fachat/cbm_ultipet/Board/A%2fV.kicad_sch

## KiCad design Board/A%2fV.kicad_sch (2025-08-31)

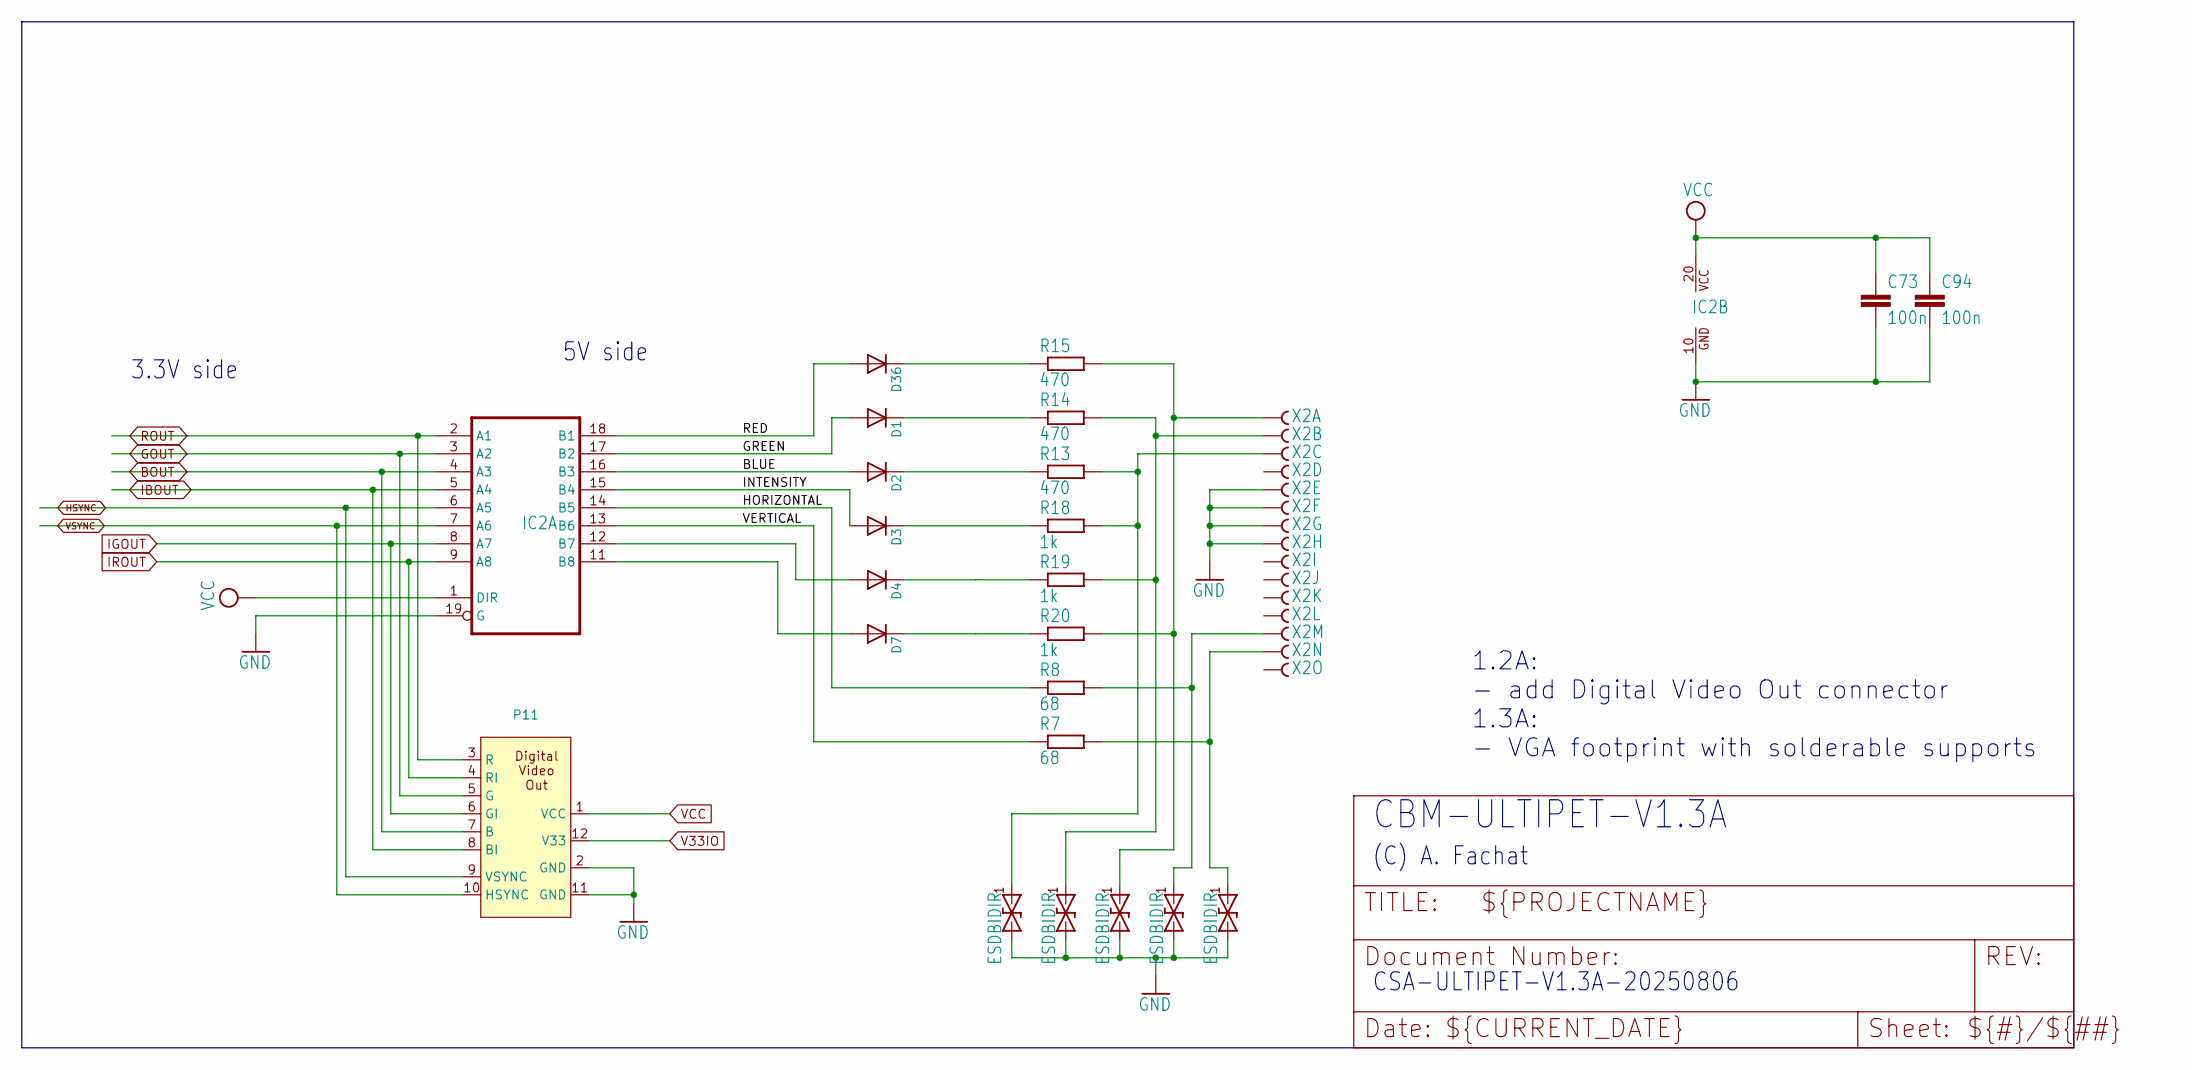
[picture p23: schematic A%2fV.kicad_sch]

Parts:
C73, C94: 100n; C025-025X050
D1, D2, D3, D4, D7, D36: 1N4448; D_DO-35_SOD27_P7.62mm_Horizontal
IC2: 74245DW; SOP-20_7.5x12.8mm_P1.27mm
P11: PinHeader_2x06_P2.54mm_Vertical
R7, R8: 68; 0204V
R13, R14, R15: 470; 0204V
R18, R19, R20: 1k; 0204V
UX5, UX6, UX8, UX10, UX11: ESDBIDIR; SOD323
X2: D-SUB15-HDR15RA; DSUB-15-HD_Socket_Horizontal_P2.29x2.54mm_EdgePinOffset8.35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

Connections:
BLUE: D2.2 (A), IC2.16 (B3)
BOUT: IC2.4 (A3), P11.7 (B)
GND: C73.2, C94.2, IC2.10 (GND), IC2.19 (G), P11.2 (GND), P11.11 (GND), UX5.1 (2), UX6.1 (2), UX8.1 (2), UX10.1 (2), UX11.1 (2), X2.5, X2.6, X2.7, X2.8
GOUT: IC2.3 (A2), P11.5 (G)
GREEN: D1.2 (A), IC2.17 (B2)
HORIZONTAL: IC2.14 (B5), R8.1
HSYNC: IC2.6 (A5), P11.9 (VSYNC)
IBOUT: IC2.5 (A4), P11.8 (BI)
IGOUT: IC2.8 (A7), P11.6 (GI)
INTENSITY: D3.2 (A), IC2.15 (B4)
IROUT: IC2.9 (A8), P11.4 (RI)
unnamed: D1.1 (K), R14.1
unnamed: D2.1 (K), R13.1
unnamed: D3.1 (K), R18.1
unnamed: D4.1 (K), R19.1
unnamed: D4.2 (A), IC2.12 (B7)
unnamed: D7.1 (K), R20.1
unnamed: D7.2 (A), IC2.11 (B8)
unnamed: D36.1 (K), R15.1
unnamed: R7.2, UX5.2 (1), X2.14
unnamed: R8.2, UX6.2 (1), X2.13
unnamed: R13.2, R18.2, UX11.2 (1), X2.3
unnamed: R14.2, R19.2, UX10.2 (1), X2.2
unnamed: R15.2, R20.2, UX8.2 (1), X2.1
RED: D36.2 (A), IC2.18 (B1)
ROUT: IC2.2 (A1), P11.3 (R)
V33IO: P11.12 (V33)
VCC: C73.1, C94.1, IC2.1 (DIR), IC2.20 (VCC), P11.1 (VCC)
VERTICAL: IC2.13 (B6), R7.1
VSYNC: IC2.7 (A6), P11.10 (HSYNC)

Notes on the sheet:
1.2A: - add Digital Video Out connector 1.3A: - VGA footprint with solderable supports
5V side
3.3V side
CSA-ULTIPET-V1.3A-20250806
CBM-ULTIPET-V1.3A
(C) A. Fachat
