fachat/cbm_ultipet/Board/Bus.kicad_sch

## KiCad design Board/Bus.kicad_sch (2025-08-31)

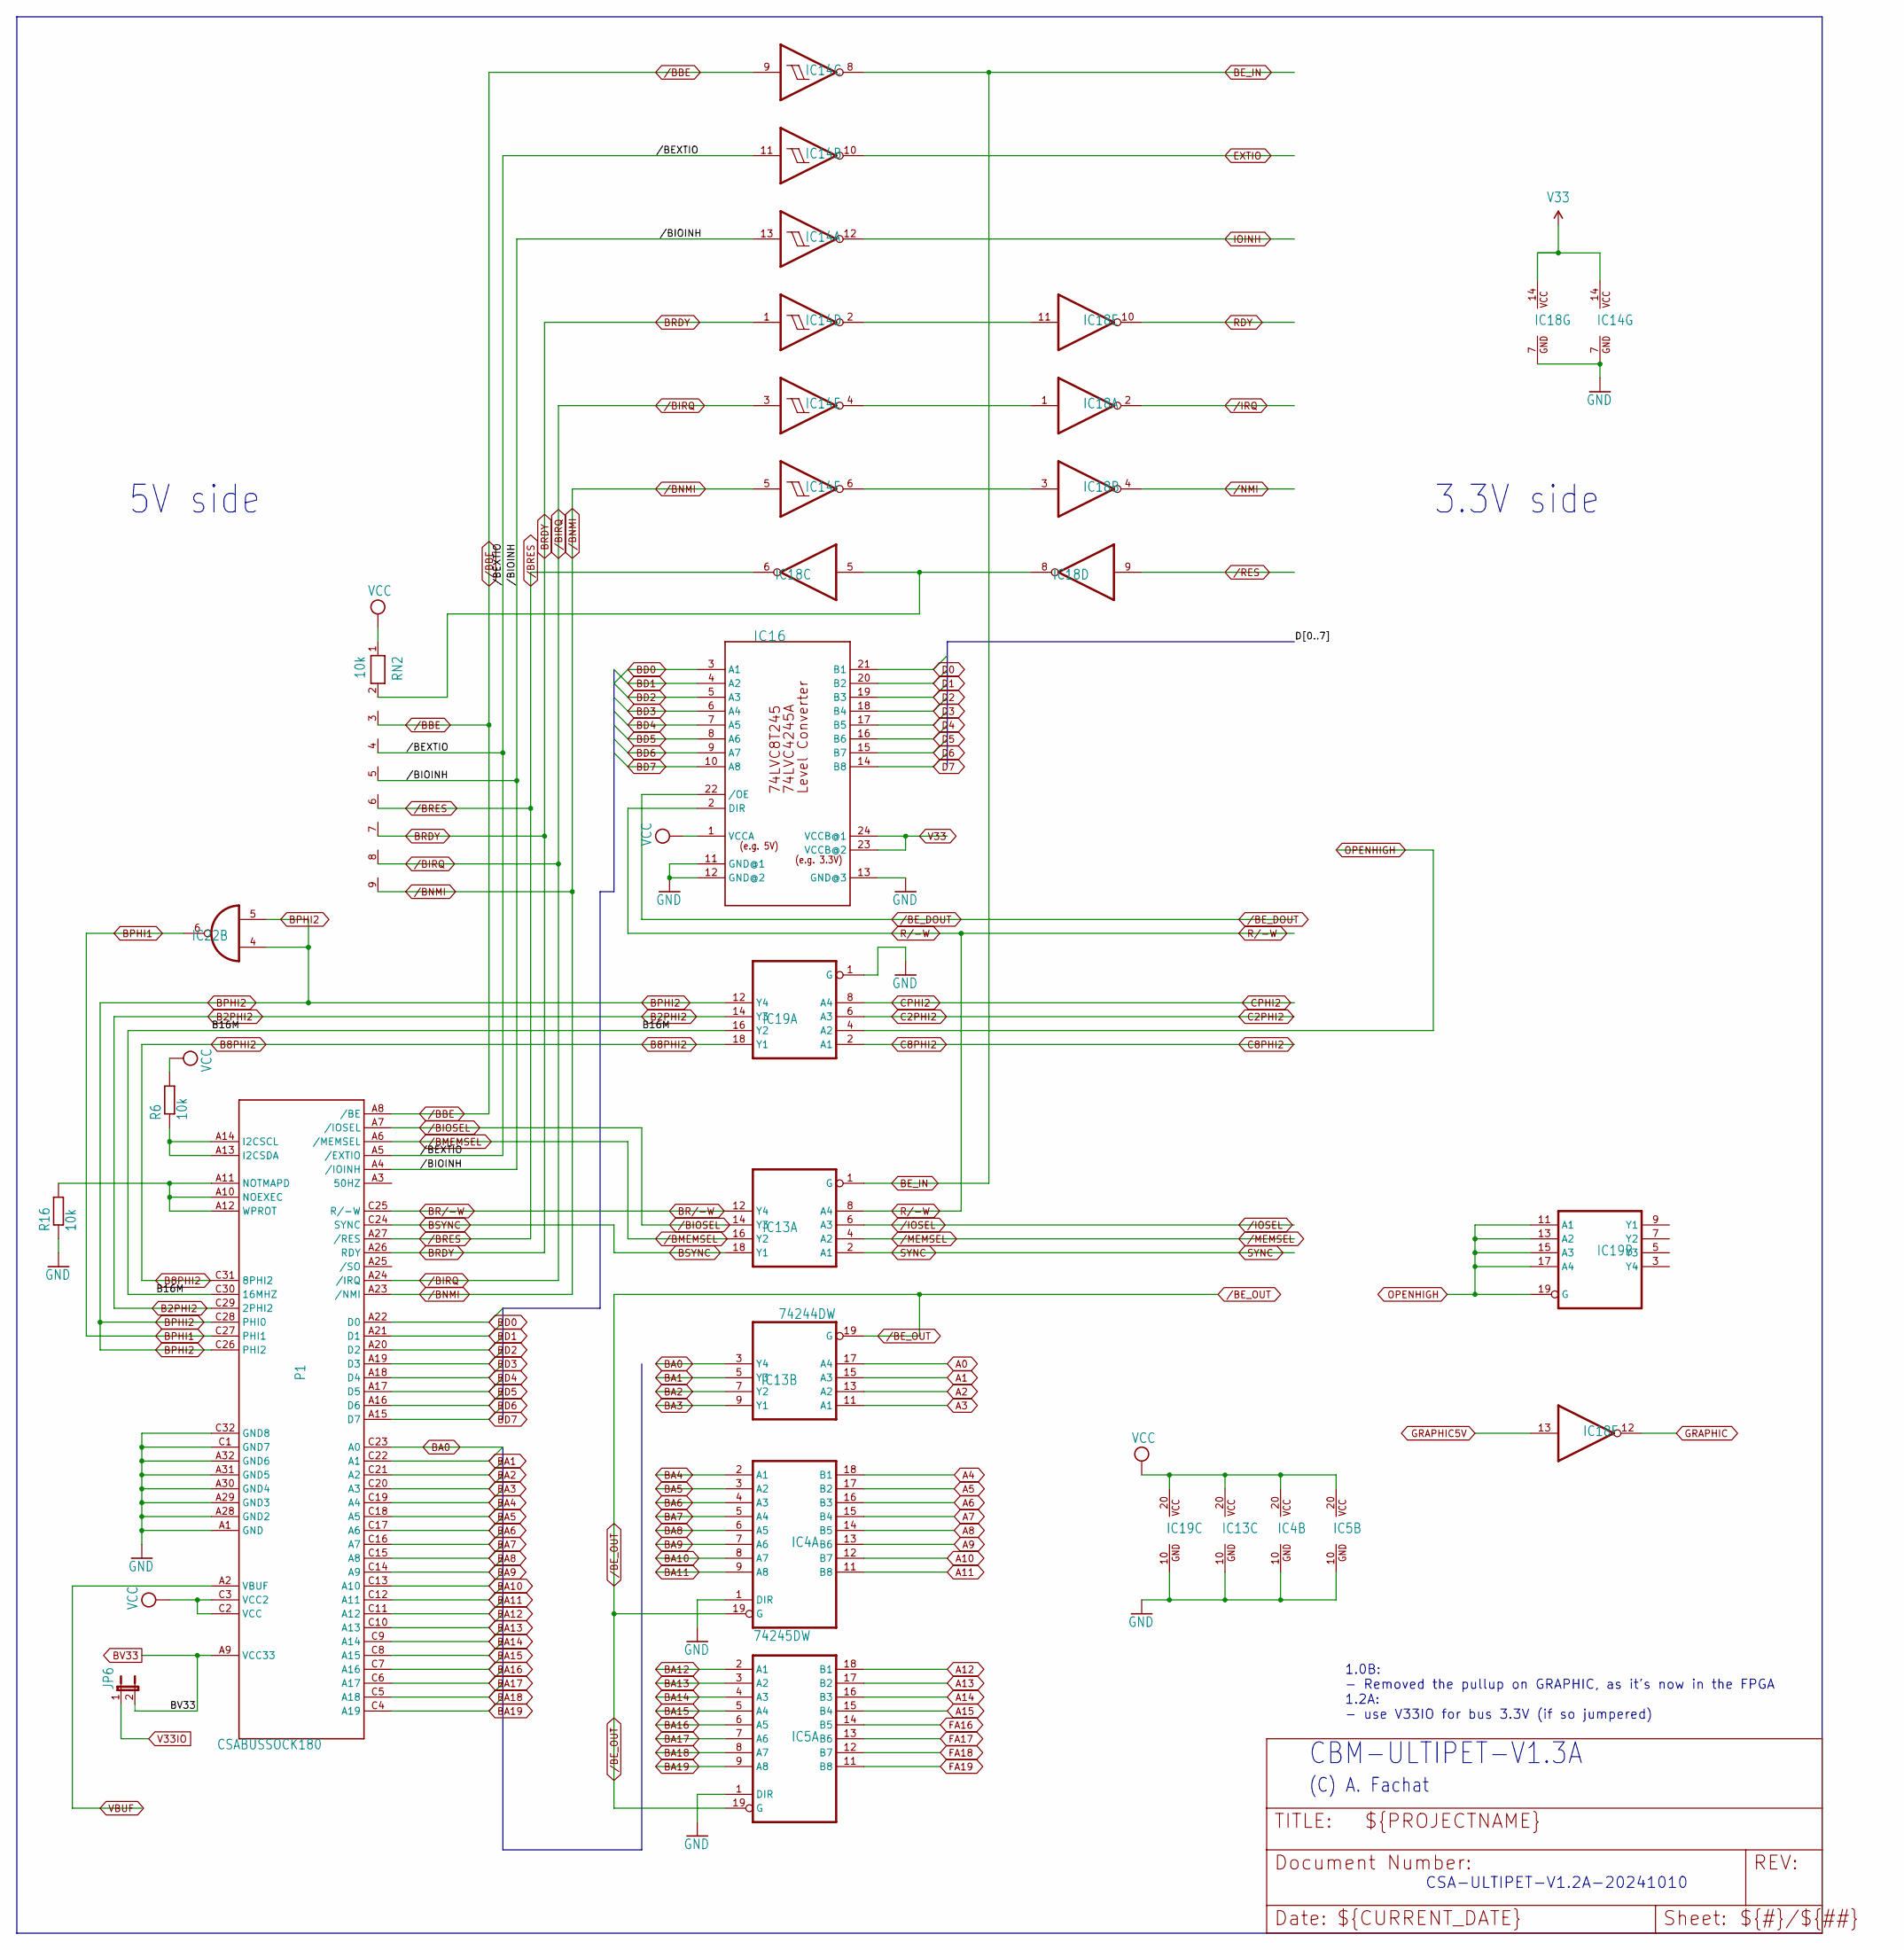
[picture p24: schematic Bus.kicad_sch]

Parts:
IC4, IC5: 74245DW; SOP-20_7.5x12.8mm_P1.27mm
IC13, IC19: 74244DW; SOP-20_7.5x12.8mm_P1.27mm
IC14: 74LVC14; SO14
IC16: 74LVC8T245SO24; SO24L
IC18: 74LVC06; SO14
IC22: 7400N; DIP-14_W7.62mm_Socket_LongPads
JP6: JP1E; JP1
P1: CSABUSSOCK180
R6, R16: 10k; 0204_5
RN2: 10k; RN-9

Connections:
/BBE: IC14.9 (I), P1.A8 (/BE), RN2.3
/BEXTIO: IC14.11 (I), P1.A5 (/EXTIO), RN2.4
/BE_DOUT: IC16.22 (/OE)
/BE_OUT: IC4.19 (G), IC5.19 (G), IC13.19 (G)
/BIOINH: IC14.13 (I), P1.A4 (/IOINH), RN2.5
/BIOSEL: IC13.14 (Y3), P1.A7 (/IOSEL)
/BIRQ: IC14.3 (I), P1.A24 (/IRQ), RN2.8
/BMEMSEL: IC13.16 (Y2), P1.A6 (/MEMSEL)
/BNMI: IC14.5 (I), P1.A23 (/NMI), RN2.9
/BRES: IC18.6 (O), P1.A27 (/RES), RN2.6
/IOSEL: IC13.6 (A3)
/IRQ: IC18.2 (O)
/MEMSEL: IC13.4 (A2)
/NMI: IC18.4 (O)
/RES: IC18.9 (I)
A0: IC13.17 (A4)
A1: IC13.15 (A3)
A2: IC13.13 (A2)
A3: IC13.11 (A1)
A4: IC4.18 (B1)
A5: IC4.17 (B2)
A6: IC4.16 (B3)
A7: IC4.15 (B4)
A8: IC4.14 (B5)
A9: IC4.13 (B6)
A10: IC4.12 (B7)
A11: IC4.11 (B8)
A12: IC5.18 (B1)
A13: IC5.17 (B2)
A14: IC5.16 (B3)
A15: IC5.15 (B4)
B2PHI2: IC19.14 (Y3), P1.C29 (2PHI2)
B8PHI2: IC19.18 (Y1), P1.C31 (8PHI2)
B16M: IC19.16 (Y2), P1.C30 (16MHZ)
BA0: IC13.3 (Y4), P1.C23 (A0)
BA1: IC13.5 (Y3), P1.C22 (A1)
BA2: IC13.7 (Y2), P1.C21 (A2)
BA3: IC13.9 (Y1), P1.C20 (A3)
BA4: IC4.2 (A1), P1.C19 (A4)
BA5: IC4.3 (A2), P1.C18 (A5)
BA6: IC4.4 (A3), P1.C17 (A6)
BA7: IC4.5 (A4), P1.C16 (A7)
BA8: IC4.6 (A5), P1.C15 (A8)
BA9: IC4.7 (A6), P1.C14 (A9)
BA10: IC4.8 (A7), P1.C13 (A10)
BA11: IC4.9 (A8), P1.C12 (A11)
BA12: IC5.2 (A1), P1.C11 (A12)
BA13: IC5.3 (A2), P1.C10 (A13)
BA14: IC5.4 (A3), P1.C9 (A14)
BA15: IC5.5 (A4), P1.C8 (A15)
BA16: IC5.6 (A5), P1.C7 (A16)
BA17: IC5.7 (A6), P1.C6 (A17)
BA18: IC5.8 (A7), P1.C5 (A18)
BA19: IC5.9 (A8), P1.C4 (A19)
BD0: IC16.3 (A1), P1.A22 (D0)
BD1: IC16.4 (A2), P1.A21 (D1)
BD2: IC16.5 (A3), P1.A20 (D2)
BD3: IC16.6 (A4), P1.A19 (D3)
BD4: IC16.7 (A5), P1.A18 (D4)
BD5: IC16.8 (A6), P1.A17 (D5)
BD6: IC16.9 (A7), P1.A16 (D6)
BD7: IC16.10 (A8), P1.A15 (D7)
BE_IN: IC13.1 (G), IC14.8 (O)
BPHI1: IC22.6 (O), P1.C27 (PHI1)
BPHI2: IC19.12 (Y4), IC22.4 (I0), IC22.5 (I1), P1.C26 (PHI2), P1.C28 (PHI0)
BR/-W: IC13.12 (Y4), P1.C25 (R/-W)
BRDY: IC14.1 (I), P1.A26 (RDY), RN2.7
BSYNC: IC13.18 (Y1), P1.C24 (SYNC)
BV33: JP6.2, P1.A9 (VCC33)
C2PHI2: IC19.6 (A3)
C8PHI2: IC19.2 (A1)
CPHI2: IC19.8 (A4)
D0: IC16.21 (B1)
D1: IC16.20 (B2)
D2: IC16.19 (B3)
D3: IC16.18 (B4)
D4: IC16.17 (B5)
D5: IC16.16 (B6)
D6: IC16.15 (B7)
D7: IC16.14 (B8)
EXTIO: IC14.10 (O)
FA16: IC5.14 (B5)
FA17: IC5.13 (B6)
FA18: IC5.12 (B7)
FA19: IC5.11 (B8)
GND: IC4.1 (DIR), IC4.10 (GND), IC5.1 (DIR), IC5.10 (GND), IC13.10 (GND), IC14.7 (GND), IC16.11 (GND@1), IC16.12 (GND@2), IC16.13 (GND@3), IC18.7 (GND), IC19.1 (G), IC19.10 (GND), P1.A1 (GND), P1.A28 (GND2), P1.A29 (GND3), P1.A30 (GND4), P1.A31 (GND5), P1.A32 (GND6), P1.C1 (GND7), P1.C32 (GND8), R16.1
GRAPHIC: IC18.12 (O)
GRAPHIC5V: IC18.13 (I)
IOINH: IC14.12 (O)
unnamed: IC14.2 (O), IC18.11 (I)
unnamed: IC14.4 (O), IC18.1 (I)
unnamed: IC14.6 (O), IC18.3 (I)
unnamed: IC18.5 (I), IC18.8 (O), RN2.2
unnamed: P1.A10 (NOEXEC), P1.A11 (NOTMAPD), P1.A12 (WPROT), R16.2
unnamed: P1.A13 (I2CSDA), P1.A14 (I2CSCL), R6.1
OPENHIGH: IC19.4 (A2), IC19.11 (A1), IC19.13 (A2), IC19.15 (A3), IC19.17 (A4), IC19.19 (G)
R/-W: IC13.8 (A4), IC16.2 (DIR)
RDY: IC18.10 (O)
SYNC: IC13.2 (A1)
V33: IC14.14 (VCC), IC16.23 (VCCB@2), IC16.24 (VCCB@1), IC18.14 (VCC)
V33IO: JP6.1
VBUF: P1.A2 (VBUF)
VCC: IC4.20 (VCC), IC5.20 (VCC), IC13.20 (VCC), IC16.1 (VCCA), IC19.20 (VCC), P1.C2 (VCC), P1.C3 (VCC2), R6.2, RN2.1

Notes on the sheet:
CSA-ULTIPET-V1.2A-20241010
5V side
(C) A. Fachat
3.3V side
1.0B: - Removed the pullup on GRAPHIC, as it's now in the FPGA 1.2A: - use V33IO for bus 3.3V (if so jumpered)
CBM-ULTIPET-V1.3A
