fachat/cbm_ultipet/Board/CPU,_FPGA,_FRAM.kicad_sch

## KiCad design Board/CPU,_FPGA,_FRAM.kicad_sch (2026-05-08)

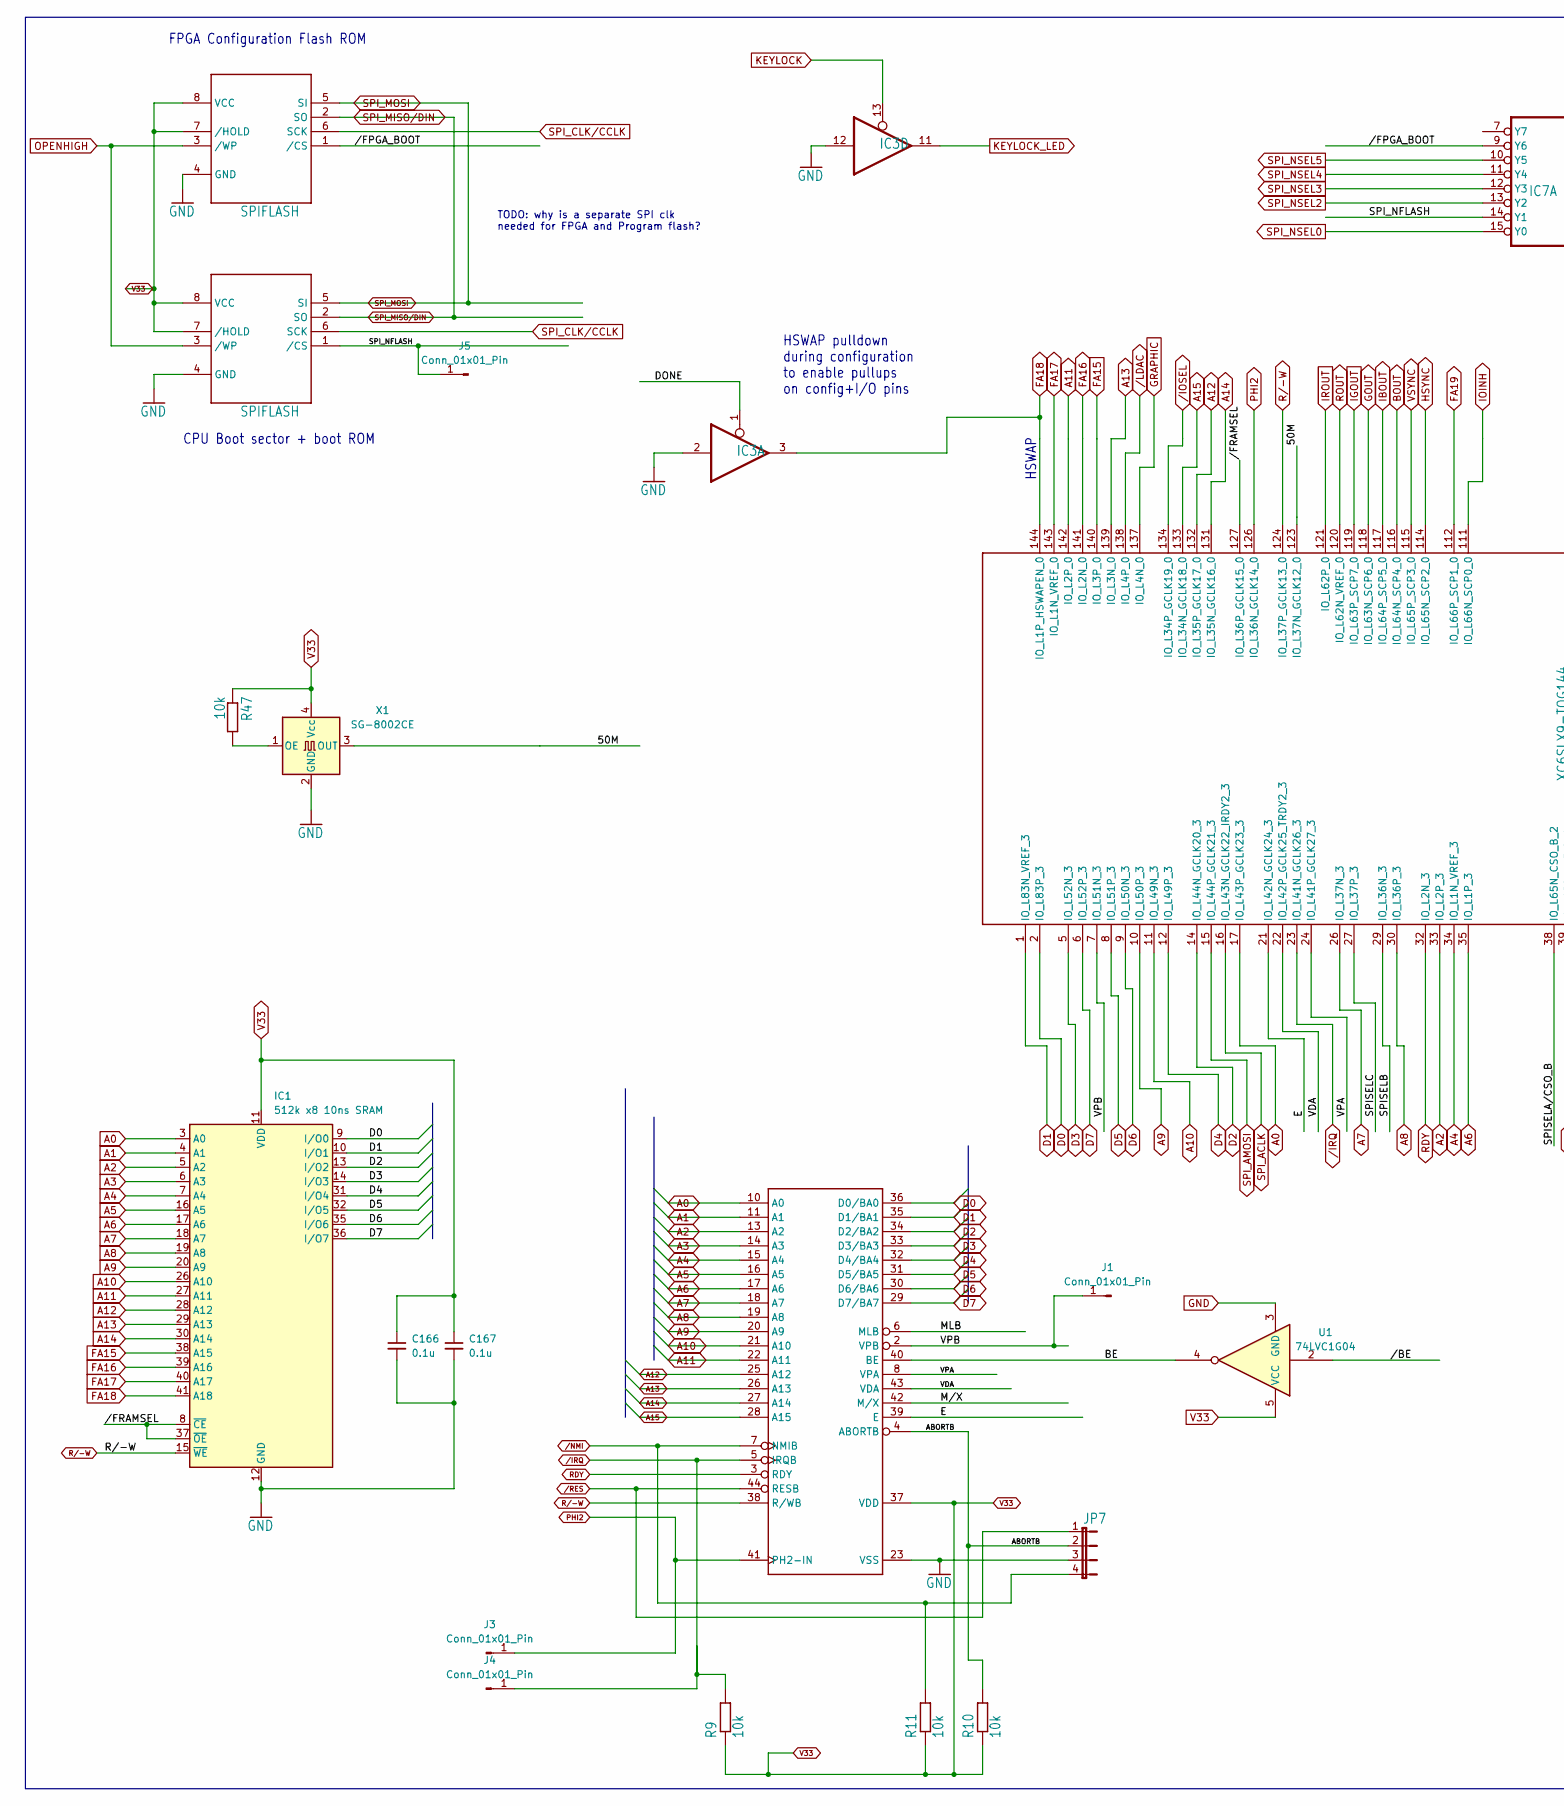
[picture p25: schematic CPU,_FPGA,_FRAM.kicad_sch, part in row 1, column 1]

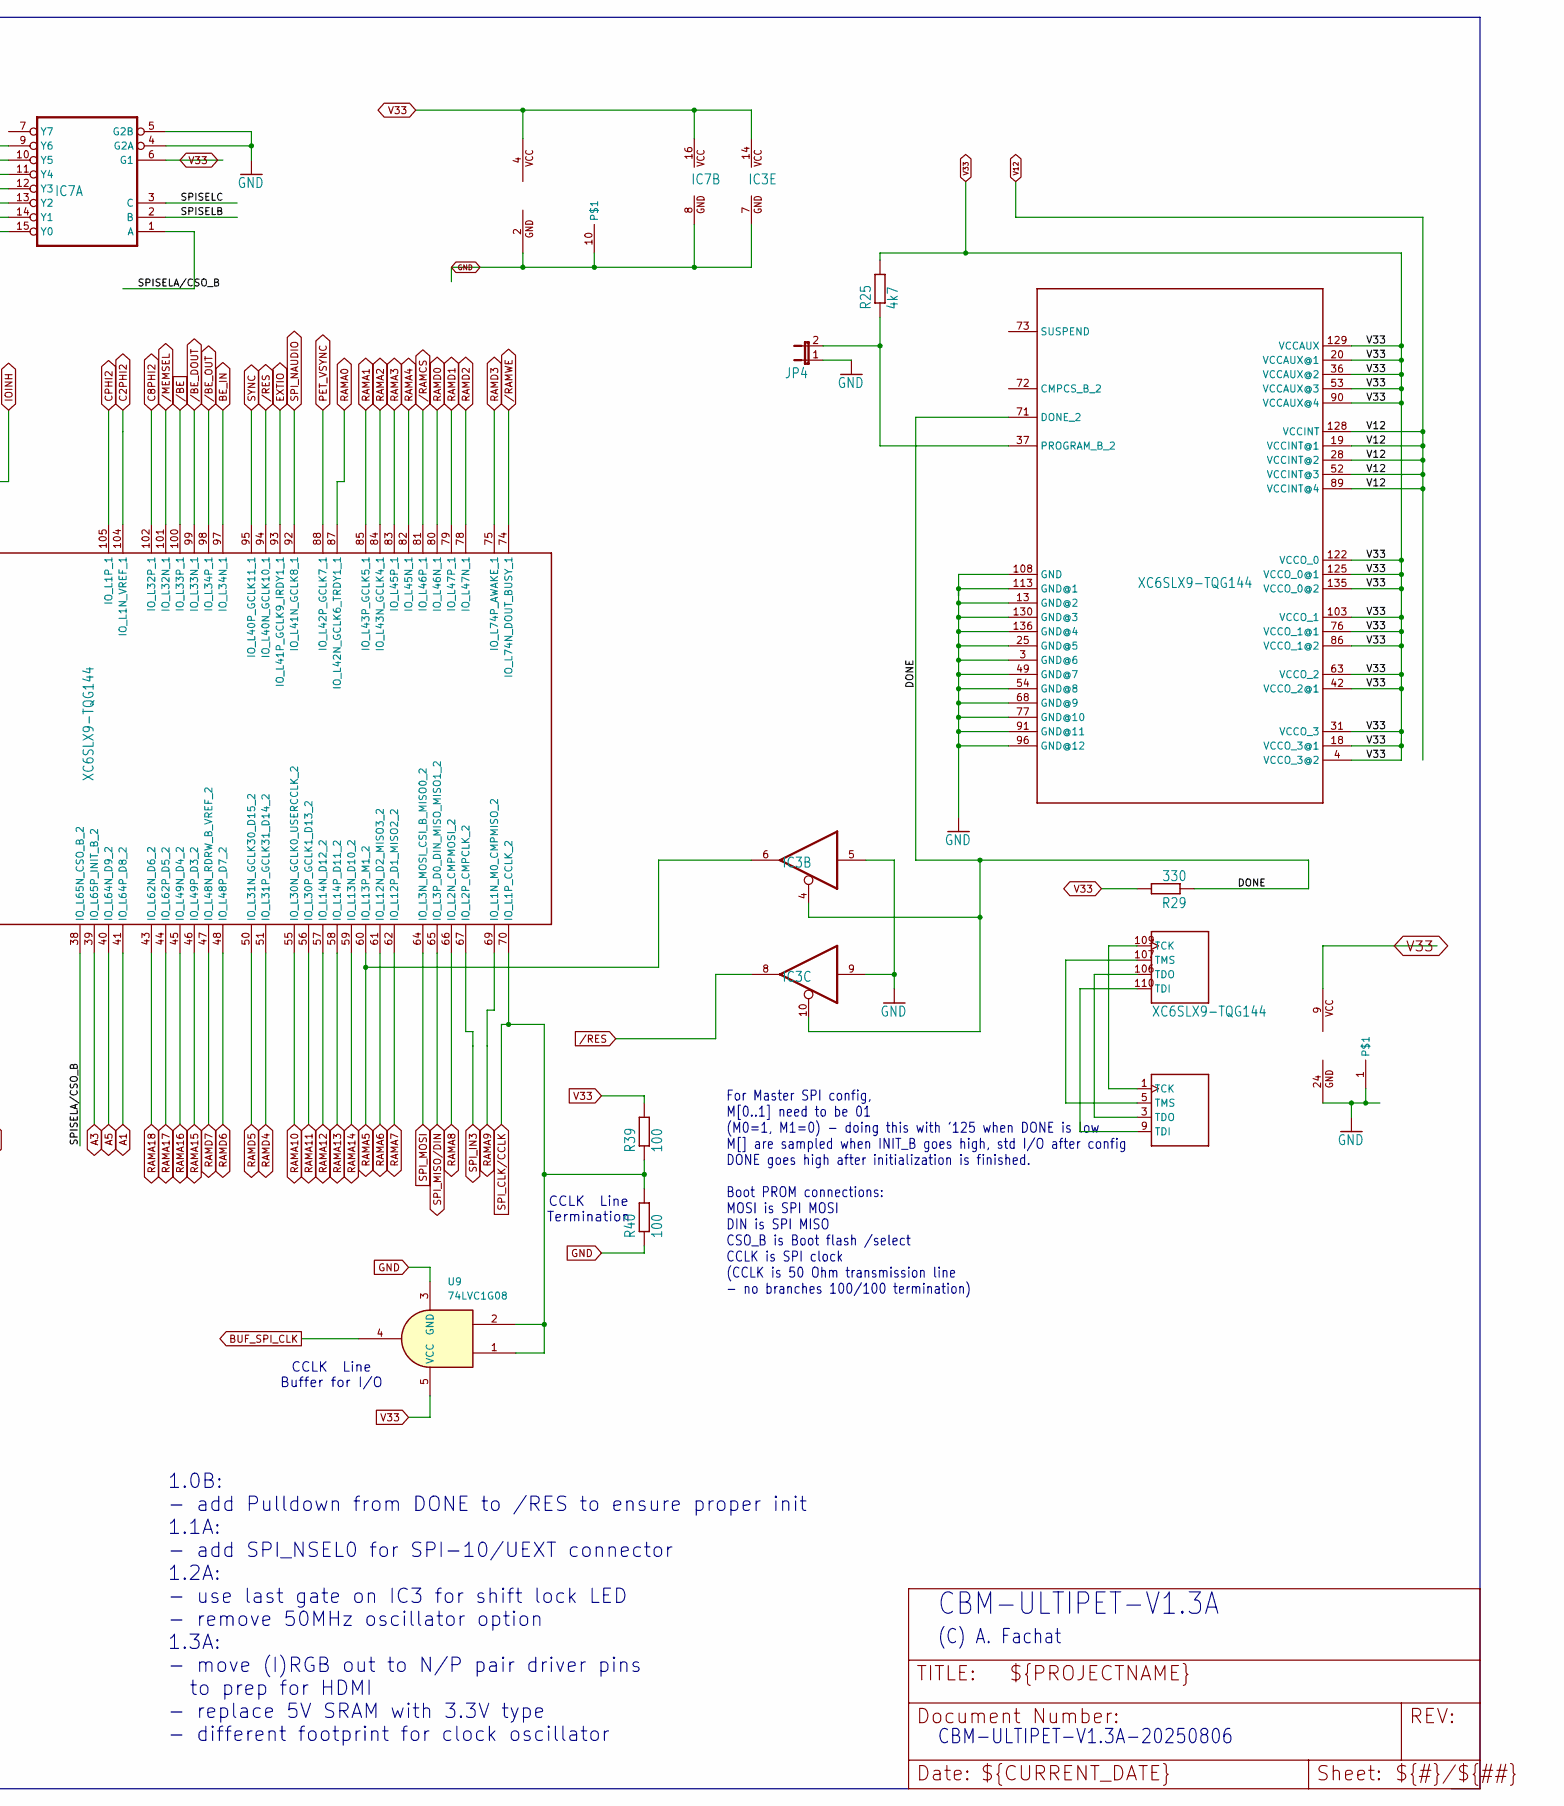
[picture p26: schematic CPU,_FPGA,_FRAM.kicad_sch, part in row 1, column 2]

Parts:
C166, C167: 0.1u; C_0603_1608Metric
IC1: 512k x8 10ns SRAM; TSOP-II-44_10.16x18.41mm_P0.8mm
IC3: 74LVC125D; SO14@1
IC7: 74LVC138D; SO16
J1, J3, J4, J5: Conn_01x01_Pin; PinHeader_1x01_P2.54mm_Vertical
JP4: JP1E; JP1
JP7: JP4E; JP4
R9, R10, R11: 10k; 0207_2V
R25: 4k7; 0207_2V
R29: 330; 0207_2V
R39, R40: 100; 0207_2V
R47: 10k; R_0805_2012Metric_Pad1.20x1.40mm_HandSolder
U1: 74LVC1G04; SOT-23-5
U9: 74LVC1G08; SOT-23-5
UX1: W65C816SPLCC; PLCC-44_THT-Socket
UX4, UX18: SPIFLASH; DIP-8_W7.62mm_Socket_LongPads
UX7: XILINXPROG; FLAT10BOX
UX19: XC6SLX9-TQG144; TQFP-144_20x20mm_P0.5mm
X1: SG-8002CE; Oscillator_SMD_SeikoEpson_SG8002CE-4Pin_3.2x2.5mm

Connections:
50M: UX19.123 (IO_L37N_GCLK12_0), X1.3 (OUT)
/BE_DOUT: UX19.99 (IO_L33N_1)
/BE_OUT: UX19.98 (IO_L34P_1)
/FPGA_BOOT: IC7.9 (Y6), UX18.1 (/CS)
/FRAMSEL: UX19.127 (IO_L36P_GCLK15_0)
/IOSEL: UX19.134 (IO_L34P_GCLK19_0)
/IRQ: J4.1, R9.2, UX1.5 (IRQB), UX19.23 (IO_L41N_GCLK26_3)
/LDAC: UX19.138 (IO_L4P_0)
/MEMSEL: UX19.101 (IO_L32N_1)
/NMI: JP7.4, R11.2, UX1.7 (NMIB)
/RAMWE: UX19.74 (IO_L74N_DOUT_BUSY_1)
/RES: JP7.1, UX1.44 (RESB), UX19.94 (IO_L40N_GCLK10_1)
A0: IC1.3 (A0), UX1.10 (A0), UX19.17 (IO_L43P_GCLK23_3)
A1: IC1.4 (A1), UX1.11 (A1), UX19.41 (IO_L64P_D8_2)
A2: IC1.5 (A2), UX1.13 (A2), UX19.33 (IO_L2P_3)
A3: IC1.6 (A3), UX1.14 (A3), UX19.39 (IO_L65P_INIT_B_2)
A4: IC1.7 (A4), UX1.15 (A4), UX19.34 (IO_L1N_VREF_3)
A5: IC1.16 (A5), UX1.16 (A5), UX19.40 (IO_L64N_D9_2)
A6: IC1.17 (A6), UX1.17 (A6), UX19.35 (IO_L1P_3)
A7: IC1.18 (A7), UX1.18 (A7), UX19.26 (IO_L37N_3)
A8: IC1.19 (A8), UX1.19 (A8), UX19.30 (IO_L36P_3)
A9: IC1.20 (A9), UX1.20 (A9), UX19.10 (IO_L50P_3)
A10: IC1.26 (A10), UX1.21 (A10), UX19.11 (IO_L49N_3)
A11: IC1.27 (A11), UX1.22 (A11), UX19.142 (IO_L2P_0)
A12: IC1.28 (A12), UX1.25 (A12), UX19.132 (IO_L35P_GCLK17_0)
A13: IC1.29 (A13), UX1.26 (A13), UX19.139 (IO_L3N_0)
A14: IC1.30 (A14), UX1.27 (A14), UX19.131 (IO_L35N_GCLK16_0)
A15: UX1.28 (A15), UX19.133 (IO_L34N_GCLK18_0)
ABORTB: JP7.2, R10.2, UX1.4 (ABORTB)
BE: U1.4, UX1.40 (BE)
BE_IN: UX19.97 (IO_L34N_1)
BOUT: UX19.116 (IO_L64N_SCP4_0)
BUF_SPI_CLK: U9.4
C2PHI2: UX19.104 (IO_L1N_VREF_1)
C8PHI2: UX19.102 (IO_L32P_1)
CPHI2: UX19.105 (IO_L1P_1)
D0: IC1.9 (I/O0), UX1.36 (D0/BA0), UX19.2 (IO_L83P_3)
D1: IC1.10 (I/O1), UX1.35 (D1/BA1), UX19.1 (IO_L83N_VREF_3)
D2: IC1.13 (I/O2), UX1.34 (D2/BA2), UX19.14 (IO_L44N_GCLK20_3)
D3: IC1.14 (I/O3), UX1.33 (D3/BA3), UX19.5 (IO_L52N_3)
D4: IC1.31 (I/O4), UX1.32 (D4/BA4), UX19.12 (IO_L49P_3)
D5: IC1.32 (I/O5), UX1.31 (D5/BA5), UX19.8 (IO_L51P_3)
D6: IC1.35 (I/O6), UX1.30 (D6/BA6), UX19.9 (IO_L50N_3)
D7: IC1.36 (I/O7), UX1.29 (D7/BA7), UX19.6 (IO_L52P_3)
DONE: IC3.1 (OE), IC3.4 (OE), IC3.10 (OE), R29.1, UX19.71 (DONE_2)
E: UX1.39 (E), UX19.21 (IO_L42N_GCLK24_3)
EXTIO: UX19.93 (IO_L41P_GCLK9_IRDY1_1)
FA15: IC1.38 (A15), UX19.140 (IO_L3P_0)
FA16: IC1.39 (A16), UX19.141 (IO_L2N_0)
FA17: IC1.40 (A17), UX19.143 (IO_L1N_VREF_0)
FA18: IC1.41 (A18), IC3.3 (O), UX19.144 (IO_L1P_HSWAPEN_0)
FA19: UX19.112 (IO_L66P_SCP1_0)
GND: C166.2, C167.2, IC1.12 (GND), IC1.34 (GND), IC3.2 (I), IC3.5 (I), IC3.7 (GND), IC3.9 (I), IC3.12 (I), IC7.4 (G2A), IC7.5 (G2B), IC7.8 (GND), JP4.1, JP7.3, R40.1, U1.3 (GND), U9.3 (GND), UX1.1, UX1.23 (VSS), UX1.24 (GND), UX4.4 (GND), UX7.2 (GND), UX7.10, UX18.4 (GND), UX19.3 (GND@6), UX19.13 (GND@2), UX19.25 (GND@5), UX19.49 (GND@7), UX19.54 (GND@8), UX19.68 (GND@9), UX19.77 (GND@10), UX19.91 (GND@11), UX19.96 (GND@12), UX19.108 (GND), UX19.113 (GND@1), UX19.130 (GND@3), UX19.136 (GND@4), X1.2 (GND)
GOUT: UX19.118 (IO_L63N_SCP6_0)
GRAPHIC: UX19.137 (IO_L4N_0)
HSYNC: UX19.114 (IO_L65N_SCP2_0)
IBOUT: UX19.117 (IO_L64P_SCP5_0)
IGOUT: UX19.119 (IO_L63P_SCP7_0)
IOINH: UX19.111 (IO_L66N_SCP0_0)
IROUT: UX19.121 (IO_L62P_0)
KEYLOCK: IC3.13 (OE)
KEYLOCK_LED: IC3.11 (O)
MLB: UX1.6 (MLB)
M/X: UX1.42 (M/X)
unnamed: JP4.2, R25.1, UX19.37 (PROGRAM_B_2)
unnamed: R47.2, X1.1 (OE)
unnamed: UX7.3 (TDO), UX19.106 (TDO)
unnamed: UX7.5 (TMS), UX19.107 (TMS)
unnamed: UX7.1 (TCK), UX19.109 (TCK)
unnamed: UX7.9 (TDI), UX19.110 (TDI)
OPENHIGH: UX4.3 (/WP), UX18.3 (/WP)
PET_VSYNC: UX19.88 (IO_L42P_GCLK7_1)
PHI2: J3.1, UX1.41 (PH2-IN), UX19.126 (IO_L36N_GCLK14_0)
R/-W: IC1.15 (~WE), UX1.38 (R/WB), UX19.124 (IO_L37P_GCLK13_0)
RAMA0: UX19.87 (IO_L42N_GCLK6_TRDY1_1)
RAMA1: UX19.85 (IO_L43P_GCLK5_1)
RAMA2: UX19.84 (IO_L43N_GCLK4_1)
RAMA3: UX19.83 (IO_L45P_1)
RAMA4: UX19.82 (IO_L45N_1)
RAMA5: IC3.6 (O), UX19.60 (IO_L13P_M1_2)
RAMA6: UX19.61 (IO_L12N_D2_MISO3_2)
RAMA7: UX19.62 (IO_L12P_D1_MISO2_2)
RAMA8: UX19.66 (IO_L2N_CMPMOSI_2)
RAMA9: UX19.69 (IO_L1N_M0_CMPMISO_2)
RAMA10: UX19.55 (IO_L30N_GCLK0_USERCCLK_2)
RAMA11: UX19.56 (IO_L30P_GCLK1_D13_2)
RAMA12: UX19.57 (IO_L14N_D12_2)
RAMA13: UX19.58 (IO_L14P_D11_2)
RAMA14: UX19.59 (IO_L13N_D10_2)
RAMA15: UX19.46 (IO_L49P_D3_2)
RAMA16: UX19.45 (IO_L49N_D4_2)
RAMA17: UX19.44 (IO_L62P_D5_2)
RAMA18: UX19.43 (IO_L62N_D6_2)
RAMD0: UX19.80 (IO_L46N_1)
RAMD1: UX19.79 (IO_L47P_1)
RAMD2: UX19.78 (IO_L47N_1)
RAMD3: UX19.75 (IO_L74P_AWAKE_1)
RAMD4: UX19.51 (IO_L31P_GCLK31_D14_2)
RAMD5: UX19.50 (IO_L31N_GCLK30_D15_2)
RAMD6: UX19.48 (IO_L48P_D7_2)
RAMD7: UX19.47 (IO_L48N_RDRW_B_VREF_2)
RDY: UX1.3 (RDY), UX19.32 (IO_L2N_3)
ROUT: UX19.120 (IO_L62N_VREF_0)
SPISELA/CSO_B: IC7.1 (A), UX19.38 (IO_L65N_CSO_B_2)
SPISELB: IC7.2 (B), UX19.29 (IO_L36N_3)
SPISELC: IC7.3 (C), UX19.27 (IO_L37P_3)
SPI_ACLK: UX19.16 (IO_L43N_GCLK22_IRDY2_3)
SPI_AMOSI: UX19.15 (IO_L44P_GCLK21_3)
SPI_CLK/CCLK: R39.1, R40.2, U9.1, U9.2, UX18.6 (SCK), UX19.70 (IO_L1P_CCLK_2)
SPI_CLK/CCLK: UX4.6 (SCK)
SPI_IN3: UX19.67 (IO_L2P_CMPCLK_2)
SPI_MISO/DIN: UX4.2 (SO), UX18.2 (SO), UX19.65 (IO_L3P_D0_DIN_MISO_MISO1_2)
SPI_MOSI: UX4.5 (SI), UX18.5 (SI), UX19.64 (IO_L3N_MOSI_CSI_B_MISO0_2)
SPI_NAUDIO: UX19.92 (IO_L41N_GCLK8_1)
SPI_NFLASH: IC7.14 (Y1), J5.1, UX4.1 (/CS)
SPI_NSEL0: IC7.15 (Y0)
SPI_NSEL2: IC7.13 (Y2)
SPI_NSEL3: IC7.12 (Y3)
SPI_NSEL4: IC7.11 (Y4)
SPI_NSEL5: IC7.10 (Y5)
SYNC: UX19.95 (IO_L40P_GCLK11_1)
V12: UX19.19 (VCCINT@1), UX19.28 (VCCINT@2), UX19.52 (VCCINT@3), UX19.89 (VCCINT@4), UX19.128 (VCCINT)
V33: C166.1, C167.1, IC1.11 (VDD), IC1.33 (VDD), IC3.14 (VCC), IC7.6 (G1), IC7.16 (VCC), R9.1, R10.1, R11.1, R25.2, R29.2, R39.2, R47.1, U1.5 (VCC), U9.5 (VCC), UX1.9 (VCC), UX1.37 (VDD), UX4.7 (/HOLD), UX4.8 (VCC), UX7.4 (VCC), UX18.7 (/HOLD), UX18.8 (VCC), UX19.4 (VCCO_3@2), UX19.18 (VCCO_3@1), UX19.20 (VCCAUX@1), UX19.31 (VCCO_3), UX19.36 (VCCAUX@2), UX19.42 (VCCO_2@1), UX19.53 (VCCAUX@3), UX19.63 (VCCO_2), UX19.76 (VCCO_1@1), UX19.86 (VCCO_1@2), UX19.90 (VCCAUX@4), UX19.103 (VCCO_1), UX19.122 (VCCO_0), UX19.125 (VCCO_0@1), UX19.129 (VCCAUX), UX19.135 (VCCO_0@2), X1.4 (Vcc)
VDA: UX1.43 (VDA), UX19.22 (IO_L42P_GCLK25_TRDY2_3)
VPA: UX1.8 (VPA), UX19.24 (IO_L41P_GCLK27_3)
VPB: J1.1, UX1.2 (VPB), UX19.7 (IO_L51N_3)
VSYNC: UX19.115 (IO_L65P_SCP3_0)
/BE: U1.2, UX19.100 (IO_L33P_1)
/FRAMSEL: IC1.8 (~CE), IC1.37 (~OE)
/RAMCS: UX19.81 (IO_L46P_1)
/RES: IC3.8 (O)

Notes on the sheet:
TODO: why is a separate SPI clk needed for FPGA and Program flash?
CPU Boot sector + boot ROM
1.0B: - add Pulldown from DONE to /RES to ensure proper init 1.1A: - add SPI_NSEL0 for SPI-10/UEXT connector 1.2A: - use last gate on IC3 for shift lock LED - remove 50MHz oscillator option 1.3A: - move (I)RGB out to N/P pair driver pins to prep for HDMI - replace 5V SRAM with 3.3V type - different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
CCLK Line Termination
CBM-ULTIPET-V1.3A
CBM-ULTIPET-V1.3A-20250806
CCLK Line Buffer for I/O
(C) A. Fachat
HSWAP pulldown during configuration to enable pullups on config+I/O pins
For Master SPI config, M[0..1] need to be 01 (M0=1, M1=0) - doing this with '125 when DONE is low M[] are sampled when INIT_B goes high, std I/O after config DONE goes high after initialization is finished. Boot PROM connections: MOSI is SPI MOSI DIN is SPI MISO CSO_B is Boot flash /select CCLK is 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
HSWAP
FPGA Configuration Flash ROM
