fachat/cbm_ultipet/Board/FastIEC.kicad_sch

## KiCad design Board/FastIEC.kicad_sch (2025-08-31)

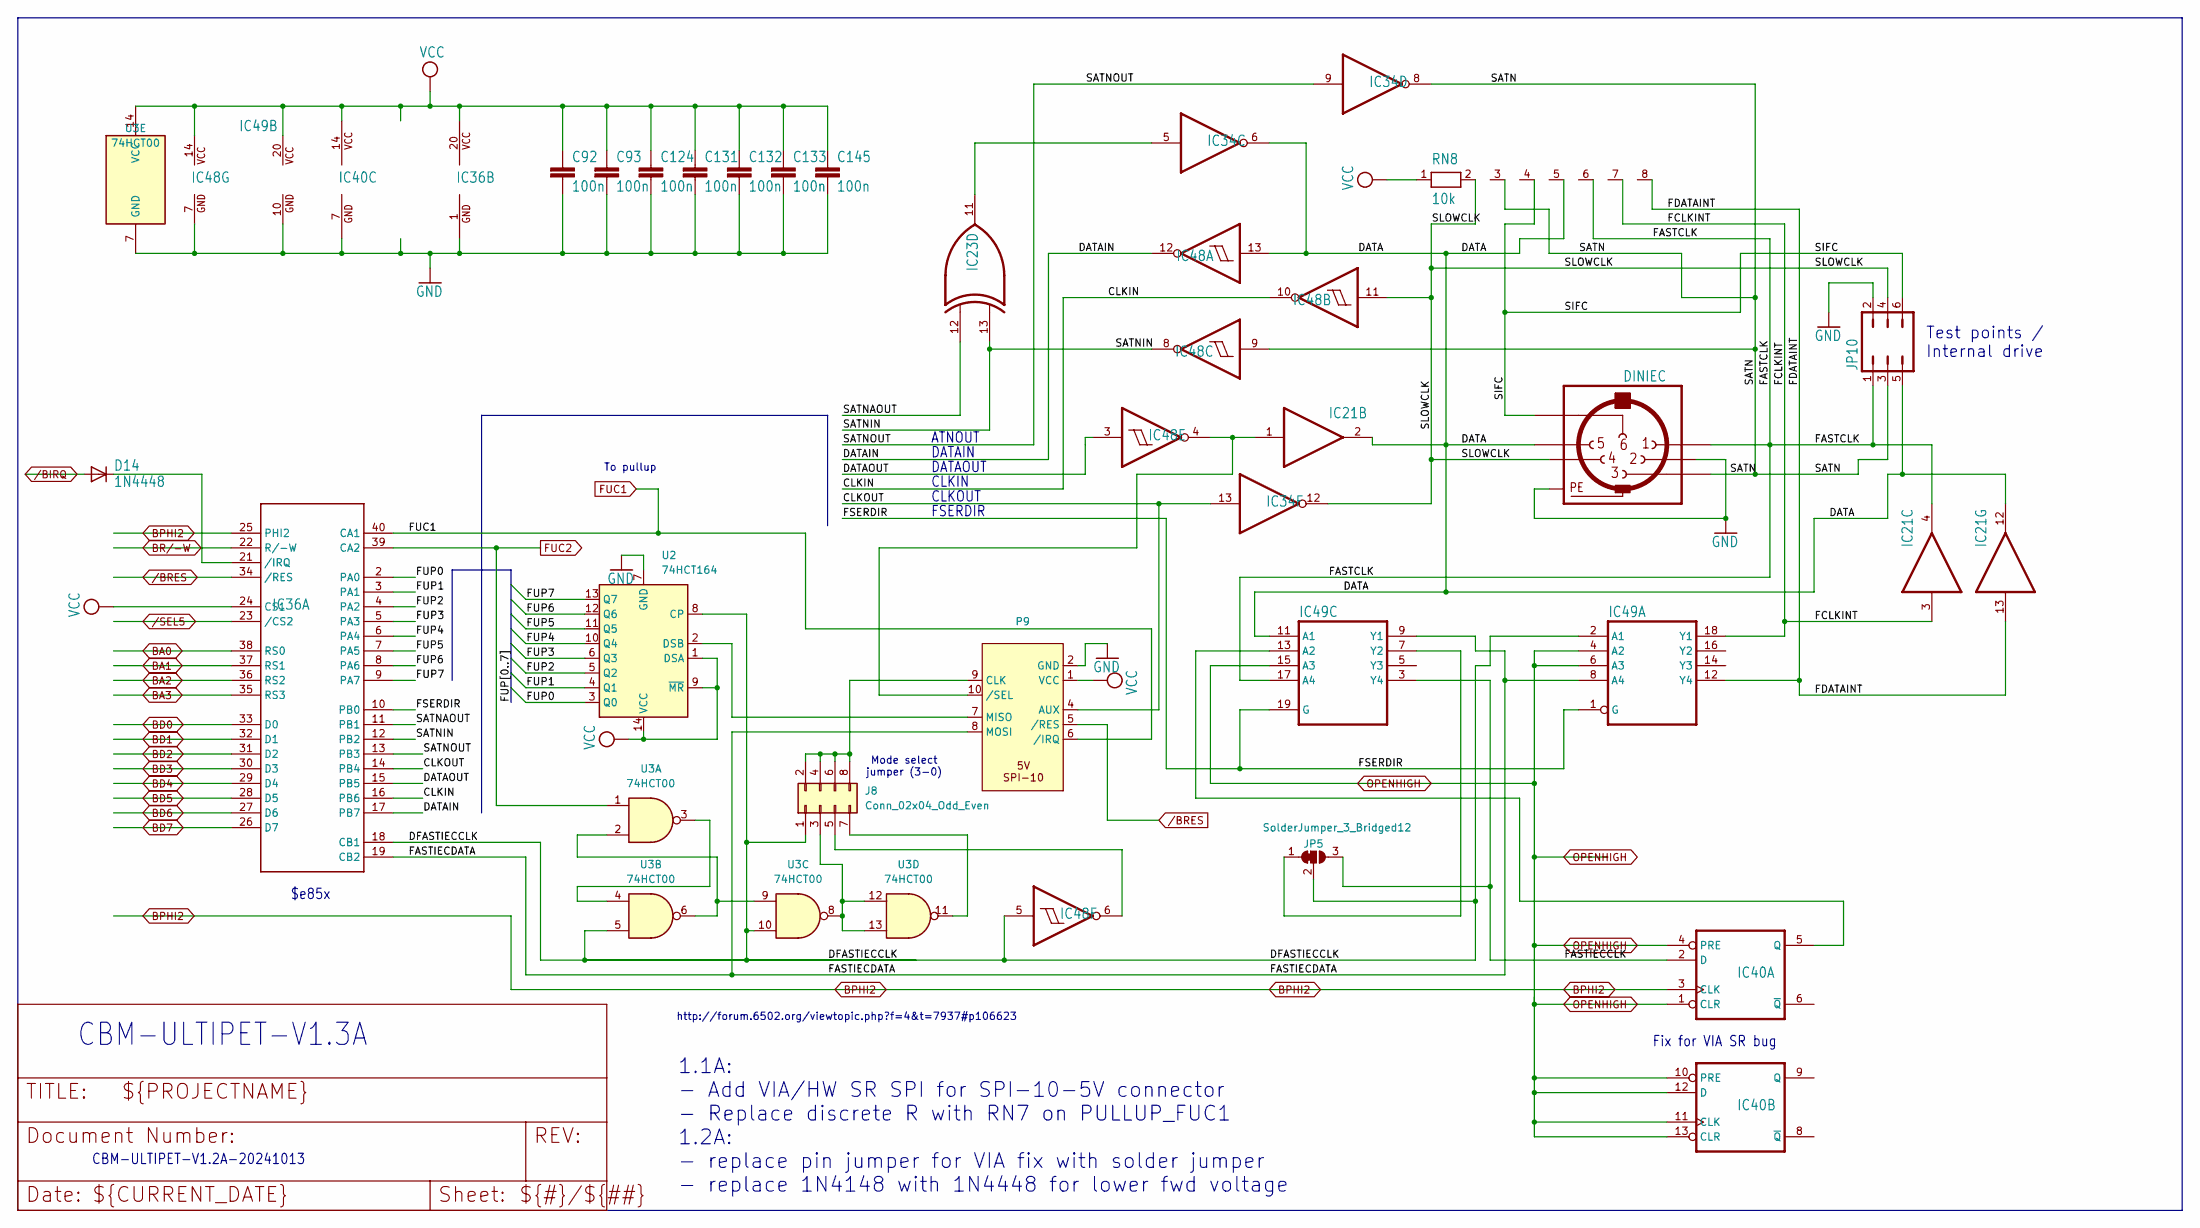
[picture p27: schematic FastIEC.kicad_sch]

Parts:
C92, C93, C124, C131, C132, C133, C145: 100n; C025-024X044
D14: 1N4448; DO35-7
IC21: 7417N; DIP-14_W7.62mm_Socket_LongPads
IC23: 7486N; DIP-14_W7.62mm_Socket_LongPads
IC34: 7406N; DIP-14_W7.62mm_Socket_LongPads
IC36: VIA; DIP-40_W15.24mm_Socket_LongPads
IC40: 7474N; DIP-14_W7.62mm_Socket_LongPads
IC48: 7414N; DIP-14_W7.62mm_Socket_LongPads
IC49: 74241N; DIP-20_W7.62mm_Socket_LongPads
J8: Conn_02x04_Odd_Even; PinHeader_2x04_P2.54mm_Vertical
JP5: SolderJumper_3_Bridged12; SolderJumper-3_P1.3mm_Bridged12_RoundedPad1.0x1.5mm_NumberL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
JP10: JP3Q
P9: IDC-Header_2x05_P2.54mm_Vertical
RN8: 10k; RN-8
U2: 74HCT164; DIP-14_W7.62mm_Socket_LongPads
U3: 74HCT00; DIP-14_W7.62mm_Socket_LongPads
UX28: DINIEC; DIN6PIEC

Connections:
/BIRQ: D14.A
/BRES: IC36.34 (/RES)
/SEL5: IC36.23 (/CS2)
BA0: IC36.38 (RS0)
BA1: IC36.37 (RS1)
BA2: IC36.36 (RS2)
BA3: IC36.35 (RS3)
BD0: IC36.33 (D0)
BD1: IC36.32 (D1)
BD2: IC36.31 (D2)
BD3: IC36.30 (D3)
BD4: IC36.29 (D4)
BD5: IC36.28 (D5)
BD6: IC36.27 (D6)
BD7: IC36.26 (D7)
BPHI2: IC36.25 (PHI2), IC40.3 (CLK)
BR/-W: IC36.22 (R/-W)
CLKIN: IC36.16 (PB6), IC48.10 (O)
CLKOUT: IC34.13 (I), IC36.14 (PB4), P9.4 (AUX)
DATA: IC21.2 (O), IC21.12 (O), IC34.6 (O), IC48.13 (I), IC49.11 (A1), JP10.5, RN8.5, UX28.5
DATAIN: IC36.17 (PB7), IC48.12 (O)
DATAOUT: IC36.15 (PB5), IC48.3 (I)
DFASTIECCLK: IC36.18 (CB1), IC48.5 (I), IC49.2 (A1), J8.1, JP5.2 (C), U2.8 (CP), U3.5, U3.10
FASTCLK: IC21.4 (O), IC49.17 (A4), JP10.1, RN8.6, UX28.1
FASTIECCLK: IC40.2 (D), IC49.3 (Y4), JP5.3 (B)
FASTIECDATA: IC36.19 (CB2), IC49.8 (A4), IC49.9 (Y1), P9.8 (MOSI)
FCLKINT: IC21.3 (I), IC49.18 (Y1), RN8.7
FDATAINT: IC21.13 (I), IC49.12 (Y4), RN8.8
FSERDIR: IC36.10 (PB0), IC49.1 (G), IC49.19 (G)
FUC1: IC36.40 (CA1), P9.6 (/IRQ)
FUC2: IC36.39 (CA2), U3.1
FUP0: IC36.2 (PA0), U2.3 (Q0)
FUP1: IC36.3 (PA1), U2.4 (Q1)
FUP2: IC36.4 (PA2), U2.5 (Q2)
FUP3: IC36.5 (PA3), U2.6 (Q3)
FUP4: IC36.6 (PA4), U2.10 (Q4)
FUP5: IC36.7 (PA5), U2.11 (Q5)
FUP6: IC36.8 (PA6), U2.12 (Q6)
FUP7: IC36.9 (PA7), U2.13 (Q7)
GND: C92.2, C93.2, C124.2, C131.2, C132.2, C133.2, C145.2, IC36.1 (GND), IC40.7 (GND), IC48.7 (GND), IC49.10 (GND), JP10.2, P9.2 (GND), U2.7 (GND), U3.7 (GND), UX28.2, UX28.PE, UX28.PE@ (PE), UX28.PE@1 (PE), UX28.PE@2 (PE)
unnamed: D14.C, IC36.21 (/IRQ)
unnamed: IC21.1 (I), IC48.4 (O), P9.10 (/SEL)
unnamed: IC23.11 (O), IC34.5 (I)
unnamed: IC40.5 (Q), IC49.13 (A2)
unnamed: IC48.6 (O), J8.5
unnamed: IC49.7 (Y2), JP5.1 (A)
unnamed: J8.2, J8.4, J8.6, J8.8, P9.9 (CLK)
unnamed: J8.3, U3.8, U3.12, U3.13
unnamed: J8.7, U3.11
unnamed: P9.7 (MISO), U2.2 (DSB)
unnamed: U3.2, U3.6, U3.9
unnamed: U3.3, U3.4
OPENHIGH: IC40.1 (CLR), IC40.4 (PRE), IC40.10 (PRE), IC40.11 (CLK), IC40.12 (D), IC40.13 (CLR), IC49.4 (A2), IC49.6 (A3), IC49.15 (A3)
SATN: IC34.8 (O), IC48.9 (I), JP10.3, RN8.3, UX28.3
SATNAOUT: IC23.12 (I0), IC36.11 (PB1)
SATNIN: IC23.13 (I1), IC36.12 (PB2), IC48.8 (O)
SATNOUT: IC34.9 (I), IC36.13 (PB3)
SIFC: JP10.6, RN8.4, UX28.6
SLOWCLK: IC34.12 (O), IC48.11 (I), JP10.4, RN8.2, UX28.4
VCC: C92.1, C93.1, C124.1, C131.1, C132.1, C133.1, C145.1, IC36.20 (VCC), IC36.24 (CS1), IC40.14 (VCC), IC48.14 (VCC), IC49.20 (VCC), P9.1 (VCC), RN8.1, U2.1 (DSA), U2.9 (~MR), U2.14 (VCC), U3.14 (VCC)
/BRES: P9.5 (/RES)

Notes on the sheet:
FSERDIR
To pullup
ATNOUT
CBM-ULTIPET-V1.3A
DATAIN
http://forum.6502.org/viewtopic.php?f=4&t=7937#p106623
$e85x
CLKIN
Fix for VIA SR bug
DATAOUT
CLKOUT
CBM-ULTIPET-V1.2A-20241013
Test points / Internal drive
1.1A: - Add VIA/HW SR SPI for SPI-10-5V connector - Replace discrete R with RN7 on PULLUP_FUC1 1.2A: - replace pin jumper for VIA fix with solder jumper - replace 1N4148 with 1N4448 for lower fwd voltage
Mode select jumper (3-0)
