fachat/cbm_ultipet/Board/I2C,UEXT.kicad_sch

## KiCad design Board/I2C,UEXT.kicad_sch (2025-08-31)

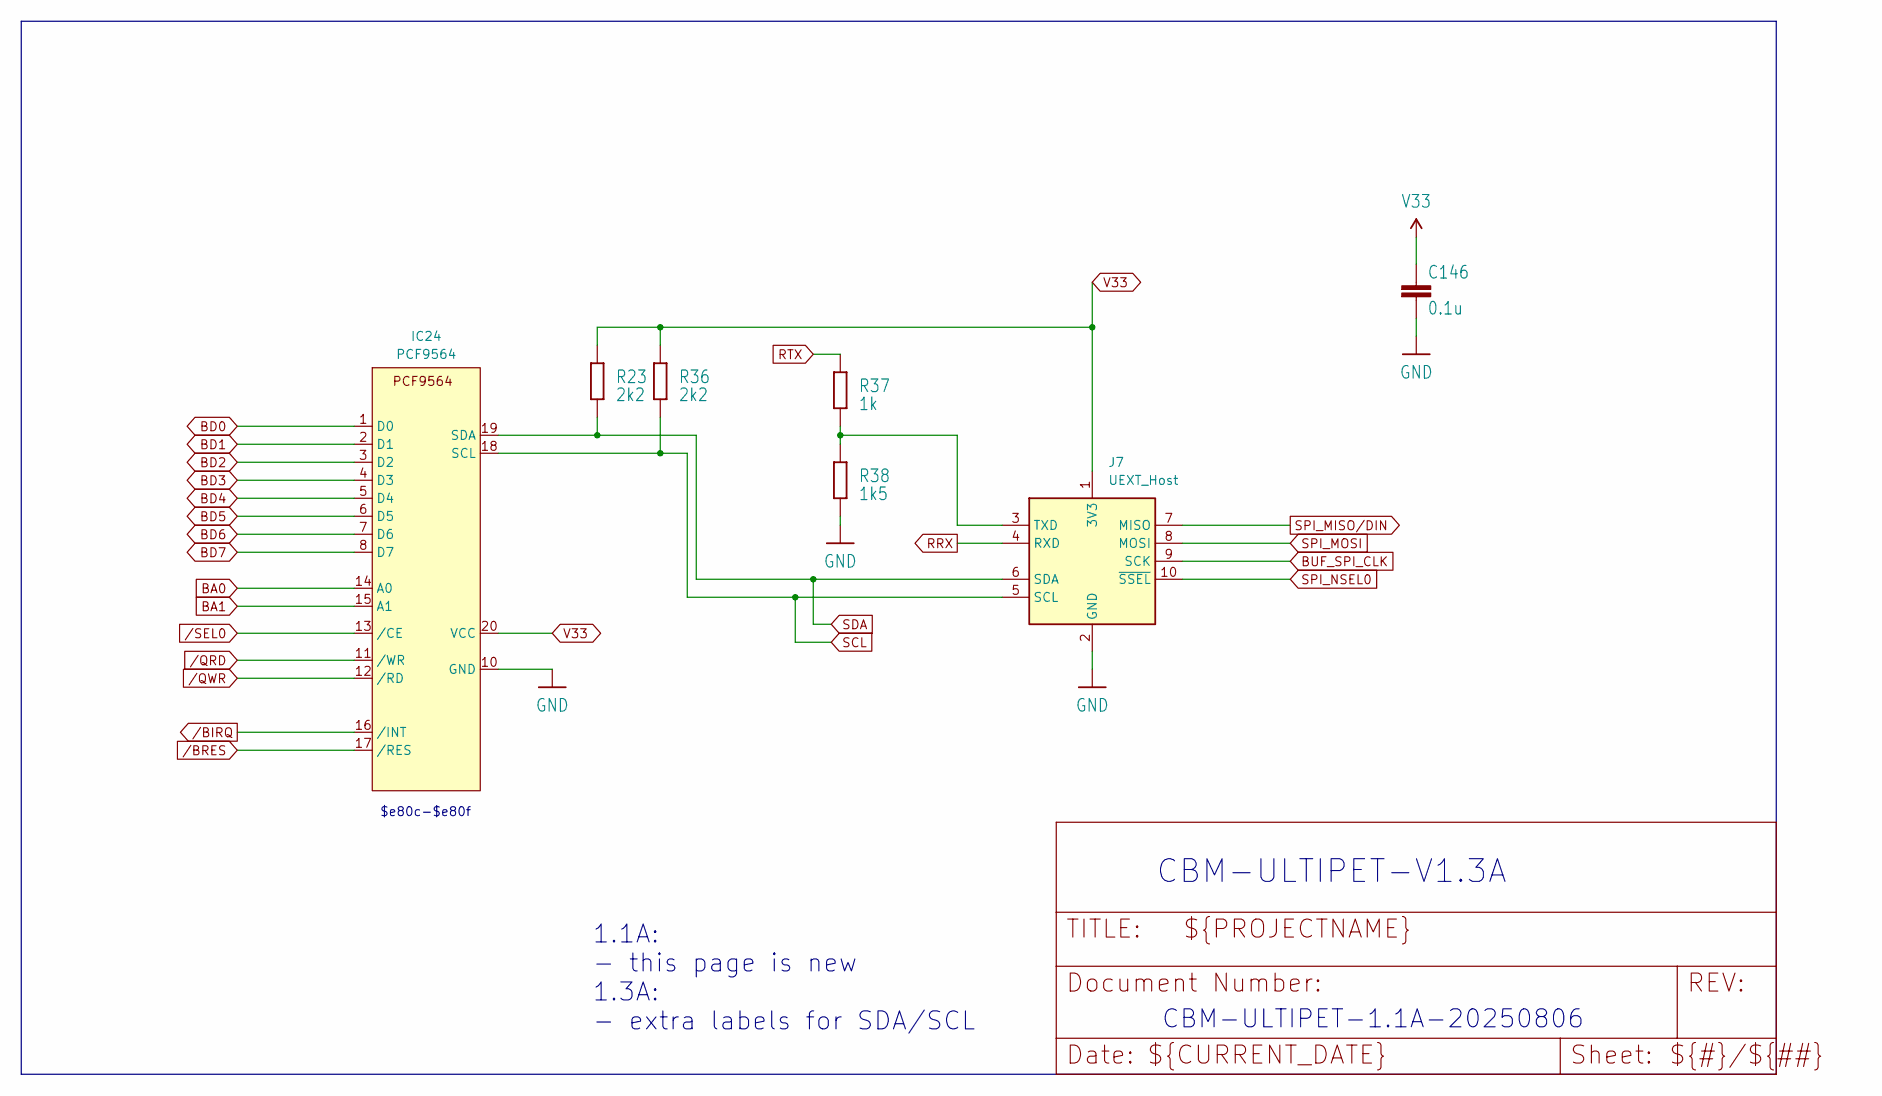
[picture p28: schematic I2C,UEXT.kicad_sch]

Parts:
C146: 0.1u; C0603
IC24: PCF9564; TSSOP-20_4.4x6.5mm_P0.65mm
J7: UEXT_Host; IDC-Header_2x05_P2.54mm_Vertical
R23, R36: 2k2; 0204V
R37: 1k; 0204V
R38: 1k5; 0204V

Connections:
BA0: IC24.14 (A0)
BA1: IC24.15 (A1)
BD0: IC24.1 (D0)
BD1: IC24.2 (D1)
BD2: IC24.3 (D2)
BD3: IC24.4 (D3)
BD4: IC24.5 (D4)
BD5: IC24.6 (D5)
BD6: IC24.7 (D6)
BD7: IC24.8 (D7)
BUF_SPI_CLK: J7.9 (SCK)
GND: C146.2, IC24.10 (GND), J7.2 (GND), R38.2
unnamed: J7.3 (TXD), R37.2, R38.1
RRX: J7.4 (RXD)
RTX: R37.1
SCL: IC24.18 (SCL), J7.5 (SCL), R36.2
SDA: IC24.19 (SDA), J7.6 (SDA), R23.2
SPI_MISO/DIN: J7.7 (MISO)
SPI_MOSI: J7.8 (MOSI)
SPI_NSEL0: J7.10 (~SSEL)
V33: C146.1, IC24.20 (VCC), J7.1 (3V3), R23.1, R36.1
/BIRQ: IC24.16 (/INT)
/BRES: IC24.17 (/RES)
/QRD: IC24.11 (/WR)
/QWR: IC24.12 (/RD)
/SEL0: IC24.13 (/CE)

Notes on the sheet:
$e80c-$e80f
CBM-ULTIPET-V1.3A
CBM-ULTIPET-1.1A-20250806
1.1A: - this page is new 1.3A: - extra labels for SDA/SCL
