fachat/cbm_ultipet/Board/Keylock.kicad_sch

## KiCad design Board/Keylock.kicad_sch (2025-08-31)

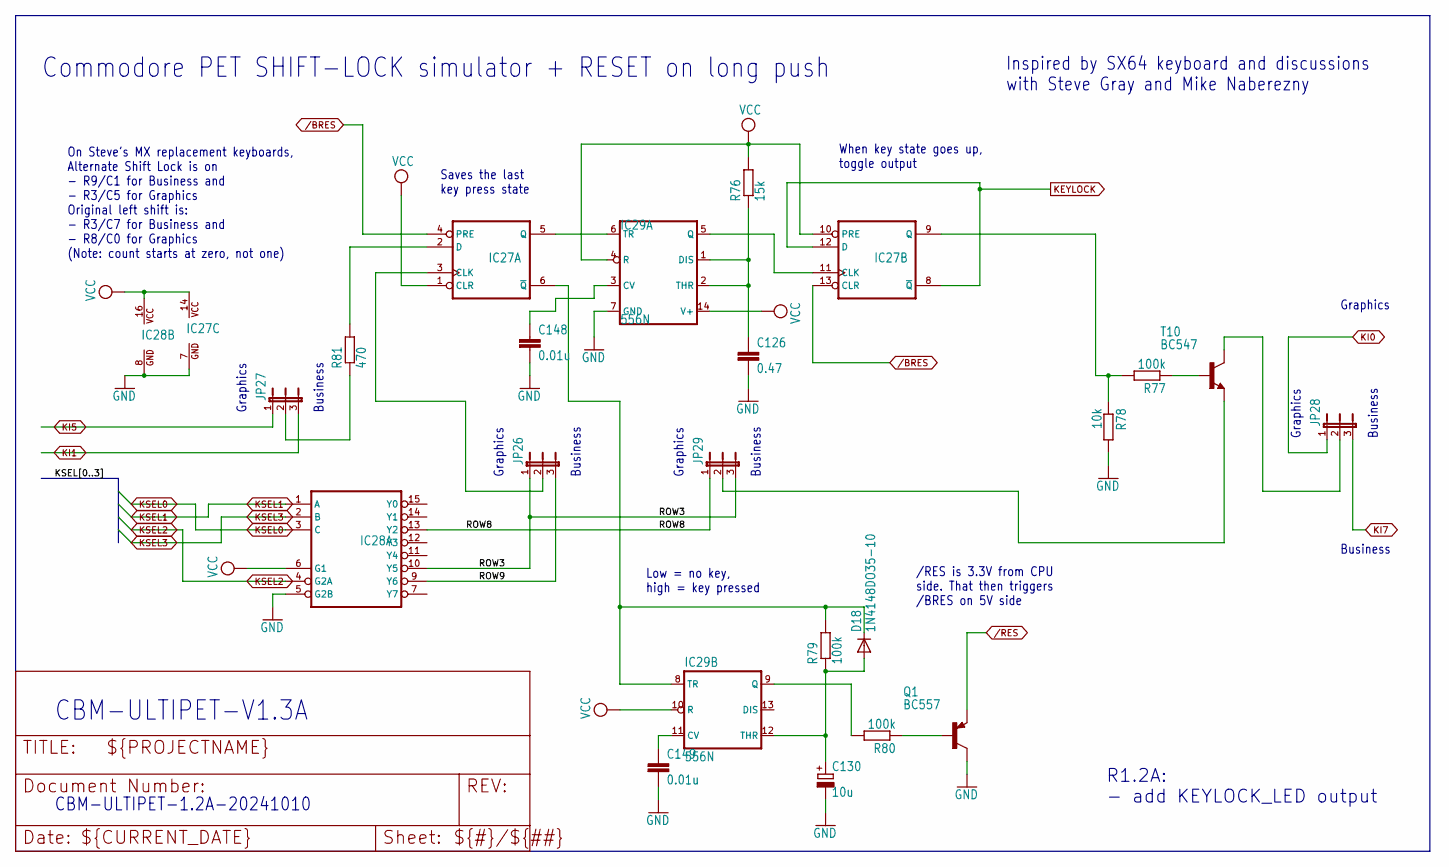
[picture p29: schematic Keylock.kicad_sch]

Parts:
C126: 0.47; C025-025X050
C130: 10u; E2-5
C148, C149: 0.01u; C025-024X044
D18: 1N4148DO35-10; DO35-10
IC27: 7474N; DIP-14_W7.62mm_Socket_LongPads
IC28: 74138N; DIP-16_W7.62mm_Socket_LongPads
IC29: 556N; DIP-14_W7.62mm_Socket_LongPads
JP26, JP27, JP28, JP29: JP2E; JP2
Q1: BC557; TO92
R76: 15k; 0207_7
R77, R79, R80: 100k; 0207_7
R78: 10k; 0207_7
R81: 470; 0207_7
T10: BC547; TO92

Connections:
/BRES: IC27.4 (PRE), IC27.13 (CLR)
/RES: Q1.1 (E)
GND: C126.2, C130.-, C148.2, C149.2, IC27.7 (GND), IC28.5 (G2B), IC28.8 (GND), IC29.7 (GND), Q1.3 (C), R78.2
KEYLOCK: IC27.8 (~Q), IC27.12 (D)
KI0: JP28.1
KI1: JP27.3
KI5: JP27.1
KI7: JP28.3
KSEL0: IC28.3 (C)
KSEL1: IC28.1 (A)
KSEL2: IC28.4 (G2A)
KSEL3: IC28.2 (B)
unnamed: C126.1, IC29.1 (DIS), IC29.2 (THR), R76.1
unnamed: C130.+, D18.A, IC29.12 (THR), R79.1
unnamed: C148.1, IC29.3 (CV)
unnamed: C149.1, IC29.11 (CV)
unnamed: D18.C, IC27.6 (~Q), IC29.8 (TR), R79.2
unnamed: IC27.2 (D), R81.2
unnamed: IC27.3 (CLK), JP26.2
unnamed: IC27.5 (Q), IC29.6 (TR)
unnamed: IC27.9 (Q), R77.2, R78.1
unnamed: IC27.11 (CLK), IC29.5 (Q)
unnamed: IC29.9 (Q), R80.2
unnamed: JP27.2, R81.1
unnamed: JP28.2, T10.3 (C)
unnamed: JP29.2, T10.1 (E)
unnamed: Q1.2 (B), R80.1
unnamed: R77.1, T10.2 (B)
ROW3: IC28.10 (Y5), JP26.1, JP29.3
ROW8: IC28.13 (Y2), JP29.1
ROW9: IC28.9 (Y6), JP26.3
VCC: IC27.1 (CLR), IC27.10 (PRE), IC27.14 (VCC), IC28.6 (G1), IC28.16 (VCC), IC29.4 (R), IC29.10 (R), IC29.14 (V+), R76.2

Notes on the sheet:
Commodore PET SHIFT-LOCK simulator + RESET on long push
CBM-ULTIPET-V1.3A
Business
Low = no key, high = key pressed
Graphics
/RES is 3.3V from CPU side. That then triggers /BRES on 5V side
CBM-ULTIPET-1.2A-20241010
Saves the last key press state
When key state goes up, toggle output
Inspired by SX64 keyboard and discussions with Steve Gray and Mike Naberezny
R1.2A: - add KEYLOCK_LED output
On Steve's MX replacement keyboards, Alternate Shift Lock is on - R9/C1 for Business and - R3/C5 for Graphics Original left shift is: - R3/C7 for Business and - R8/C0 for Graphics (Note: count starts at zero, not one)
