fachat/cbm_ultipet/Board/Mixer.kicad_sch

## KiCad design Board/Mixer.kicad_sch (2025-08-31)

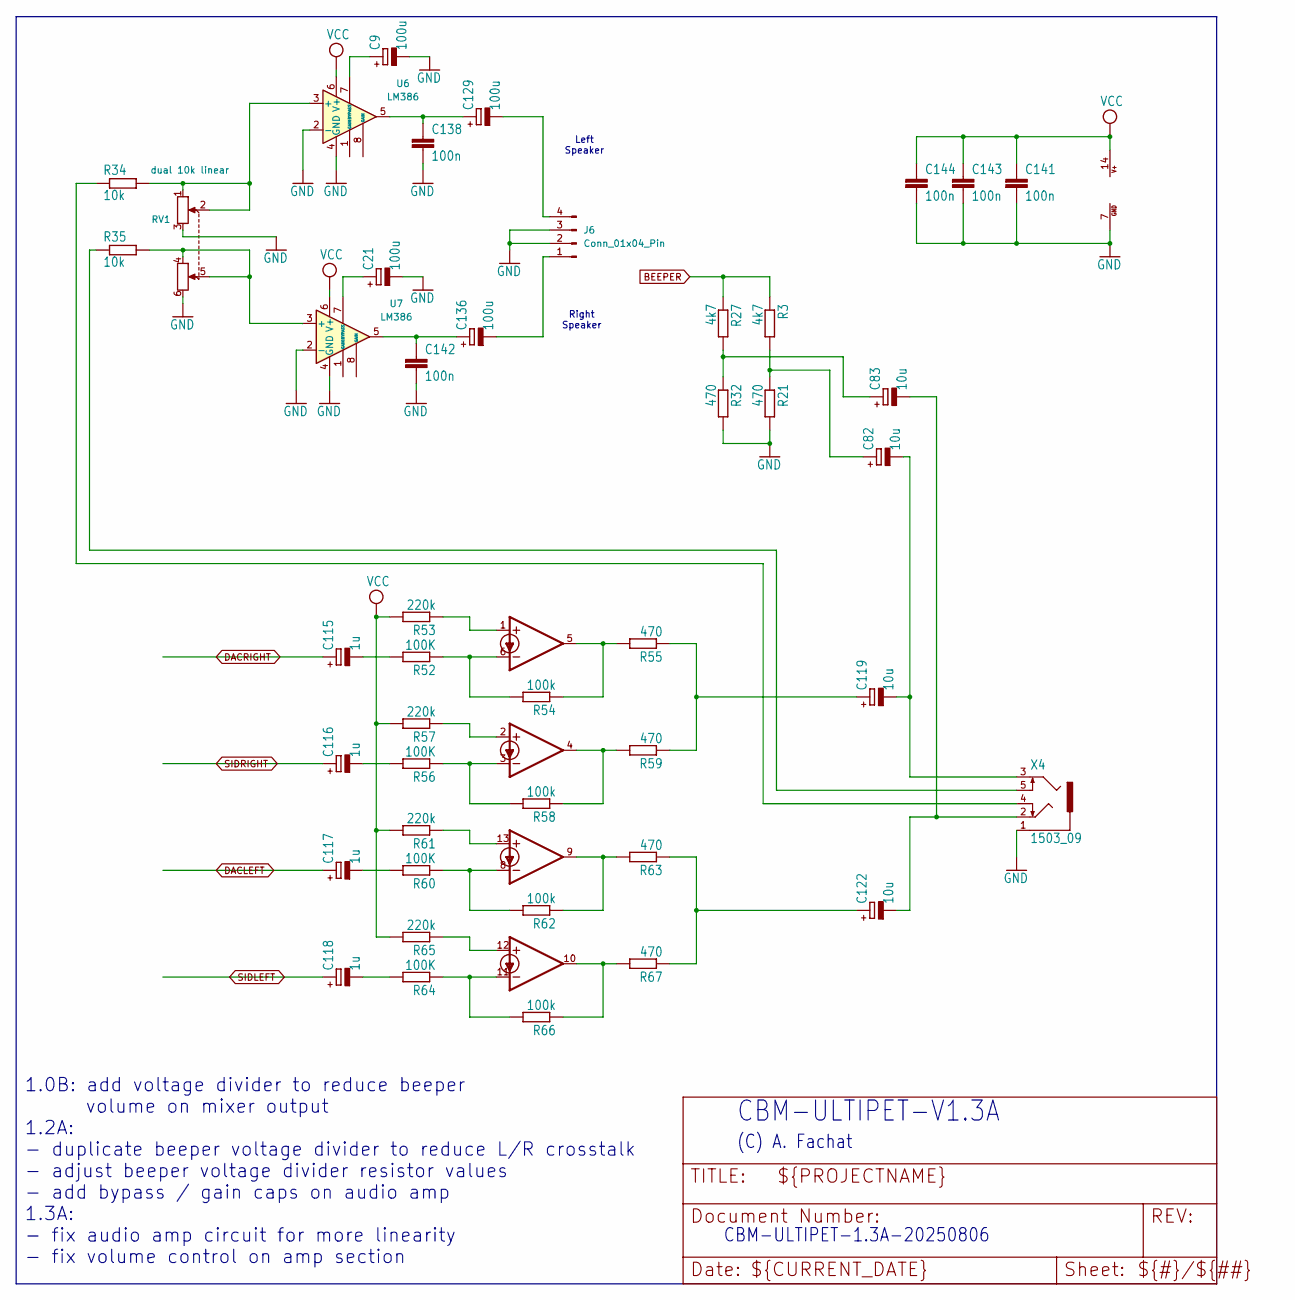
[picture p30: schematic Mixer.kicad_sch]

Parts:
C9, C21, C129, C136: 100u; E2-5
C82, C83, C119, C122: 10u; E2-5
C115, C116, C117, C118: 1u; E2-5
C138, C141, C142, C143, C144: 100n; C025-024X044
IC26: LM3900N; DIP-14_W7.62mm_Socket_LongPads
J6: Conn_01x04_Pin; PinHeader_1x04_P2.54mm_Vertical
R3, R27: 4k7; 0204_7
R21, R32, R55, R59, R63, R67: 470; 0204_7
R34, R35: 10k; R_Axial_DIN0204_L3.6mm_D1.6mm_P2.54mm_Vertical
R52, R56, R60, R64: 100K; 0204_7
R53, R57, R61, R65: 220k; 0204_7
R54, R58, R62, R66: 100k; 0204_7
RV1: dual 10k linear; RK12L12_horizontal
U6, U7: LM386; DIP-8_W7.62mm_Socket_LongPads
X4: 1503_09

Connections:
BEEPER: R3.1, R27.1
DACLEFT: C117.+
DACRIGHT: C115.+
GND: C9.-, C21.-, C138.2, C141.2, C142.2, C143.2, C144.2, IC26.7 (GND), J6.2, J6.3, R21.2, R32.2, RV1.3, RV1.6, U6.2 (-), U6.4 (GND), U7.2 (-), U7.4 (GND), X4.1
unnamed: C9.+, U6.7 (BYPASS)
unnamed: C21.+, U7.7 (BYPASS)
unnamed: C82.+, R3.2, R21.1
unnamed: C83.+, R27.2, R32.1
unnamed: C115.-, R52.2
unnamed: C116.-, R56.2
unnamed: C117.-, R60.2
unnamed: C118.-, R64.2
unnamed: C119.+, R55.1, R59.1
unnamed: C82.-, C119.-, X4.3
unnamed: C122.+, R63.1, R67.1
unnamed: C83.-, C122.-, X4.2
unnamed: C129.+, C138.1, U6.5
unnamed: C129.-, J6.4
unnamed: C136.+, C142.1, U7.5
unnamed: C136.-, J6.1
unnamed: IC26.1 (+IN), R53.1
unnamed: IC26.2 (+IN), R57.1
unnamed: IC26.3 (-IN), R56.1, R58.2
unnamed: IC26.4 (OUT), R58.1, R59.2
unnamed: IC26.5 (OUT), R54.1, R55.2
unnamed: IC26.6 (-IN), R52.1, R54.2
unnamed: IC26.8 (-IN), R60.1, R62.2
unnamed: IC26.9 (OUT), R62.1, R63.2
unnamed: IC26.10 (OUT), R66.1, R67.2
unnamed: IC26.11 (-IN), R64.1, R66.2
unnamed: IC26.12 (+IN), R65.1
unnamed: IC26.13 (+IN), R61.1
unnamed: R34.1, X4.4
unnamed: R34.2, RV1.1, RV1.2, U6.3 (+)
unnamed: R35.1, X4.5
unnamed: R35.2, RV1.4, RV1.5, U7.3 (+)
SIDLEFT: C118.+
SIDRIGHT: C116.+
VCC: C141.1, C143.1, C144.1, IC26.14 (V+), R53.2, R57.2, R61.2, R65.2, U6.6 (V+), U7.6 (V+)

Notes on the sheet:
Right Speaker
CBM-ULTIPET-V1.3A
(C) A. Fachat
CBM-ULTIPET-1.3A-20250806
Left Speaker
1.0B: add voltage divider to reduce beeper volume on mixer output 1.2A: - duplicate beeper voltage divider to reduce L/R crosstalk - adjust beeper voltage divider resistor values - add bypass / gain caps on audio amp 1.3A: - fix audio amp circuit for more linearity - fix volume control on amp secti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
