fachat/cbm_ultipet/Board/PETIO.kicad_sch

## KiCad design Board/PETIO.kicad_sch (2026-05-08)

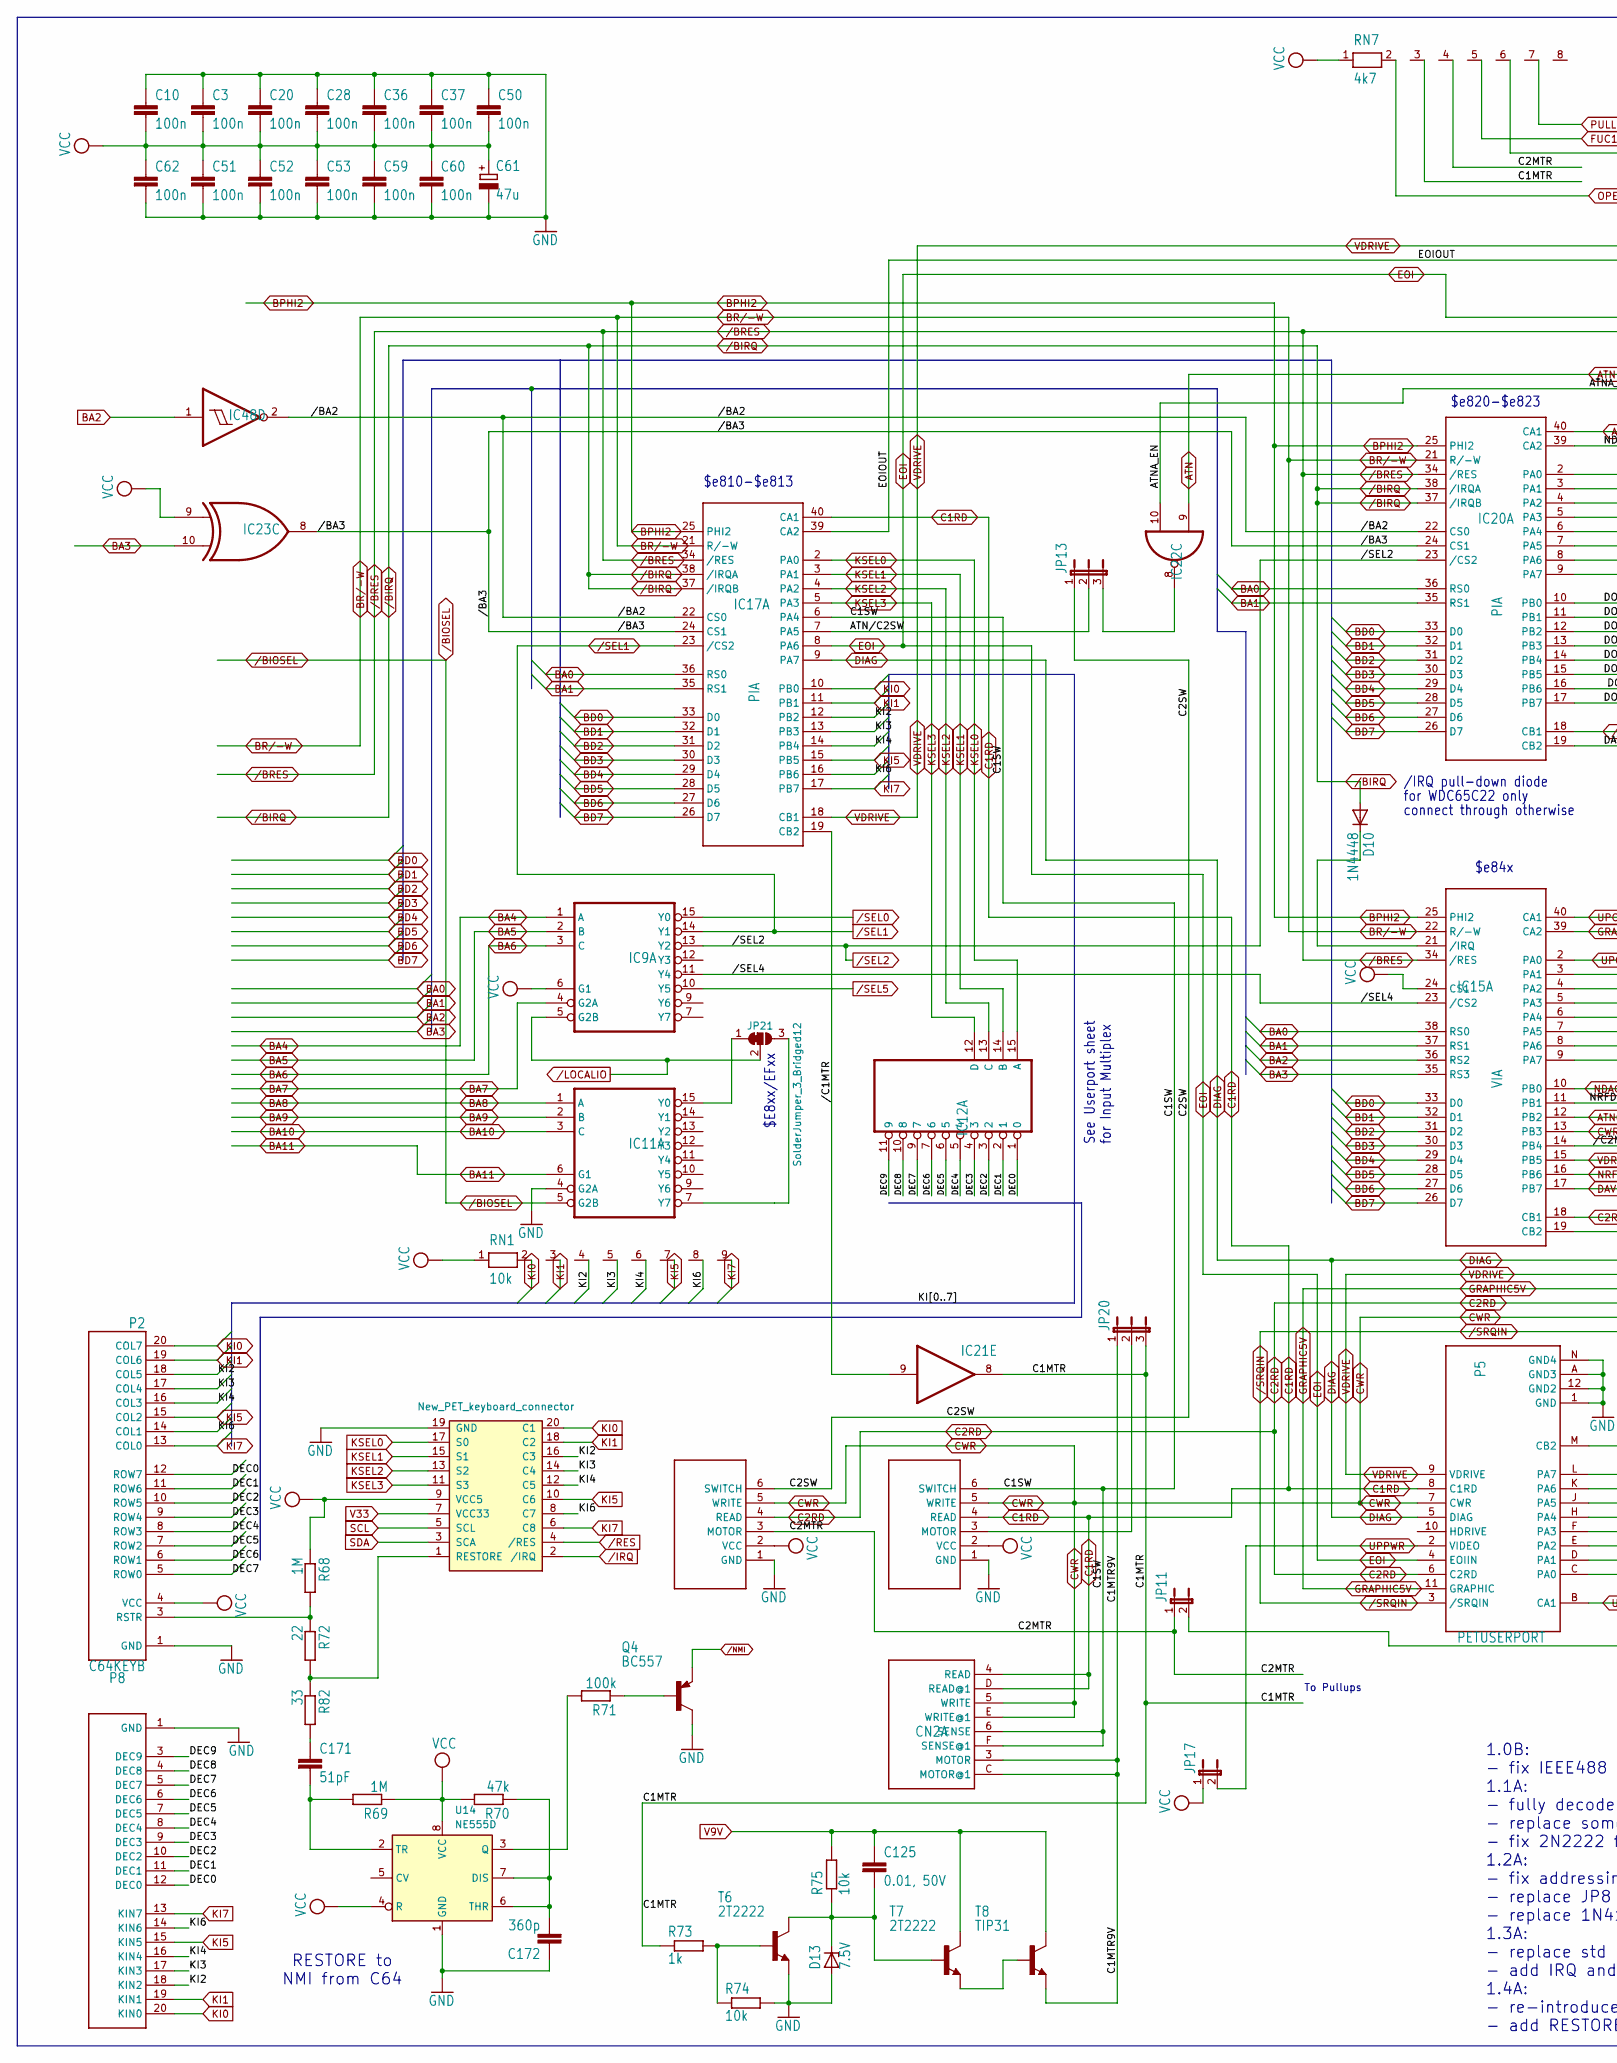
[picture p31: schematic PETIO.kicad_sch, part in row 1, column 1]

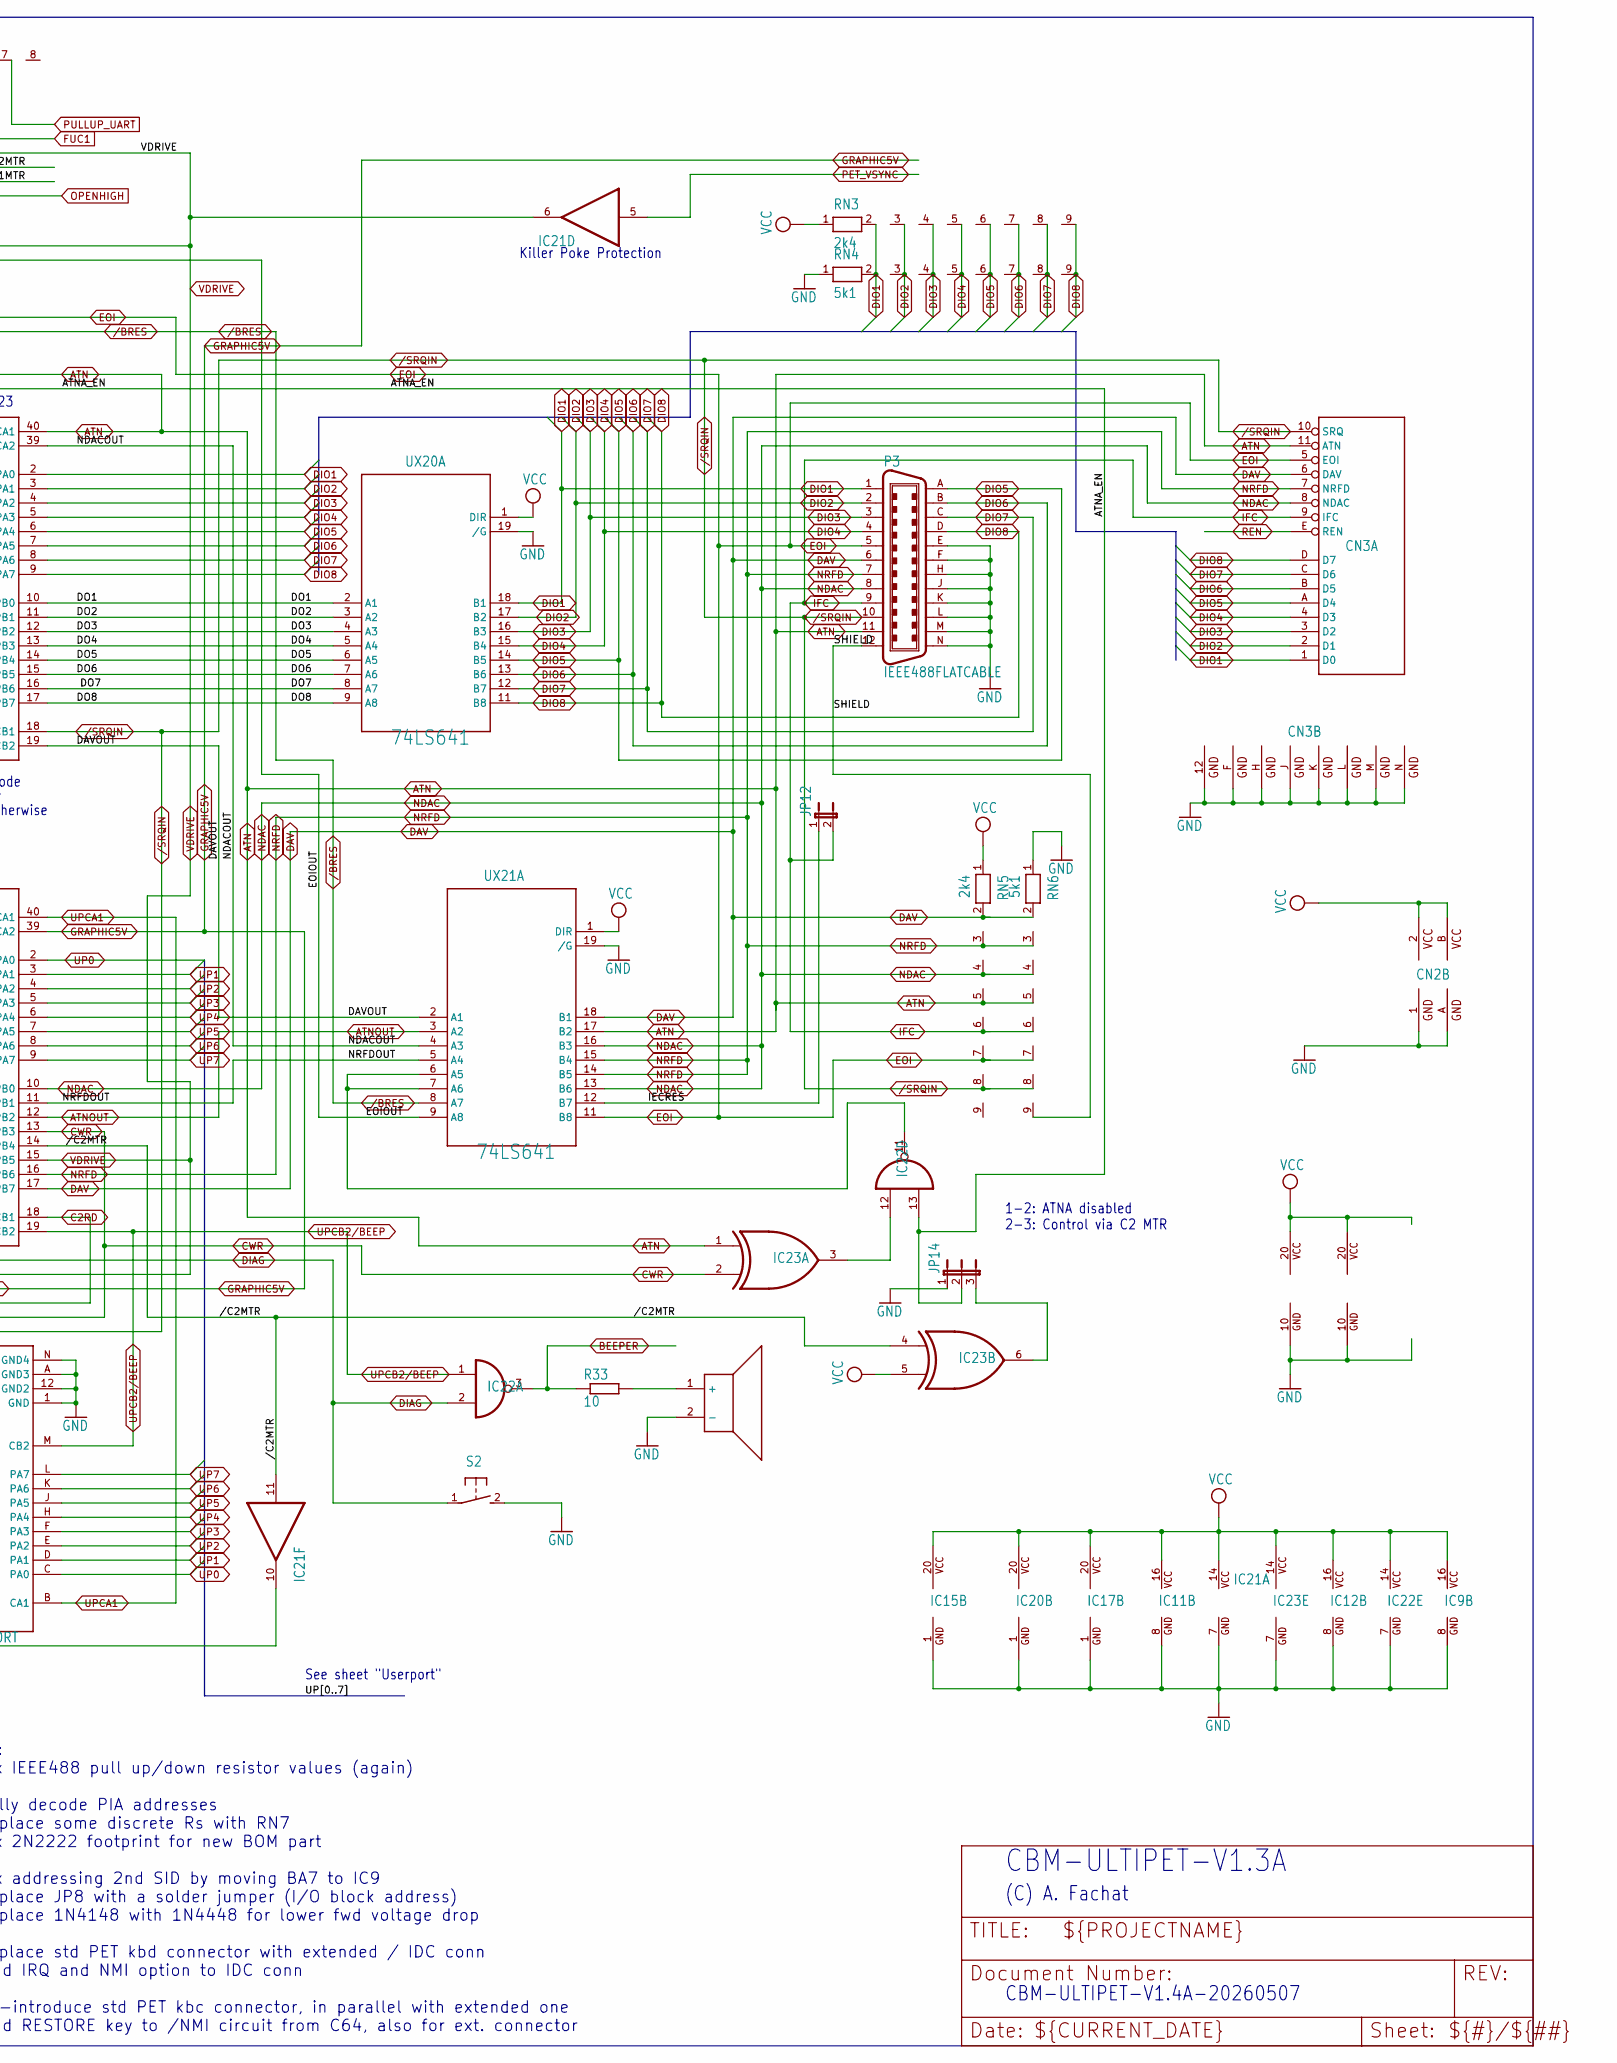
[picture p32: schematic PETIO.kicad_sch, part in row 1, column 2]

Parts:
BEEP1: PIEZOBEEPERPIEZO; PIEZOBEEPER
C3, C10, C20, C28, C36, C37, C50, C51, C52, C53, C59, C60, C62: 100n; C025-025X050
C61: 47u; E2,5-6
C125: 0.01, 50V; C025-024X044
C171: 51pF; C025-024X044
C172: 360p; C025-024X044
CN2: PORT_CASSETTE_EDGE; MA156_6-2_KEYED
CN3: PORT_IEEE_EDGE; MA156_12-2_IEEE
D10: 1N4448; D-5
D13: 7.5V; C1702-15
IC9, IC11: 74138N; DIP-16_W7.62mm_Socket_LongPads
IC12: 74145N; DIP-16_W7.62mm_Socket_LongPads
IC15: VIA; DIP-40_W15.24mm_Socket_LongPads
IC17, IC20: PIA; DIP-40_W15.24mm_Socket_LongPads
IC21: 7417N; DIP-14_W7.62mm_Socket_LongPads
IC22: 7400N; DIP-14_W7.62mm_Socket_LongPads
IC23: 7486N; DIP-14_W7.62mm_Socket_LongPads
IC48: 7414N; DIP-14_W7.62mm_Socket_LongPads
J2: New_PET_keyboard_connector; IDC-Header_2x10_P2.54mm_Vertical
JP11, JP12, JP17: JP1E; JP1
JP13, JP14, JP20: JP2E; JP2
JP21: SolderJumper_3_Bridged12; SolderJumper-3_P1.3mm_Bridged12_RoundedPad1.0x1.5mm_NumberL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
P2: C64KEYB
P3: IEEE488FLATCABLE; FLAT24
P5: PETUSERPORT; FLAT24
P6, P7: CBMTAPE; JP6
P8: C64KEYB
Q4: BC557; TO92
R33: 10; 0207_10
R68, R69: 1M; 0207_2V
R70: 47k; 0207_2V
R71: 100k; 0207_7
R72: 22; 0207_2V
R73: 1k; 0207_10
R74, R75: 10k; 0207_10
R82: 33; 0207_2V
RN1: 10k; RN-9
RN3, RN5: 2k4; RN-9
RN4, RN6: 5k1; RN-9
RN7: 4k7; RN-8
S2: 31-XX; B3F-31XX
T6, T7: 2T2222; TO92
T8: TIP31; TO220
U14: NE555D; SOIC-8_3.9x4.9mm_P1.27mm
UX20, UX21: 74LS641; DIP-20_W7.62mm_Socket_LongPads

Connections:
/BA3: IC17.24 (CS1), IC20.24 (CS1), IC23.8 (O)
/BIOSEL: IC11.5 (G2B)
/BIRQ: D10.A, IC17.37 (/IRQB), IC17.38 (/IRQA), IC20.37 (/IRQB), IC20.38 (/IRQA)
/BRES: IC15.34 (/RES), IC17.34 (/RES), IC20.34 (/RES), UX21.8 (A7)
/C1MTR: IC17.19 (CB2), IC21.9 (I)
/C2MTR: IC15.14 (PB4), IC21.11 (I), IC23.4 (I0)
/NMI: Q4.1 (E)
/SEL1: IC9.14 (Y1), IC17.23 (/CS2)
/SEL4: IC9.11 (Y4), IC15.23 (/CS2)
/SRQIN: CN3.10 (SRQ), IC20.18 (CB1), P3.10, P5.3 (/SRQIN), RN5.8, RN6.8
ATN: CN3.11 (ATN), IC20.40 (CA1), IC22.9 (I0), IC23.1 (I0), P3.11, RN5.5, RN6.5, UX21.17 (B2)
ATN/C2SW: IC17.7 (PA5), JP13.2
ATNA_EN: IC22.10 (I1), IC22.13 (I1), JP14.2
ATNOUT: IC15.12 (PB2), UX21.3 (A2)
BA0: IC15.38 (RS0), IC17.36 (RS0), IC20.36 (RS0)
BA1: IC15.37 (RS1), IC17.35 (RS1), IC20.35 (RS1)
BA2: IC15.36 (RS2), IC48.1 (I)
BA3: IC15.35 (RS3), IC23.10 (I1)
BA4: IC9.1 (A)
BA5: IC9.2 (B)
BA6: IC9.3 (C)
BA7: IC9.4 (G2A)
BA8: IC11.1 (A)
BA9: IC11.2 (B)
BA10: IC11.3 (C)
BA11: IC11.6 (G1)
BD0: IC15.33 (D0), IC17.33 (D0), IC20.33 (D0)
BD1: IC15.32 (D1), IC17.32 (D1), IC20.32 (D1)
BD2: IC15.31 (D2), IC17.31 (D2), IC20.31 (D2)
BD3: IC15.30 (D3), IC17.30 (D3), IC20.30 (D3)
BD4: IC15.29 (D4), IC17.29 (D4), IC20.29 (D4)
BD5: IC15.28 (D5), IC17.28 (D5), IC20.28 (D5)
BD6: IC15.27 (D6), IC17.27 (D6), IC20.27 (D6)
BD7: IC15.26 (D7), IC17.26 (D7), IC20.26 (D7)
BEEPER: IC22.3 (O), R33.1
BPHI2: IC15.25 (PHI2), IC17.25 (PHI2), IC20.25 (PHI2)
BR/-W: IC15.22 (R/-W), IC17.21 (R/-W), IC20.21 (R/-W)
C1MTR: IC21.8 (O), JP20.3, R73.1, RN7.3
C1MTR9V: CN2.3 (MOTOR), CN2.C (MOTOR@1), JP20.1, T8.3 (E)
C1RD: CN2.4 (READ), CN2.D (READ@1), IC17.40 (CA1), P5.8 (C1RD), P6.4 (READ)
C1SW: CN2.6 (SENSE), CN2.F (SENSE@1), IC17.6 (PA4), P6.6 (SWITCH)
C2MTR: JP11.1, P7.3 (MOTOR), RN7.4
C2RD: IC15.18 (CB1), P5.6 (C2RD), P7.4 (READ)
C2SW: JP13.1, P7.6 (SWITCH)
CWR: CN2.5 (WRITE), CN2.E (WRITE@1), IC15.13 (PB3), IC23.2 (I1), P5.7 (CWR), P6.5 (WRITE), P7.5 (WRITE)
DAV: CN3.6 (DAV), IC15.17 (PB7), P3.6, RN5.2, RN6.2, UX21.18 (B1)
DAVOUT: IC20.19 (CB2), UX21.2 (A1)
DEC0: IC12.1 (0), P2.12 (ROW7), P8.12 (DEC0)
DEC1: IC12.2 (1), P2.11 (ROW6), P8.11 (DEC1)
DEC2: IC12.3 (2), P2.10 (ROW5), P8.10 (DEC2)
DEC3: IC12.4 (3), P2.9 (ROW4), P8.9 (DEC3)
DEC4: IC12.5 (4), P2.8 (ROW3), P8.8 (DEC4)
DEC5: IC12.6 (5), P2.7 (ROW2), P8.7 (DEC5)
DEC6: IC12.7 (6), P2.6 (ROW1), P8.6 (DEC6)
DEC7: IC12.9 (7), P2.5 (ROW0), P8.5 (DEC7)
DEC8: IC12.10 (8), P8.4 (DEC8)
DEC9: IC12.11 (9), P8.3 (DEC9)
DIAG: IC17.9 (PA7), IC22.2 (I1), P5.5 (DIAG), S2.1
DIO1: CN3.1 (D0), IC20.2 (PA0), P3.1, RN3.2, RN4.2, UX20.18 (B1)
DIO2: CN3.2 (D1), IC20.3 (PA1), P3.2, RN3.3, RN4.3, UX20.17 (B2)
DIO3: CN3.3 (D2), IC20.4 (PA2), P3.3, RN3.4, RN4.4, UX20.16 (B3)
DIO4: CN3.4 (D3), IC20.5 (PA3), P3.4, RN3.5, RN4.5, UX20.15 (B4)
DIO5: CN3.A (D4), IC20.6 (PA4), P3.A (13), RN3.6, RN4.6, UX20.14 (B5)
DIO6: CN3.B (D5), IC20.7 (PA5), P3.B (14), RN3.7, RN4.7, UX20.13 (B6)
DIO7: CN3.C (D6), IC20.8 (PA6), P3.C (15), RN3.8, RN4.8, UX20.12 (B7)
DIO8: CN3.D (D7), IC20.9 (PA7), P3.D (16), RN3.9, RN4.9, UX20.11 (B8)
DO1: IC20.10 (PB0), UX20.2 (A1)
DO2: IC20.11 (PB1), UX20.3 (A2)
DO3: IC20.12 (PB2), UX20.4 (A3)
DO4: IC20.13 (PB3), UX20.5 (A4)
DO5: IC20.14 (PB4), UX20.6 (A5)
DO6: IC20.15 (PB5), UX20.7 (A6)
DO7: IC20.16 (PB6), UX20.8 (A7)
DO8: IC20.17 (PB7), UX20.9 (A8)
EOI: CN3.5 (EOI), IC17.8 (PA6), P3.5, P5.4 (EOIIN), RN5.7, RN6.7, UX21.11 (B8)
EOIOUT: IC17.39 (CA2), UX21.9 (A8)
FUC1: RN7.5
GND: BEEP1.2 (-), C3.1, C10.1, C20.1, C28.1, C36.1, C37.1, C50.1, C51.2, C52.2, C53.2, C59.2, C60.2, C61.-, C62.2, C172.1, CN2.1 (GND), CN2.A (GND@1), CN3.12 (GND), CN3.F (GND@1), CN3.H (GND@2), CN3.J (GND@3), CN3.K (GND@4), CN3.L (GND@5), CN3.M (GND@6), CN3.N (GND@7), D13.A, IC9.8 (GND), IC11.4 (G2A), IC11.8 (GND), IC12.8 (GND), IC15.1 (GND), IC17.1 (GND), IC20.1 (GND), IC21.7 (GND), IC22.7 (GND), IC23.7 (GND), J2.19 (GND), JP14.1, P2.1 (GND), P3.E (17), P3.F (18), P3.H (19), P3.J (20), P3.K (21), P3.L (22), P3.M (23), P3.N (24), P5.1 (GND), P5.12 (GND2), P5.A (GND3), P5.N (GND4), P6.1 (GND), P7.1 (GND), P8.1 (GND), Q4.3 (C), R74.2, RN4.1, RN6.1, S2.2 (S), T6.1 (E), U14.1 (GND), UX20.10 (GND), UX20.19 (/G), UX21.10 (GND), UX21.19 (/G)
GRAPHIC5V: IC15.39 (CA2), P5.11 (GRAPHIC)
IECRES: JP12.1, UX21.12 (B7)
IFC: CN3.9 (IFC), JP12.2, P3.9, RN5.6, RN6.6
KI0: IC17.10 (PB0), J2.20 (C1), P2.20 (COL7), P8.20 (KIN0), RN1.2
KI1: IC17.11 (PB1), J2.18 (C2), P2.19 (COL6), P8.19 (KIN1), RN1.3
KI2: IC17.12 (PB2), J2.16 (C3), P2.18 (COL5), P8.18 (KIN2), RN1.4
KI3: IC17.13 (PB3), J2.14 (C4), P2.17 (COL4), P8.17 (KIN3), RN1.5
KI4: IC17.14 (PB4), J2.12 (C5), P2.16 (COL3), P8.16 (KIN4), RN1.6
KI5: IC17.15 (PB5), J2.10 (C6), P2.15 (COL2), P8.15 (KIN5), RN1.7
KI6: IC17.16 (PB6), J2.8 (C7), P2.14 (COL1), P8.14 (KIN6), RN1.8
KI7: IC17.17 (PB7), J2.6 (C8), P2.13 (COL0), P8.13 (KIN7), RN1.9
KSEL0: IC12.15 (A), IC17.2 (PA0), J2.17 (S0)
KSEL1: IC12.14 (B), IC17.3 (PA1), J2.15 (S1)
KSEL2: IC12.13 (C), IC17.4 (PA2), J2.13 (S2)
KSEL3: IC12.12 (D), IC17.5 (PA3), J2.11 (S3)
NDAC: CN3.8 (NDAC), IC15.10 (PB0), P3.8, RN5.4, RN6.4, UX21.13 (B6), UX21.16 (B3)
NDACOUT: IC20.39 (CA2), UX21.4 (A3)
NRFD: CN3.7 (NRFD), IC15.16 (PB6), P3.7, RN5.3, RN6.3, UX21.14 (B5), UX21.15 (B4)
NRFDOUT: IC15.11 (PB1), UX21.5 (A4)
unnamed: BEEP1.1 (+), R33.2
unnamed: C125.2, D13.C, R75.1, T6.3 (C), T7.2 (B)
unnamed: C171.1, R82.2
unnamed: C171.2, R69.2, U14.2 (TR)
unnamed: C172.2, R70.1, U14.6 (THR), U14.7 (DIS)
unnamed: D10.C, IC15.21 (/IRQ)
unnamed: IC11.7 (Y7), JP21.3 (B)
unnamed: IC11.15 (Y0), JP21.1 (A)
unnamed: IC21.10 (O), JP11.2
unnamed: IC22.8 (O), JP13.3
unnamed: IC22.11 (O), UX21.6 (A5), UX21.7 (A6)
unnamed: IC22.12 (I0), IC23.3 (O)
unnamed: IC23.6 (O), JP14.3
unnamed: J2.1 (RESTORE), R72.2, R82.1
unnamed: JP20.2, P6.3 (MOTOR)
unnamed: P2.3 (RSTR), R68.2, R72.1
unnamed: Q4.2 (B), R71.1
unnamed: R71.2, U14.3 (Q)
unnamed: R73.2, R74.1, T6.2 (B)
unnamed: T7.1 (E), T8.1 (B)
OPENHIGH: RN7.2
PET_VSYNC: IC21.5 (I)
PULLUP_UART: RN7.7
REN: CN3.E (REN)
SCL: J2.5 (SCL)
SDA: J2.3 (SCA)
SHIELD: P3.12, RN6.9
UP0: IC15.2 (PA0), P5.C (PA0)
UP1: IC15.3 (PA1), P5.D (PA1)
UP2: IC15.4 (PA2), P5.E (PA2)
UP3: IC15.5 (PA3), P5.F (PA3)
UP4: IC15.6 (PA4), P5.H (PA4)
UP5: IC15.7 (PA5), P5.J (PA5)
UP6: IC15.8 (PA6), P5.K (PA6)
UP7: IC15.9 (PA7), P5.L (PA7)
UPCA1: IC15.40 (CA1), P5.B (CA1)
UPCB2/BEEP: IC15.19 (CB2), IC22.1 (I0), P5.M (CB2)
UPPWR: JP17.2, P5.2 (VIDEO)
V9V: C125.1, R75.2, T7.3 (C), T8.2 (C)
V33: J2.7 (VCC33)
VCC: C3.2, C10.2, C20.2, C28.2, C36.2, C37.2, C50.2, C51.1, C52.1, C53.1, C59.1, C60.1, C61.+, C62.1, CN2.2 (VCC), CN2.B (VCC@1), IC9.6 (G1), IC9.16 (VCC), IC11.16 (VCC), IC12.16 (VCC), IC15.20 (VCC), IC15.24 (CS1), IC17.20 (VCC), IC20.20 (VCC), IC21.14 (VCC), IC22.14 (VCC), IC23.5 (I1), IC23.9 (I0), IC23.14 (VCC), J2.9 (VCC5), JP17.1, P2.4 (VCC), P6.2 (VCC), P7.2 (VCC), R68.1, R69.1, R70.2, RN1.1, RN3.1, RN5.1, RN7.1, U14.4 (R), U14.8 (VCC), UX20.1 (DIR), UX20.20 (VCC), UX21.1 (DIR), UX21.20 (VCC)
VDRIVE: IC15.15 (PB5), IC17.18 (CB1), IC21.6 (O), P5.9 (VDRIVE), RN7.6
/BA2: IC17.22 (CS0), IC20.22 (CS0), IC48.2 (O)
/IRQ: J2.2 (/IRQ)
/LOCALIO: IC9.5 (G2B), JP21.2 (C)
/RES: J2.4 (/RES)
/SEL0: IC9.15 (Y0)
/SEL2: IC9.13 (Y2), IC20.23 (/CS2)
/SEL5: IC9.10 (Y5)

Notes on the sheet:
for WDC65C22 only
connect through otherwise
See Userport sheet for Input Multiplex
$e810-$e813
$E8xx/EFxx
1.0B: - fix IEEE488 pull up/down resistor values (again) 1.1A: - fully decode PIA addresses - replace some discrete Rs with RN7 - fix 2N2222 footprint for new BOM part 1.2A: - fix addressing 2nd SID by moving BA7 to IC9 - replace JP8 with a solder jumper (I/O block address) - replace 1N4148 with 1N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
CBM-ULTIPET-V1.3A
CBM-ULTIPET-V1.4A-20260507
(C) A. Fachat
$e84x
1-2: ATNA disabled 2-3: Control via C2 MTR
/IRQ pull-down diode
Killer Poke Protection
See sheet "Userport"
RESTORE to NMI from C64
To Pullups
$e820-$e823
