fachat/cbm_ultipet/Board/Power.kicad_sch

## KiCad design Board/Power.kicad_sch (2025-08-31)

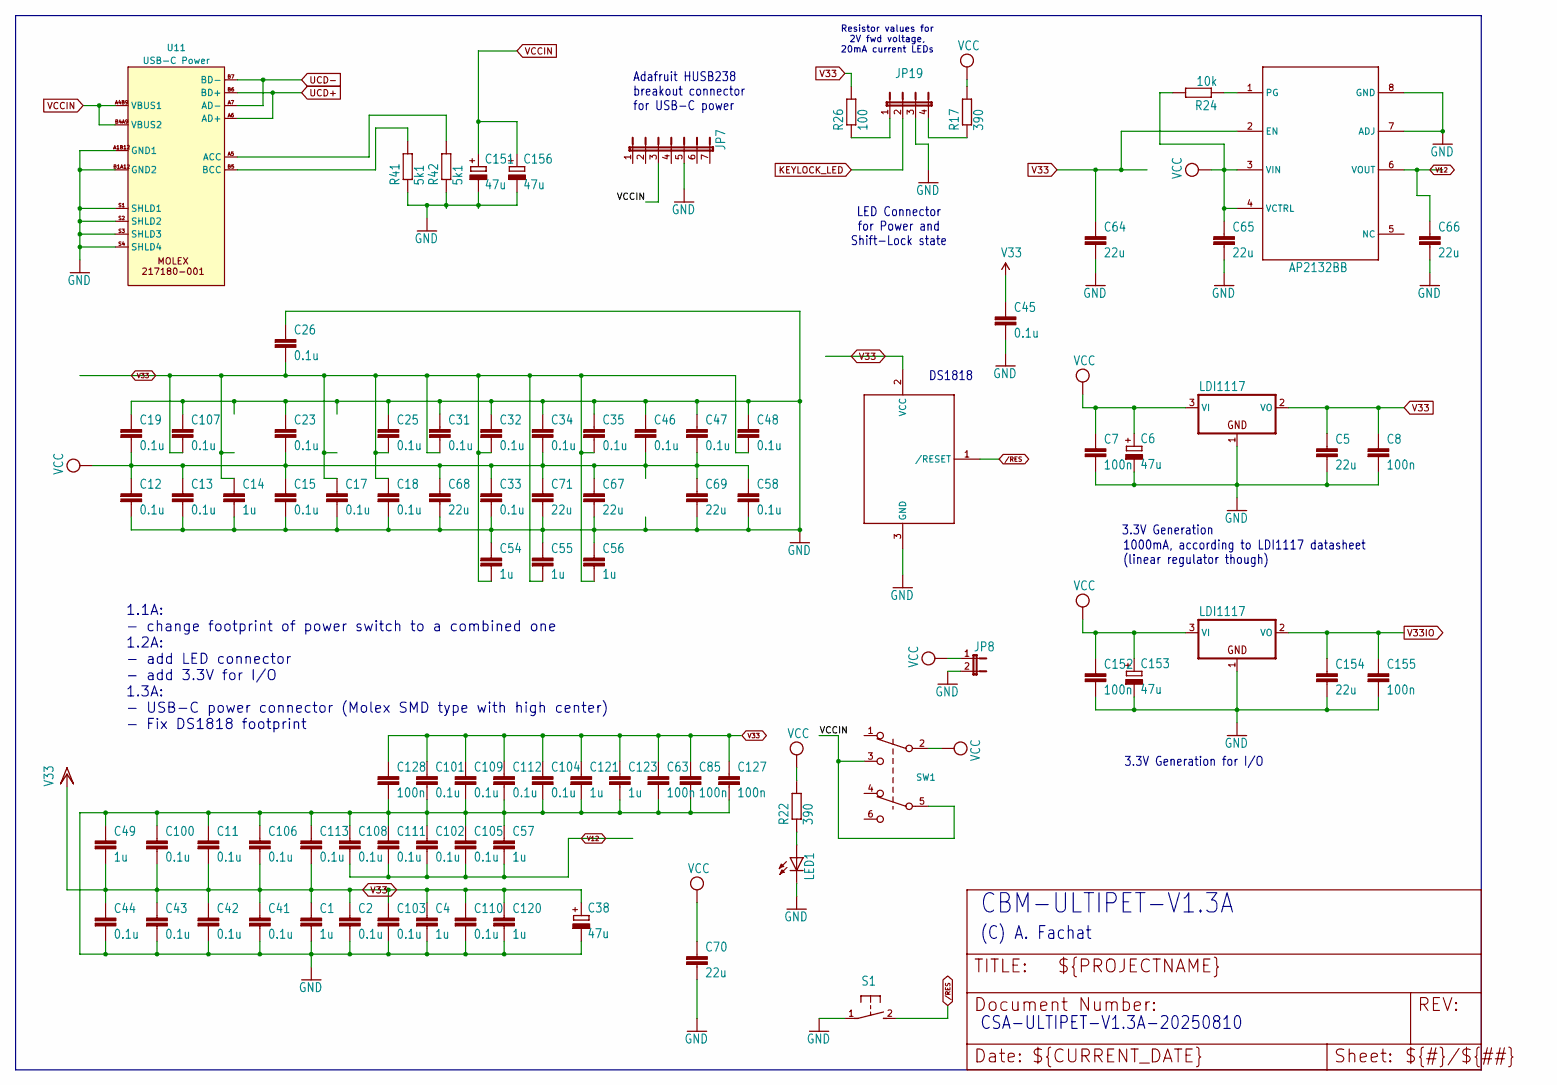
[picture p33: schematic Power.kicad_sch]

Parts:
C1, C4, C14, C49, C54, C55, C56, C57, C120, C121, C123: 1u; C0603
C2, C11, C12, C13, C15, C17, C18, C19, C23, C25, C26, C31, C32, C33, C34, C35, C41, C42, C43, C44, C45, C46, C47, C48, C58, C100, C101, C102, C103, C104, C105, C106, C107, C108, C109, C110, C111, C112, C113: 0.1u; C0603
C5, C64, C65, C66, C67, C68, C69, C70, C71, C154: 22u; C0805
C6, C38, C151, C153, C156: 47u; E2,5-6
C7, C8, C63, C85, C127, C128, C152, C155: 100n; C0603
DS1818: DS1813; TO-92_Inline
JP8: JP1E; JP1
JP19: JP4
LED1: LED3MM
R17, R22: 390; 0207_2V
R24: 10k; 0207_2V
R26: 100; 0207_2V
R41, R42: 5k1; 0207_2V
S1: 31-XX; B3F-31XX
SW1: SW_E-Switch-400-combined2
U11: USB-C Power; USB-C-217180
UX3, UX17: LDI1117; SOT223
UX16: AP2132BB; PSOP-8-FIXED
UX26: JP7

Connections:
/RES: DS1818.1 (/RESET), S1.2 (S)
GND: C1.2, C2.2, C4.2, C5.2, C6.-, C7.2, C8.2, C11.1, C12.2, C13.2, C14.2, C15.2, C17.2, C18.2, C19.1, C23.1, C25.1, C26.1, C31.1, C32.1, C33.2, C34.1, C35.1, C38.-, C41.2, C42.2, C43.2, C44.2, C45.2, C46.1, C47.1, C48.1, C49.1, C54.1, C55.1, C56.1, C57.1, C58.2, C63.2, C64.2, C65.2, C66.2, C67.2, C68.2, C69.2, C70.2, C71.2, C85.2, C100.1, C101.2, C102.1, C103.2, C104.2, C105.1, C106.1, C107.1, C108.1, C109.2, C110.2, C111.1, C112.2, C113.1, C120.2, C121.2, C123.2, C127.2, C128.2, C151.-, C152.2, C153.-, C154.2, C155.2, C156.-, DS1818.3 (GND), JP8.2, JP19.3, LED1.K (C), R41.1, R42.1, S1.1, U11.A1B12 (GND1), U11.B1A12 (GND2), U11.S1 (SHLD1), U11.S2 (SHLD2), U11.S3 (SHLD3), U11.S4 (SHLD4), UX3.1 (GND), UX16.7 (ADJ), UX16.8 (GND), UX17.1 (GND), UX26.5
KEYLOCK_LED: JP19.2
unnamed: JP19.1, R26.1
unnamed: JP19.4, R17.1
unnamed: LED1.A, R22.1
unnamed: R24.1, UX16.1 (PG)
unnamed: R41.2, U11.B5 (BCC)
unnamed: R42.2, U11.A5 (ACC)
UCD+: U11.A6 (AD+), U11.B6 (BD+)
UCD-: U11.A7 (AD-), U11.B7 (BD-)
V12: C57.2, C66.1, C102.2, C105.2, C108.2, C111.2, UX16.6 (VOUT)
V33: C1.1, C2.1, C4.1, C5.1, C8.1, C11.2, C14.1, C17.1, C18.1, C25.2, C26.2, C31.2, C32.2, C35.2, C38.+, C41.1, C42.1, C43.1, C44.1, C45.1, C48.2, C49.2, C54.2, C55.2, C56.2, C63.1, C64.1, C85.1, C100.2, C101.1, C103.1, C104.1, C106.2, C107.2, C109.1, C110.1, C112.1, C113.2, C120.1, C121.1, C123.1, C127.1, C128.1, DS1818.2 (VCC), R26.2, UX3.2 (VO), UX16.2 (EN)
V33IO: C154.1, C155.1, UX17.2 (VO)
VCC: C6.+, C7.1, C12.1, C13.1, C15.1, C19.2, C23.2, C33.1, C34.2, C46.2, C47.2, C58.1, C65.1, C67.1, C68.1, C69.1, C70.1, C71.1, C152.1, C153.+, JP8.1, R17.2, R22.2, R24.2, SW1.2, UX3.3 (VI), UX16.3 (VIN), UX16.4 (VCTRL), UX17.3 (VI)
VCCIN: C151.+, C156.+, SW1.3, SW1.5, U11.A4B9 (VBUS1), U11.B4A9 (VBUS2), UX26.3

Notes on the sheet:
1000mA, according to LDI1117 datasheet (linear regulator though)
CBM-ULTIPET-V1.3A
3.3V Generation
1.1A: - change footprint of power switch to a combined one 1.2A: - add LED connector - add 3.3V for I/O 1.3A: - USB-C power connector (Molex SMD type with high center) - Fix DS1818 footprint
(C) A. Fachat
Adafruit HUSB238 breakout connector for USB-C power
LED Connector for Power and Shift-Lock state
3.3V Generation for I/O
Resistor values for 2V fwd voltage, 20mA current LEDs
DS1818
CSA-ULTIPET-V1.3A-20250810
