fachat/cbm_ultipet/Board/SID.kicad_sch

## KiCad design Board/SID.kicad_sch (2026-05-08)

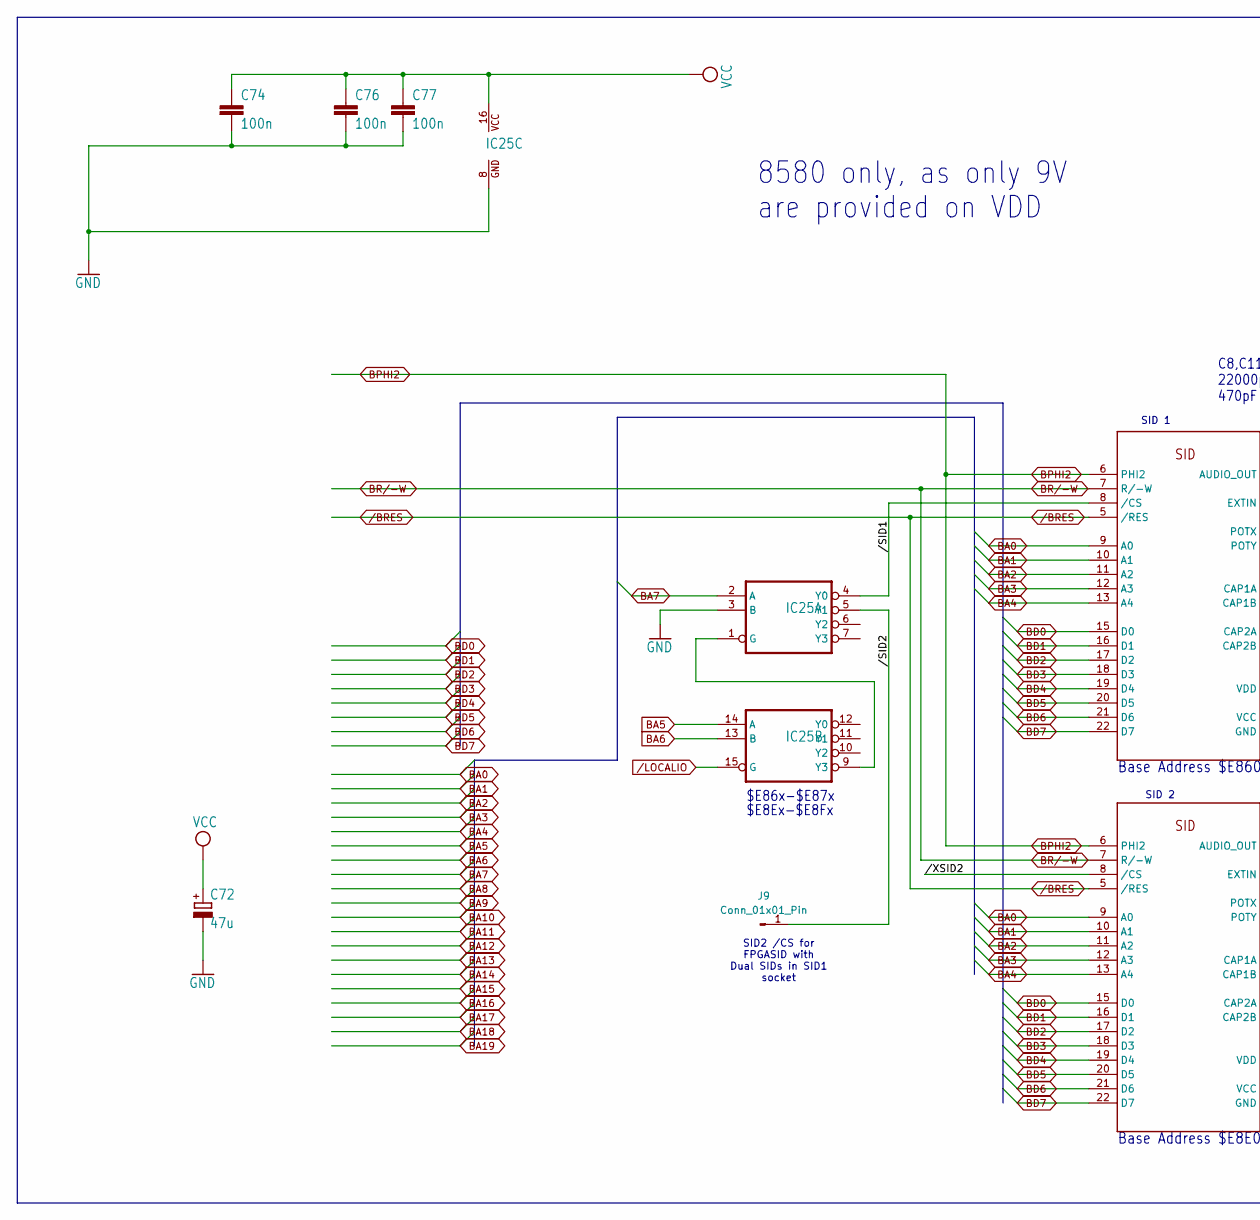
[picture p34: schematic SID.kicad_sch, part in row 1, column 1]

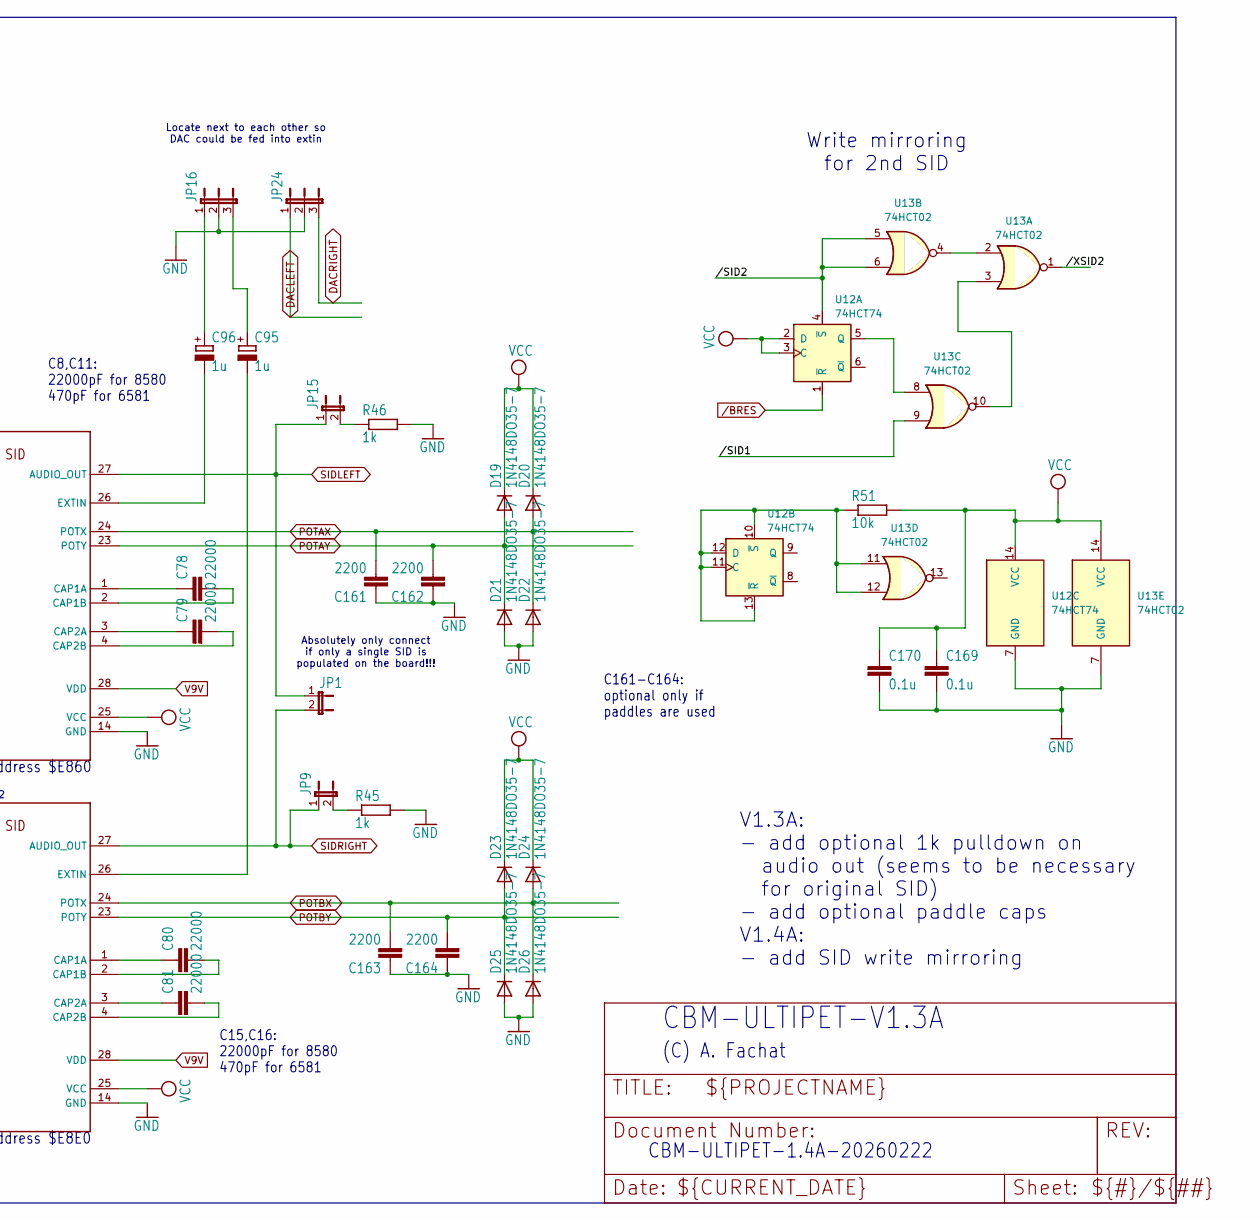
[picture p35: schematic SID.kicad_sch, part in row 1, column 2]

Parts:
C72: 47u; E2,5-6
C74, C76, C77: 100n; C025-025X050
C78, C79, C80, C81: 22000; C025-025X050
C95, C96: 1u; E2-5
C161, C162, C163, C164: 2200; C025-025X050
C169, C170: 0.1u; C0603
D19, D20, D21, D22, D23, D24, D25, D26: 1N4148DO35-7; DO35-7
IC25: 74139N; DIP-16_W7.62mm_Socket_LongPads
J9: Conn_01x01_Pin; PinHeader_1x01_P2.54mm_Vertical
JP1, JP9, JP15: JP1E; JP1
JP16, JP24: JP2E; JP2
R45, R46: 1k; 0207_10
R51: 10k; R_0805_2012Metric_Pad1.20x1.40mm_HandSolder
U12: 74HCT74; SOIC-14_3.9x8.7mm_P1.27mm
U13: 74HCT02; SOIC-14_3.9x8.7mm_P1.27mm
UX22, UX23: SID; DIP-28_W15.24mm_Socket_LongPads

Connections:
/BRES: UX22.5 (/RES), UX23.5 (/RES)
BA0: UX22.9 (A0), UX23.9 (A0)
BA1: UX22.10 (A1), UX23.10 (A1)
BA2: UX22.11 (A2), UX23.11 (A2)
BA3: UX22.12 (A3), UX23.12 (A3)
BA4: UX22.13 (A4), UX23.13 (A4)
BA5: IC25.14 (A)
BA6: IC25.13 (B)
BA7: IC25.2 (A)
BD0: UX22.15 (D0), UX23.15 (D0)
BD1: UX22.16 (D1), UX23.16 (D1)
BD2: UX22.17 (D2), UX23.17 (D2)
BD3: UX22.18 (D3), UX23.18 (D3)
BD4: UX22.19 (D4), UX23.19 (D4)
BD5: UX22.20 (D5), UX23.20 (D5)
BD6: UX22.21 (D6), UX23.21 (D6)
BD7: UX22.22 (D7), UX23.22 (D7)
BPHI2: UX22.6 (PHI2), UX23.6 (PHI2)
BR/-W: UX22.7 (R/-W), UX23.7 (R/-W)
DACLEFT: JP24.1
DACRIGHT: JP24.3
GND: C72.-, C74.2, C76.2, C77.2, C161.1, C162.1, C163.1, C164.1, C169.2, C170.2, D21.A, D22.A, D25.A, D26.A, IC25.3 (B), IC25.8 (GND), JP16.2, JP24.2, R45.2, R46.2, U12.7 (GND), U13.7 (GND), UX22.14 (GND), UX23.14 (GND)
unnamed: C78.1, UX22.1 (CAP1A)
unnamed: C78.2, UX22.2 (CAP1B)
unnamed: C79.1, UX22.3 (CAP2A)
unnamed: C79.2, UX22.4 (CAP2B)
unnamed: C80.1, UX23.1 (CAP1A)
unnamed: C80.2, UX23.2 (CAP1B)
unnamed: C81.1, UX23.3 (CAP2A)
unnamed: C81.2, UX23.4 (CAP2B)
unnamed: C95.+, JP16.3
unnamed: C95.-, UX23.26 (EXTIN)
unnamed: C96.+, JP16.1
unnamed: C96.-, UX22.26 (EXTIN)
unnamed: IC25.1 (G), IC25.9 (Y3)
unnamed: JP9.2, R45.1
unnamed: JP15.2, R46.1
unnamed: R51.1, U12.10 (~S), U12.11 (C), U12.12 (D), U12.13 (~R), U13.11, U13.12
unnamed: U12.5 (Q), U13.8
unnamed: U13.2, U13.4
unnamed: U13.3, U13.10
POTAX: C161.2, D20.A, D22.C, UX22.24 (POTX)
POTAY: C162.2, D19.A, D21.C, UX22.23 (POTY)
POTBX: C163.2, D24.A, D26.C, UX23.24 (POTX)
POTBY: C164.2, D23.A, D25.C, UX23.23 (POTY)
SIDLEFT: JP1.1, JP15.1, UX22.27 (AUDIO_OUT)
SIDRIGHT: JP1.2, JP9.1, UX23.27 (AUDIO_OUT)
V9V: UX22.28 (VDD), UX23.28 (VDD)
VCC: C72.+, C74.1, C76.1, C77.1, C169.1, C170.1, D19.C, D20.C, D23.C, D24.C, IC25.16 (VCC), R51.2, U12.2 (D), U12.3 (C), U12.14 (VCC), U13.14 (VCC), UX22.25 (VCC), UX23.25 (VCC)
/BRES: U12.1 (~R)
/LOCALIO: IC25.15 (G)
/SID1: IC25.4 (Y0), U13.9, UX22.8 (/CS)
/SID2: IC25.5 (Y1), J9.1, U12.4 (~S), U13.5, U13.6
/XSID2: U13.1, UX23.8 (/CS)

Notes on the sheet:
Base Address $E860
SID2 /CS for FPGASID with Dual SIDs in SID1 socket
CBM-ULTIPET-V1.3A
SID 1
8580 only, as only 9V are provided on VDD
C161-C164: optional only if paddles are used
CBM-ULTIPET-1.4A-20260222
Base Address $E8E0
SID 2
C8,C11: 22000pF for 8580 470pF for 6581
Absolutely only connect if only a single SID is populated on the board!!!
(C) A. Fachat
C15,C16: 22000pF for 8580 470pF for 6581
V1.3A: - add optional 1k pulldown on audio out (seems to be necessary for original SID) - add optional paddle caps V1.4A: - add SID write mirroring
$E8Ex-$E8Fx
Locate next to each other so DAC could be fed into extin
Write mirroring for 2nd SID
$E86x-$E87x
