fachat/cbm_ultipet/Board/SID_Power.kicad_sch

## KiCad design Board/SID_Power.kicad_sch (2025-08-31)

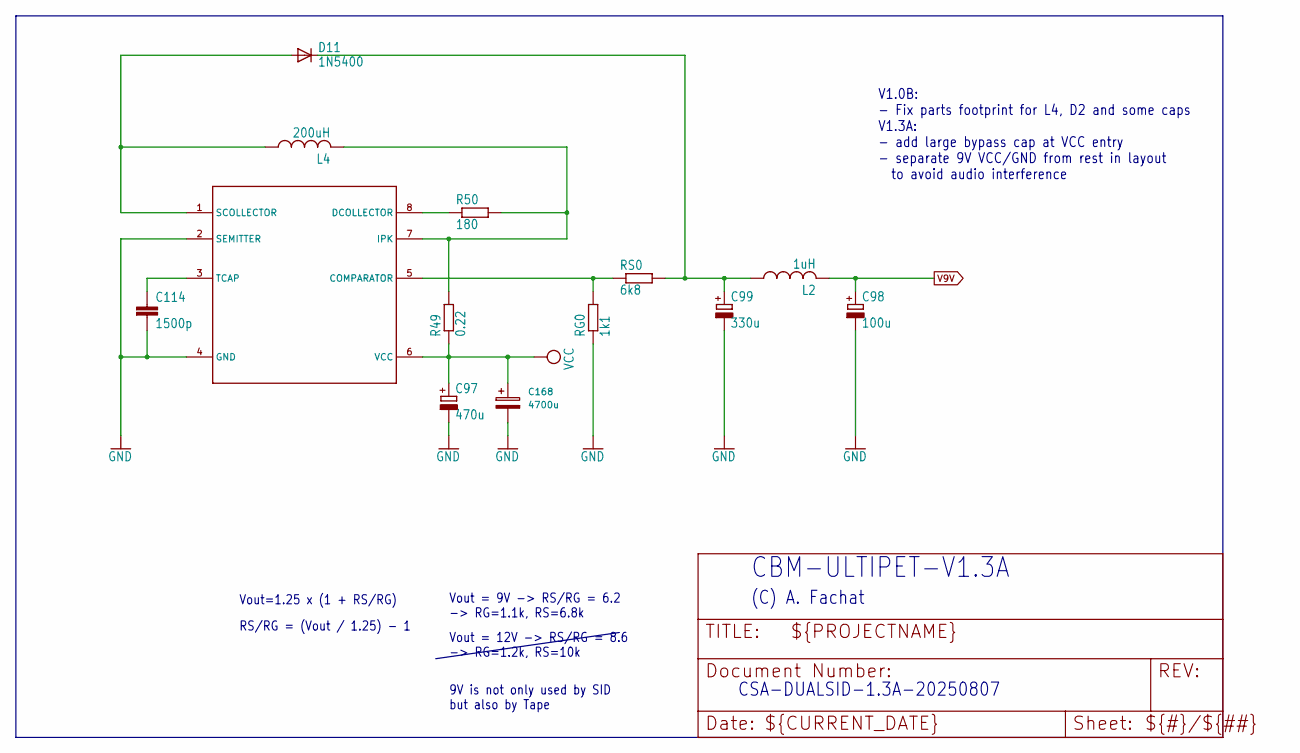
[picture p36: schematic SID_Power.kicad_sch]

Parts:
C97: 470u; E2,5-7
C98: 100u; E2-5
C99: 330u; E2,5-7
C114: 1500p; C025-024X044
C168: 4700u; CP_Radial_D16.0mm_P7.50mm
D11: 1N5400; DO201-15
L2: 1uH; 0204_7@1
L4: 200uH; TJ4-U2
R49: 0.22; 0204_7
R50: 180; 0204_7
RG0: 1k1; 0204_7
RS0: 6k8; 0204_7
UX24: MC34063A; DIP-8_W7.62mm_Socket_LongPads

Connections:
GND: C97.-, C98.-, C99.-, C114.2, C168.2, RG0.1, UX24.2 (SEMITTER), UX24.4 (GND)
unnamed: C99.+, D11.C, L2.1, RS0.2
unnamed: C114.1, UX24.3 (TCAP)
unnamed: D11.A, L4.1, UX24.1 (SCOLLECTOR)
unnamed: L4.2, R49.2, R50.2, UX24.7 (IPK)
unnamed: R50.1, UX24.8 (DCOLLECTOR)
unnamed: RG0.2, RS0.1, UX24.5 (COMPARATOR)
V9V: C98.+, L2.2
VCC: C97.+, C168.1, R49.1, UX24.6 (VCC)

Notes on the sheet:
CSA-DUALSID-1.3A-20250807
Vout = 12V -> RS/RG = 8.6 -> RG=1.2k, RS=10k
Vout = 9V -> RS/RG = 6.2 -> RG=1.1k, RS=6.8k
(C) A. Fachat
CBM-ULTIPET-V1.3A
9V is not only used by SID but also by Tape
Vout=1.25 x (1 + RS/RG)
V1.0B: - Fix parts footprint for L4, D2 and some caps V1.3A: - add large bypass cap at VCC entry - separate 9V VCC/GND from rest in layout to avoid audio interference
RS/RG = (Vout / 1.25) - 1
