fachat/cbm_ultipet/Board/Smallbus.kicad_sch

## KiCad design Board/Smallbus.kicad_sch (2025-08-31)

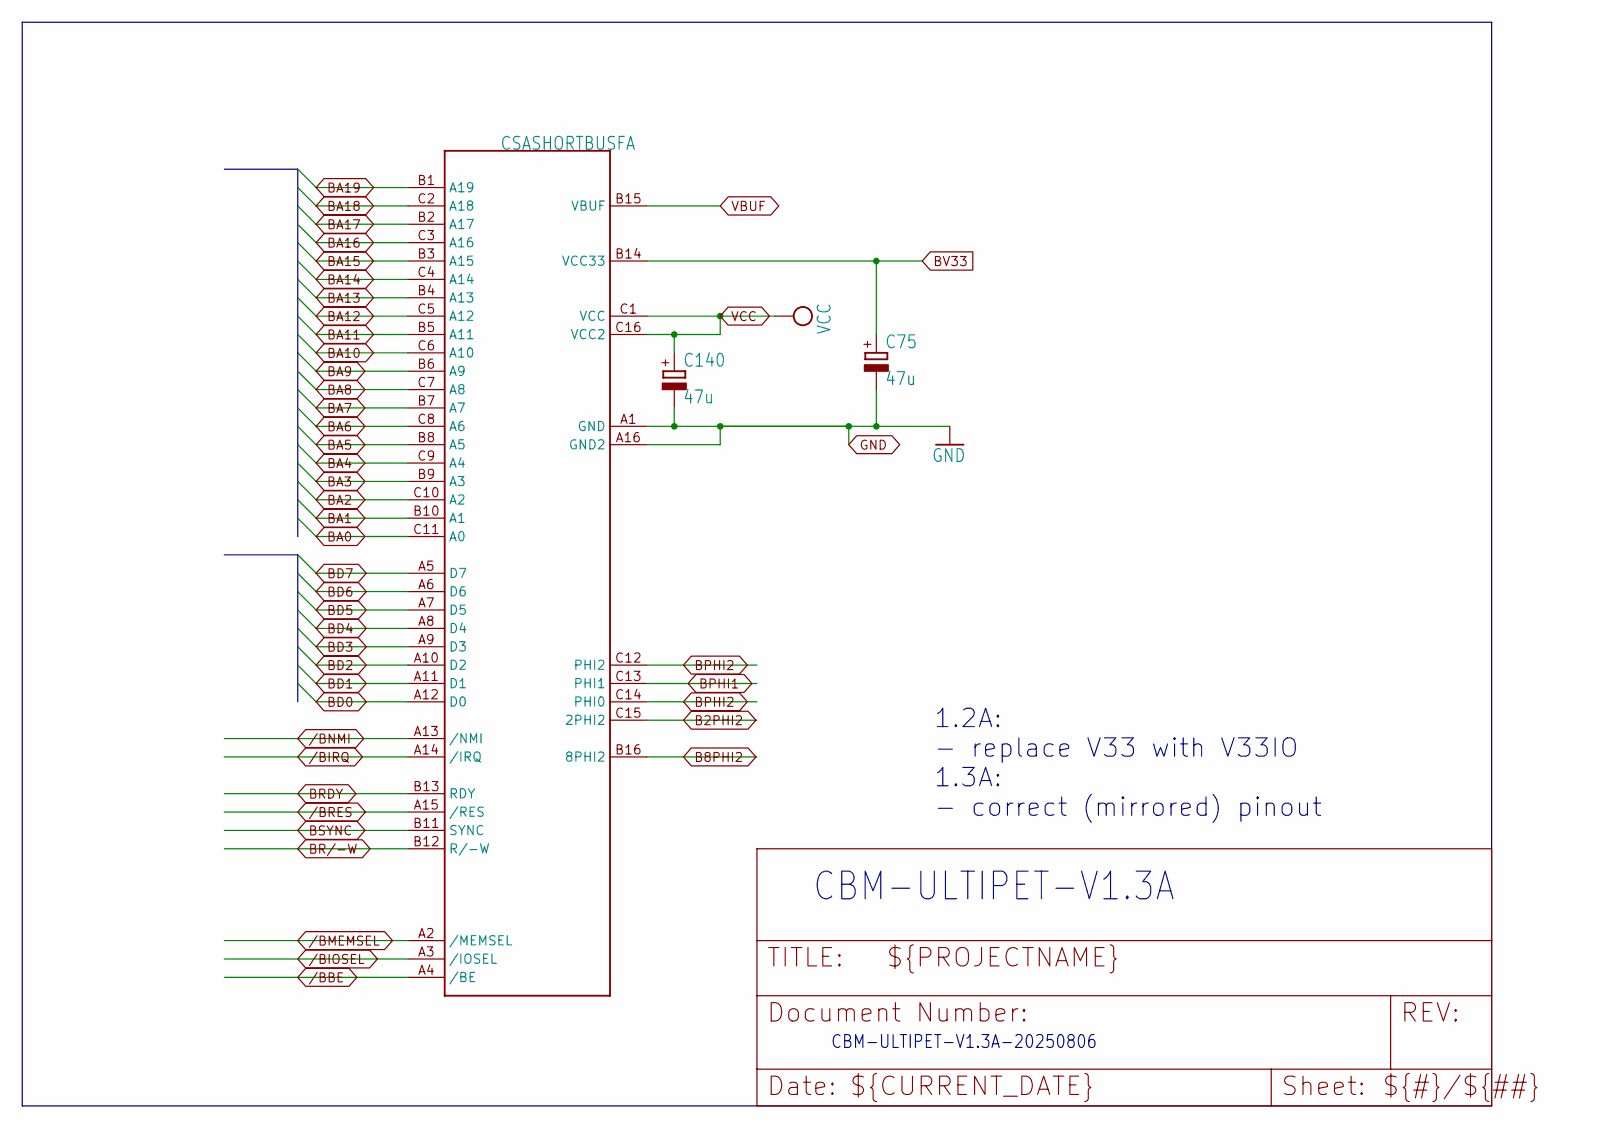
[picture p37: schematic Smallbus.kicad_sch]

Parts:
C75, C140: 47u; E2,5-6
UX25: CSASHORTBUSFA; FABC48R2-reversed

Connections:
/BBE: UX25.A4 (/BE)
/BIOSEL: UX25.A3 (/IOSEL)
/BIRQ: UX25.A14 (/IRQ)
/BMEMSEL: UX25.A2 (/MEMSEL)
/BNMI: UX25.A13 (/NMI)
/BRES: UX25.A15 (/RES)
B2PHI2: UX25.C15 (2PHI2)
B8PHI2: UX25.B16 (8PHI2)
BA0: UX25.C11 (A0)
BA1: UX25.B10 (A1)
BA2: UX25.C10 (A2)
BA3: UX25.B9 (A3)
BA4: UX25.C9 (A4)
BA5: UX25.B8 (A5)
BA6: UX25.C8 (A6)
BA7: UX25.B7 (A7)
BA8: UX25.C7 (A8)
BA9: UX25.B6 (A9)
BA10: UX25.C6 (A10)
BA11: UX25.B5 (A11)
BA12: UX25.C5 (A12)
BA13: UX25.B4 (A13)
BA14: UX25.C4 (A14)
BA15: UX25.B3 (A15)
BA16: UX25.C3 (A16)
BA17: UX25.B2 (A17)
BA18: UX25.C2 (A18)
BA19: UX25.B1 (A19)
BD0: UX25.A12 (D0)
BD1: UX25.A11 (D1)
BD2: UX25.A10 (D2)
BD3: UX25.A9 (D3)
BD4: UX25.A8 (D4)
BD5: UX25.A7 (D5)
BD6: UX25.A6 (D6)
BD7: UX25.A5 (D7)
BPHI1: UX25.C13 (PHI1)
BPHI2: UX25.C12 (PHI2), UX25.C14 (PHI0)
BR/-W: UX25.B12 (R/-W)
BRDY: UX25.B13 (RDY)
BSYNC: UX25.B11 (SYNC)
BV33: C75.+, UX25.B14 (VCC33)
GND: C75.-, C140.-, UX25.A1 (GND), UX25.A16 (GND2)
VBUF: UX25.B15 (VBUF)
VCC: C140.+, UX25.C1 (VCC), UX25.C16 (VCC2)

Notes on the sheet:
CBM-ULTIPET-V1.3A
1.2A: - replace V33 with V33IO 1.3A: - correct (mirrored) pinout
CBM-ULTIPET-V1.3A-20250806
