fachat/cbm_ultipet/Board/UART.kicad_sch

## KiCad design Board/UART.kicad_sch (2025-08-31)

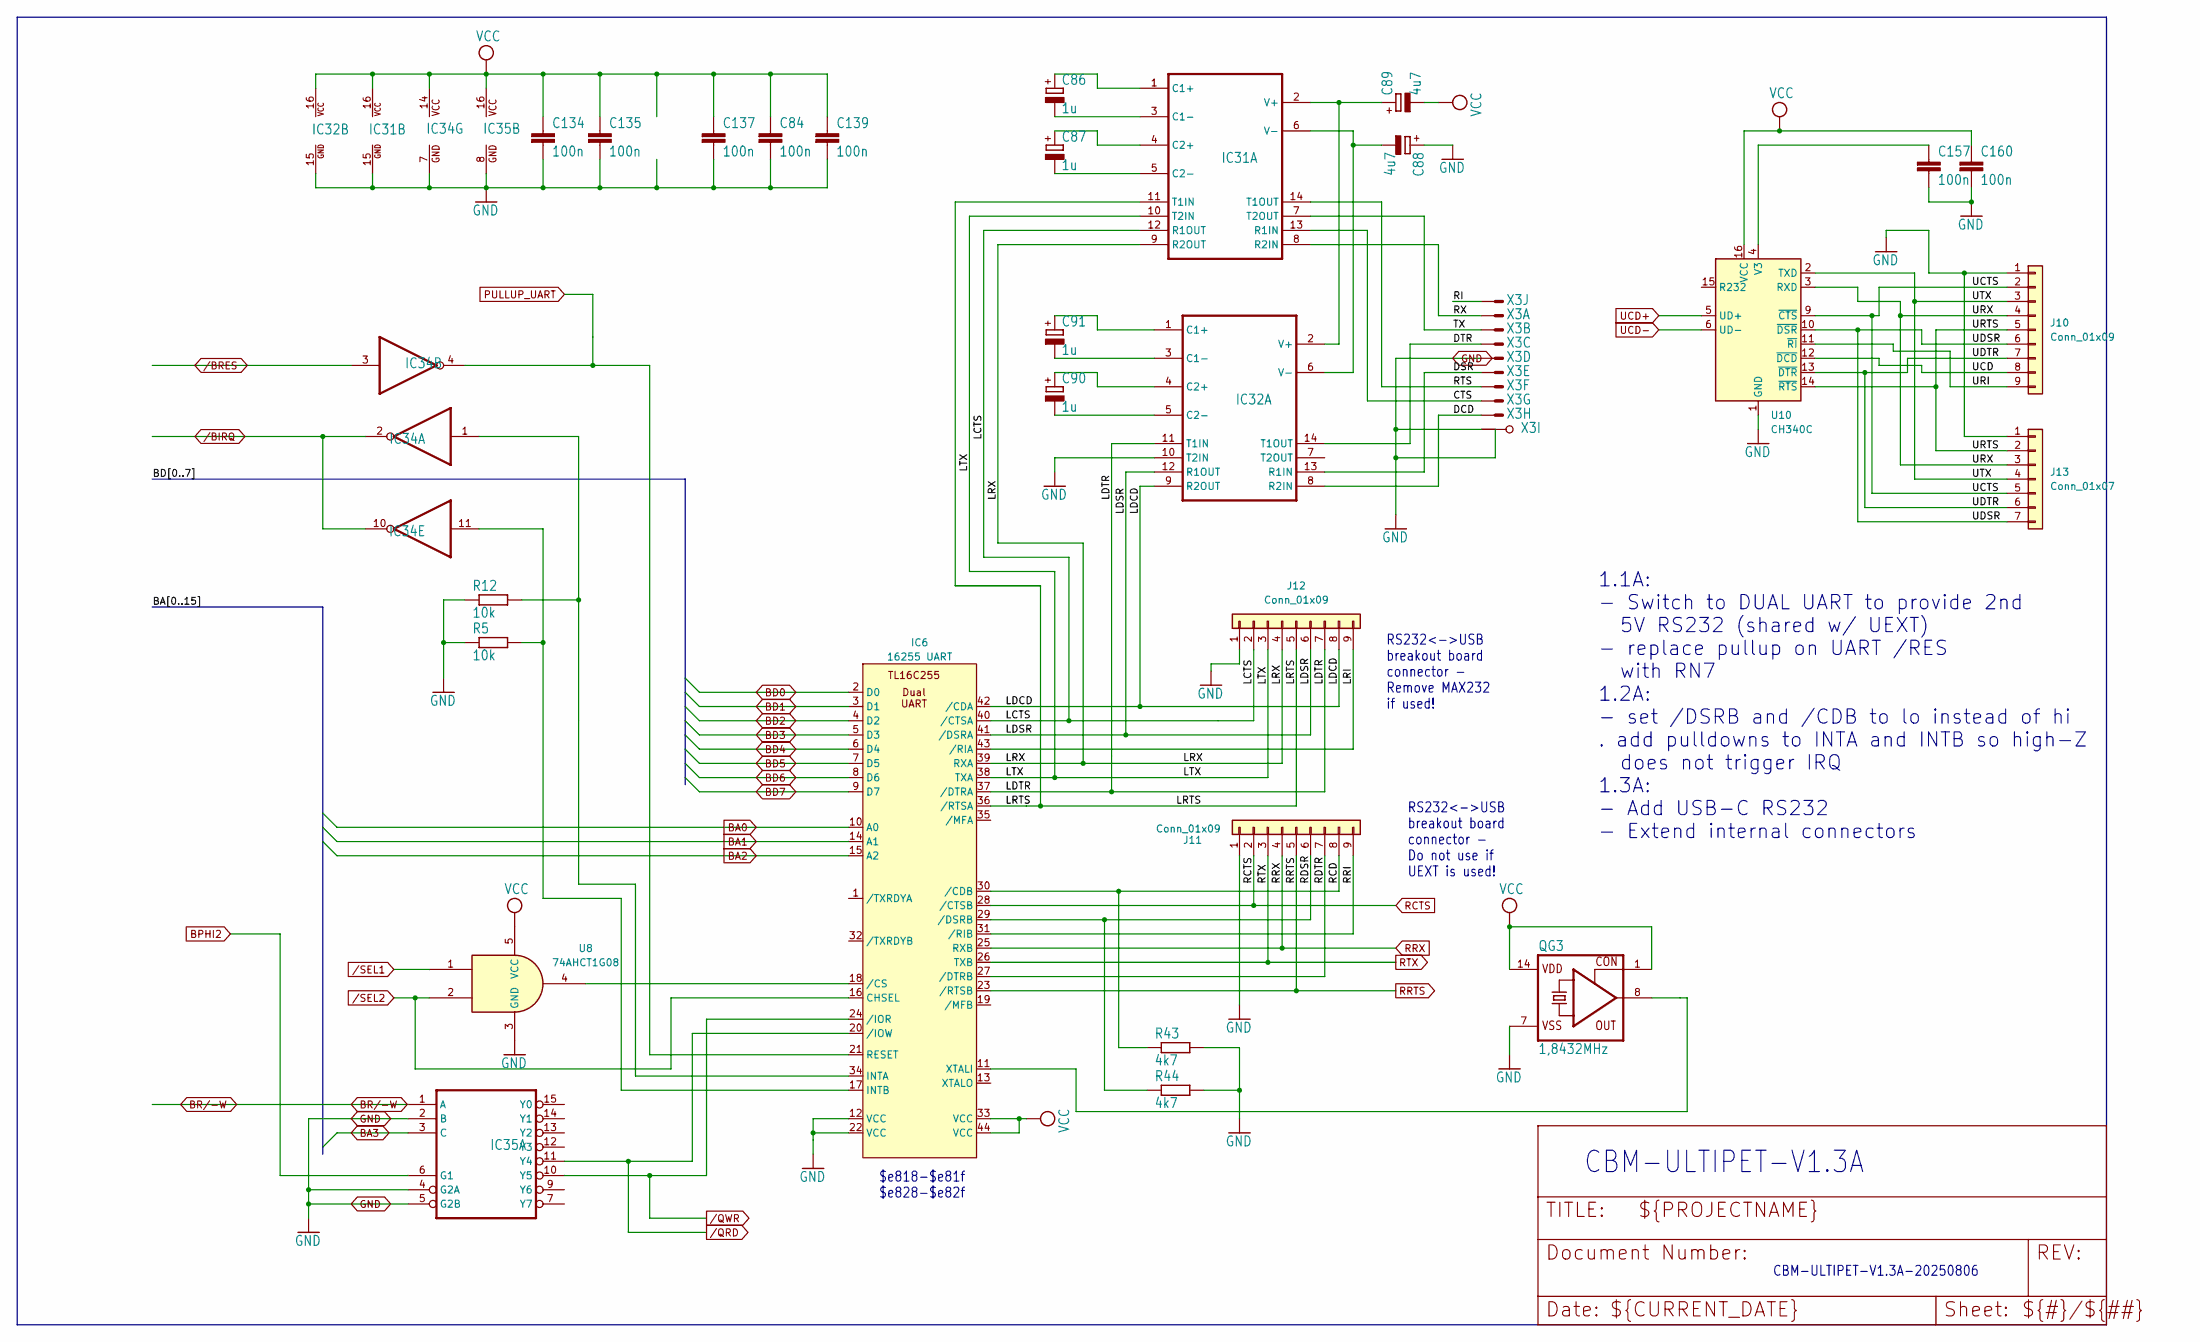
[picture p38: schematic UART.kicad_sch]

Parts:
C84, C134, C135, C137, C139: 100n; C025-024X044
C86, C87, C90, C91: 1u; E2-5
C88, C89: 4u7; E2,5-6
C157, C160: 100n; C0603
IC6: 16255 UART; PLCC-44_THT-Socket
IC31, IC32: MAX232; DIP-16_W7.62mm_Socket_LongPads
IC34: 7406N; DIP-14_W7.62mm_Socket_LongPads
IC35: 74138N; DIP-16_W7.62mm_Socket_LongPads
J10, J11, J12: Conn_01x09; PinHeader_1x09_P2.54mm_Vertical
J13: Conn_01x07; PinHeader_1x07_P2.54mm_Vertical
QG3: 1,8432MHz; SG51
R5, R12: 10k; 0207_10
R43, R44: 4k7; 0207_10
U8: 74AHCT1G08; TSOP-5_1.65x3.05mm_P0.95mm
U10: CH340C; SOIC-16_3.9x9.9mm_P1.27mm
X3: M09HPS; M09HP

Connections:
/BIRQ: IC34.2 (O), IC34.10 (O)
/BRES: IC34.3 (I)
BA0: IC6.10 (A0)
BA1: IC6.14 (A1)
BA2: IC6.15 (A2)
BA3: IC35.3 (C)
BD0: IC6.2 (D0)
BD1: IC6.3 (D1)
BD2: IC6.4 (D2)
BD3: IC6.5 (D3)
BD4: IC6.6 (D4)
BD5: IC6.7 (D5)
BD6: IC6.8 (D6)
BD7: IC6.9 (D7)
BPHI2: IC35.6 (G1)
BR/-W: IC35.1 (A)
CTS: IC31.13 (R1IN), X3.8 (M)
DCD: IC32.8 (R2IN), X3.9 (M)
DSR: IC32.13 (R1IN), X3.6 (M)
DTR: IC32.14 (T1OUT), X3.4 (M)
GND: C84.2, C88.+, C134.2, C135.2, C137.2, C139.2, C157.2, C160.2, IC6.12 (VCC), IC6.22 (VCC), IC31.15 (GND), IC32.10 (T2IN), IC32.15 (GND), IC34.7 (GND), IC35.2 (B), IC35.4 (G2A), IC35.5 (G2B), IC35.8 (GND), J10.1, J11.1, J12.1, J13.1, QG3.7 (VSS), R5.1, R12.1, R43.2, R44.2, U8.3 (GND), U10.1 (GND), X3.5 (M), X3.G1, X3.G2
LCTS: IC6.40 (/CTSA), IC31.12 (R1OUT), J12.2
LDCD: IC6.42 (/CDA), IC32.9 (R2OUT), J12.8
LDSR: IC6.41 (/DSRA), IC32.12 (R1OUT), J12.6
LDTR: IC6.37 (/DTRA), IC32.11 (T1IN), J12.7
LRI: IC6.43 (/RIA), J12.9
LRTS: IC6.36 (/RTSA), IC31.11 (T1IN), J12.5
LRX: IC6.39 (RXA), IC31.9 (R2OUT), J12.4
LTX: IC6.38 (TXA), IC31.10 (T2IN), J12.3
unnamed: C86.+, IC31.1 (C1+)
unnamed: C86.-, IC31.3 (C1-)
unnamed: C87.+, IC31.4 (C2+)
unnamed: C87.-, IC31.5 (C2-)
unnamed: C88.-, IC31.6 (V-), IC32.6 (V-)
unnamed: C89.+, IC31.2 (V+), IC32.2 (V+)
unnamed: C90.+, IC32.4 (C2+)
unnamed: C90.-, IC32.5 (C2-)
unnamed: C91.+, IC32.1 (C1+)
unnamed: C91.-, IC32.3 (C1-)
unnamed: C157.1, U10.4 (V3)
unnamed: IC6.11 (XTALI), QG3.8 (OUT)
unnamed: IC6.18 (/CS), U8.4
unnamed: IC6.34 (INTA), IC34.1 (I), R12.2
unnamed: IC6.17 (INTB), IC34.11 (I), R5.2
PULLUP_UART: IC6.21 (RESET), IC34.4 (O)
RCD: IC6.30 (/CDB), J11.8, R43.1
RCTS: IC6.28 (/CTSB), J11.2
RDSR: IC6.29 (/DSRB), J11.6, R44.1
RDTR: IC6.27 (/DTRB), J11.7
RI: X3.1 (M)
RRI: IC6.31 (/RIB), J11.9
RRTS: IC6.23 (/RTSB), J11.5
RRX: IC6.25 (RXB), J11.4
RTS: IC31.14 (T1OUT), X3.7 (M)
RTX: IC6.26 (TXB), J11.3
RX: IC31.8 (R2IN), X3.2 (M)
TX: IC31.7 (T2OUT), X3.3 (M)
UCD: J10.8, U10.12 (~DCD)
UCD+: U10.5 (UD+)
UCD-: U10.6 (UD-)
UCTS: J10.2, J13.5, U10.9 (~CTS)
UDSR: J10.6, J13.7, U10.10 (~DSR)
UDTR: J10.7, J13.6, U10.13 (~DTR)
URI: J10.9, U10.11 (~RI)
URTS: J10.5, J13.2, U10.14 (~RTS)
URX: J10.4, J13.3, U10.3 (RXD)
UTX: J10.3, J13.4, U10.2 (TXD)
VCC: C84.1, C89.-, C134.1, C135.1, C137.1, C139.1, C160.1, IC6.33 (VCC), IC6.44 (VCC), IC31.16 (VCC), IC32.16 (VCC), IC34.14 (VCC), IC35.16 (VCC), QG3.1 (CON), QG3.14 (VDD), U8.5 (VCC), U10.16 (VCC)
/QRD: IC6.20 (/IOW), IC35.11 (Y4)
/QWR: IC6.24 (/IOR), IC35.10 (Y5)
/SEL1: U8.1
/SEL2: IC6.16 (CHSEL), U8.2

Notes on the sheet:
CBM-ULTIPET-V1.3A
RS232<->USB breakout board connector - Do not use if UEXT is used!
$e818-$e81f $e828-$e82f
CBM-ULTIPET-V1.3A-20250806
1.1A: - Switch to DUAL UART to provide 2nd 5V RS232 (shared w/ UEXT) - replace pullup on UART /RES with RN7 1.2A: - set /DSRB and /CDB to lo instead of hi . add pulldowns to INTA and INTB so high-Z does not trigger IRQ 1.3A: - Add USB-C RS232 - Extend internal connectors
RS232<->USB breakout board connector - Remove MAX232 if used!
