fachat/cbm_ultipet/Board/USB.kicad_sch

## KiCad design Board/USB.kicad_sch (2025-08-31)

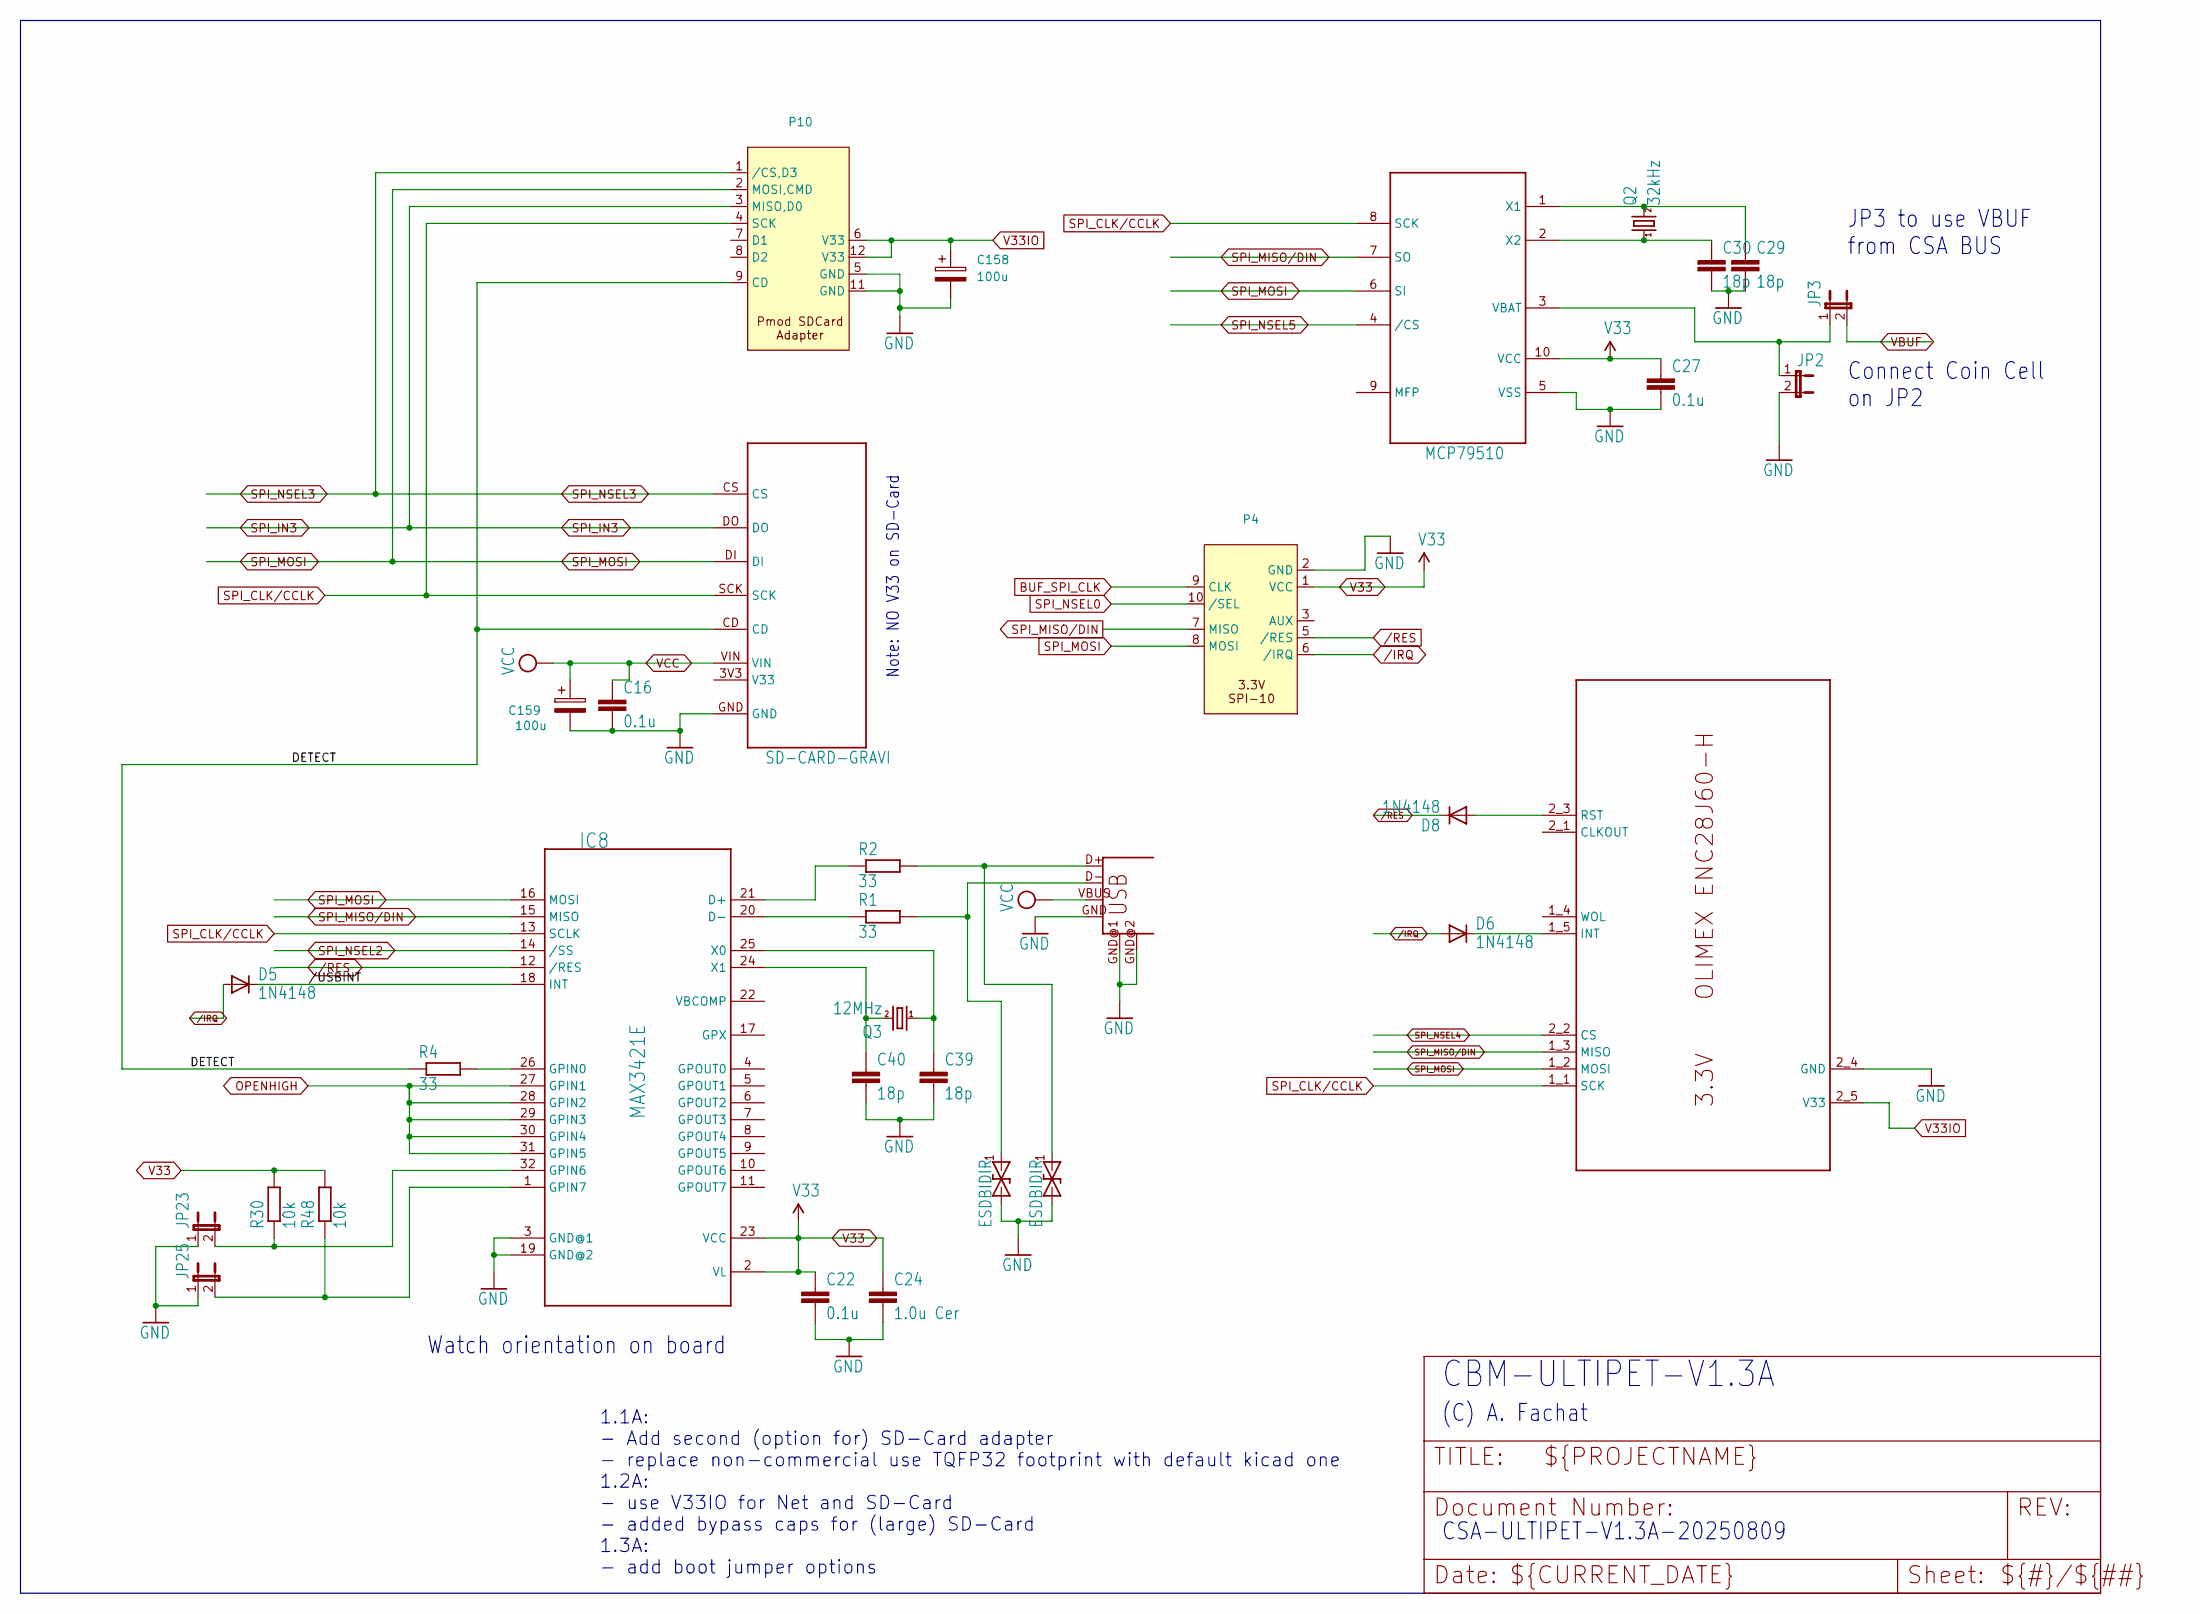
[picture p39: schematic USB.kicad_sch]

Parts:
C16, C22, C27: 0.1u; C0603
C24: 1.0u Cer; C0603
C29, C30, C39, C40: 18p; C0603
C158, C159: 100u; CP_Radial_D5.0mm_P2.00mm
D5, D6, D8: 1N4148; D-5
IC8: MAX3421E; LQFP-32_5x5mm_P0.5mm
JP2, JP3, JP23, JP25: JP1E; JP1
P4: IDC-Header_2x05_P2.54mm_Vertical
P10: Pmod-SDCard
Q2: 32kHz; TC26H
Q3: 12MHz; HC49_S
R1, R2, R4: 33; 0204_7
R30, R48: 10k; R_0805_2012Metric_Pad1.20x1.40mm_HandSolder
USB1: USB-A-H
UX9: ETHOLIENC
UX12: SD-CARD-GRAVI; GRAVITECH-SDCARD
UX13: MCP79510; MSOP10
UX14, UX15: ESDBIDIR; SOD323

Connections:
/IRQ: D5.A, D6.A
/RES: D8.C, IC8.12 (/RES)
/USBINT: D5.C, IC8.18 (INT)
BUF_SPI_CLK: P4.9 (CLK)
DETECT: P10.9 (CD), R4.1, UX12.CD
GND: C16.2, C22.2, C24.2, C27.2, C29.2, C30.2, C39.2, C40.2, C158.2, C159.2, IC8.3 (GND@1), IC8.19 (GND@2), JP2.2, JP23.1, JP25.1, P4.2 (GND), P10.5 (GND), P10.11 (GND), USB1.GND, USB1.GND@1, USB1.GND@2, UX9.2_4 (GND), UX12.GND, UX13.5 (VSS), UX14.1 (2), UX15.1 (2)
unnamed: C29.1, Q2.2, UX13.1 (X1)
unnamed: C30.1, Q2.1, UX13.2 (X2)
unnamed: C39.1, IC8.25 (X0), Q3.1
unnamed: C40.1, IC8.24 (X1), Q3.2
unnamed: D6.C, UX9.1_5 (INT)
unnamed: D8.A, UX9.2_3 (RST)
unnamed: IC8.1 (GPIN7), JP25.2, R48.1
unnamed: IC8.20 (D-), R1.1
unnamed: IC8.21 (D+), R2.1
unnamed: IC8.26 (GPIN0), R4.2
unnamed: IC8.32 (GPIN6), JP23.2, R30.1
unnamed: JP2.1, JP3.1, UX13.3 (VBAT)
unnamed: R1.2, USB1.D-, UX15.2 (1)
unnamed: R2.2, USB1.D+, UX14.2 (1)
OPENHIGH: IC8.27 (GPIN1), IC8.28 (GPIN2), IC8.29 (GPIN3), IC8.30 (GPIN4), IC8.31 (GPIN5)
SPI_CLK/CCLK: IC8.13 (SCLK), P10.4 (SCK), UX9.1_1 (SCK), UX12.SCK, UX13.8 (SCK)
SPI_IN3: P10.3 (MISO,D0), UX12.DO
SPI_MISO/DIN: IC8.15 (MISO), UX9.1_3 (MISO), UX13.7 (SO)
SPI_MISO/DIN: P4.7 (MISO)
SPI_MOSI: IC8.16 (MOSI), P4.8 (MOSI), P10.2 (MOSI,CMD), UX9.1_2 (MOSI), UX12.DI, UX13.6 (SI)
SPI_NSEL0: P4.10 (/SEL)
SPI_NSEL2: IC8.14 (/SS)
SPI_NSEL3: P10.1 (/CS,D3), UX12.CS
SPI_NSEL4: UX9.2_2 (CS)
SPI_NSEL5: UX13.4 (/CS)
V33: C22.1, C24.1, C27.1, IC8.2 (VL), IC8.23 (VCC), P4.1 (VCC), R30.2, R48.2, UX13.10 (VCC)
V33IO: C158.1, P10.6 (V33), P10.12 (V33), UX9.2_5 (V33)
VBUF: JP3.2
VCC: C16.1, C159.1, USB1.VBUS, UX12.VIN
/IRQ: P4.6 (/IRQ)
/RES: P4.5 (/RES)

Notes on the sheet:
CBM-ULTIPET-V1.3A
Connect Coin Cell on JP2
JP3 to use VBUF from CSA BUS
1.1A: - Add second (option for) SD-Card adapter - replace non-commercial use TQFP32 footprint with default kicad one 1.2A: - use V33IO for Net and SD-Card - added bypass caps for (large) SD-Card 1.3A: - add boot jumper options
CSA-ULTIPET-V1.3A-20250809
(C) A. Fachat
Watch orientation on board~{}
Note: NO V33 on SD-Card
