fachat/cbm_ultipet/Board/Userport.kicad_sch

## KiCad design Board/Userport.kicad_sch (2025-08-31)

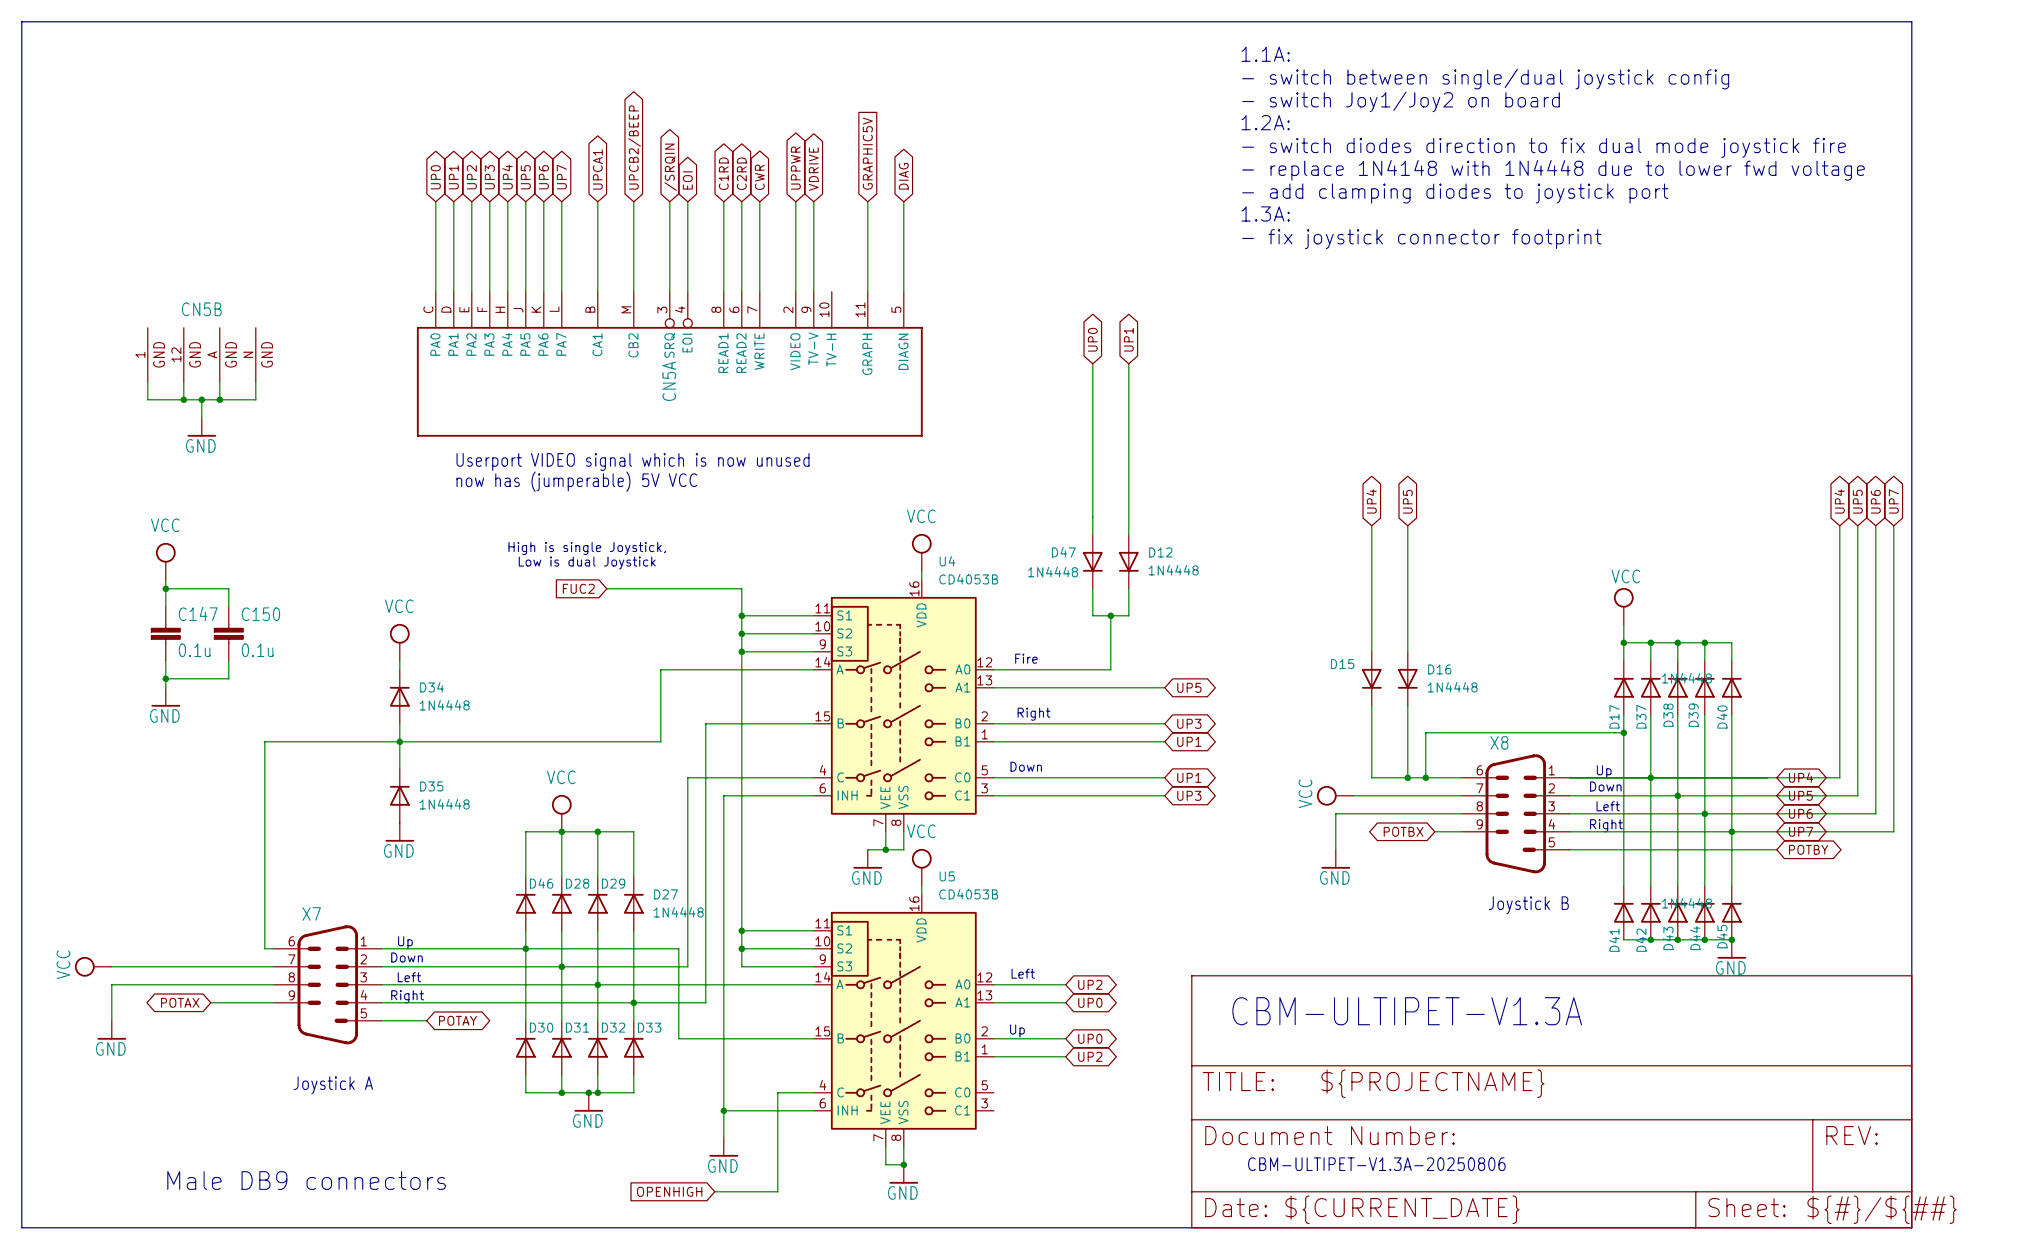
[picture p40: schematic Userport.kicad_sch]

Parts:
C147, C150: 0.1u; C0603
CN5: PORT_USER_PET_EDGE; MA156_12-2_USER
D12, D15, D16, D17, D27, D28, D29, D30, D31, D32, D33, D34, D35, D37, D38, D39, D40, D41, D42, D43, D44, D45, D46, D47: 1N4448; D_DO-35_SOD27_P7.62mm_Horizontal
U4, U5: CD4053B; SOIC-16_3.9x9.9mm_P1.27mm
X7, X8: M09-182; DSUB-9_Pins_Horizontal_P2.77x2.84mm_EdgePinOffset9.90mm_Hou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

Connections:
/SRQIN: CN5.3 (SRQ)
C1RD: CN5.8 (READ1)
C2RD: CN5.6 (READ2)
CWR: CN5.7 (WRITE)
DIAG: CN5.5 (DIAGN)
EOI: CN5.4 (EOI)
FUC2: U4.9 (S3), U4.10 (S2), U4.11 (S1), U5.9 (S3), U5.10 (S2), U5.11 (S1)
GND: C147.2, C150.2, CN5.1 (GND), CN5.12 (GND@1), CN5.A (GND@2), CN5.N (GND@3), D30.2 (A), D31.2 (A), D32.2 (A), D33.2 (A), D35.2 (A), D41.2 (A), D42.2 (A), D43.2 (A), D44.2 (A), D45.2 (A), U4.6 (INH), U4.7 (VEE), U4.8 (VSS), U5.6 (INH), U5.7 (VEE), U5.8 (VSS), X7.8, X8.8
GRAPHIC5V: CN5.11 (GRAPH)
unnamed: D12.1 (K), D47.1 (K), U4.12 (A0)
unnamed: D15.1 (K), D16.1 (K), D17.2 (A), D41.1 (K), X8.6
unnamed: D27.2 (A), D33.1 (K), U4.15 (B), X7.4
unnamed: D28.2 (A), D31.1 (K), U4.4 (C), X7.2
unnamed: D29.2 (A), D32.1 (K), U5.14 (A), X7.3
unnamed: D30.1 (K), D46.2 (A), U5.15 (B), X7.1
unnamed: D34.2 (A), D35.1 (K), U4.14 (A), X7.6
OPENHIGH: U5.4 (C)
POTAX: X7.9
POTAY: X7.5
POTBX: X8.9
POTBY: X8.5
UP0: CN5.C (PA0), D47.2 (A), U5.2 (B0), U5.13 (A1)
UP1: CN5.D (PA1), D12.2 (A), U4.1 (B1), U4.5 (C0)
UP2: CN5.E (PA2), U5.1 (B1), U5.12 (A0)
UP3: CN5.F (PA3), U4.2 (B0), U4.3 (C1)
UP4: CN5.H (PA4), D15.2 (A), D37.2 (A), D42.1 (K), X8.1
UP5: CN5.J (PA5), D16.2 (A), D38.2 (A), D43.1 (K), U4.13 (A1), X8.2
UP6: CN5.K (PA6), D39.2 (A), D44.1 (K), X8.3
UP7: CN5.L (PA7), D40.2 (A), D45.1 (K), X8.4
UPCA1: CN5.B (CA1)
UPCB2/BEEP: CN5.M (CB2)
UPPWR: CN5.2 (VIDEO)
VCC: C147.1, C150.1, D17.1 (K), D27.1 (K), D28.1 (K), D29.1 (K), D34.1 (K), D37.1 (K), D38.1 (K), D39.1 (K), D40.1 (K), D46.1 (K), U4.16 (VDD), U5.16 (VDD), X7.7, X8.7
VDRIVE: CN5.9 (TV-V)

Notes on the sheet:
Down
Userport VIDEO signal which is now unused now has (jumperable) 5V VCC
Joystick A
Left
1.1A: - switch between single/dual joystick config - switch Joy1/Joy2 on board 1.2A: - switch diodes direction to fix dual mode joystick fire - replace 1N4148 with 1N4448 due to lower fwd voltage - add clamping diodes to joystick port 1.3A: - fix joystick connector footprint
Male DB9 connectors
Right
CBM-ULTIPET-V1.3A
CBM-ULTIPET-V1.3A-20250806
High is single Joystick, Low is dual Joystick
Fire
Joystick B
