fachat/cbm_ultipet/Board/VRAM,_DAC.kicad_sch

## KiCad design Board/VRAM,_DAC.kicad_sch (2025-08-31)

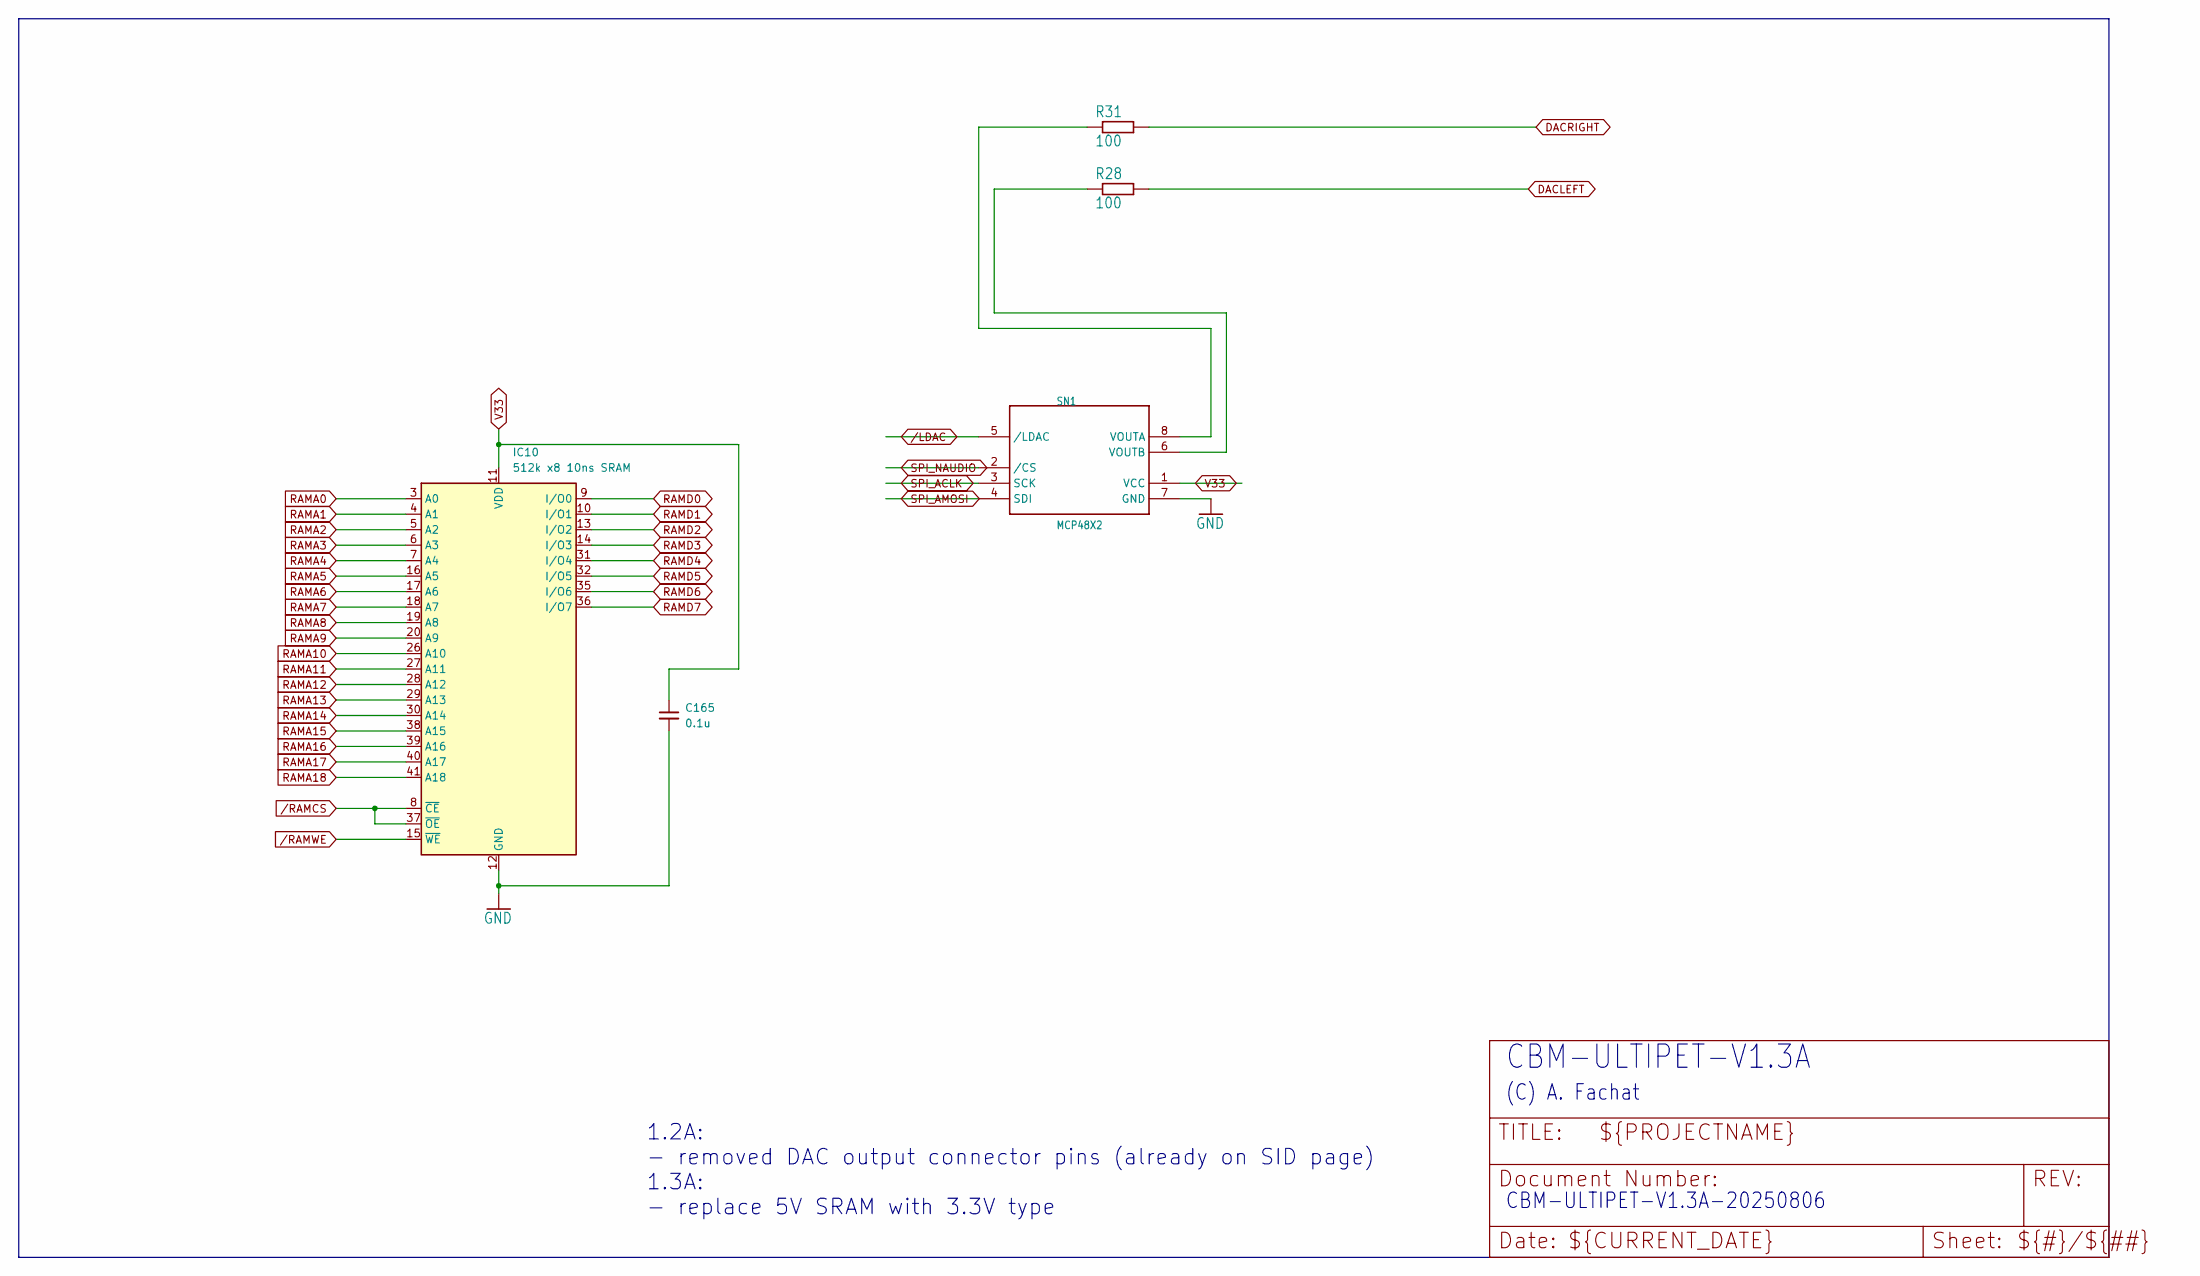
[picture p41: schematic VRAM,_DAC.kicad_sch]

Parts:
C165: 0.1u; C_0603_1608Metric
IC10: 512k x8 10ns SRAM; TSOP-II-44_10.16x18.41mm_P0.8mm
R28, R31: 100; 0204V
SN1: MCP48X2; SOIC8

Connections:
/LDAC: SN1.5 (/LDAC)
DACLEFT: R28.2
DACRIGHT: R31.2
GND: C165.2, IC10.12 (GND), IC10.34 (GND), SN1.7 (GND)
unnamed: R28.1, SN1.6 (VOUTB)
unnamed: R31.1, SN1.8 (VOUTA)
RAMA0: IC10.3 (A0)
RAMA1: IC10.4 (A1)
RAMA2: IC10.5 (A2)
RAMA3: IC10.6 (A3)
RAMA4: IC10.7 (A4)
RAMA5: IC10.16 (A5)
RAMA6: IC10.17 (A6)
RAMA7: IC10.18 (A7)
RAMA8: IC10.19 (A8)
RAMA9: IC10.20 (A9)
RAMA10: IC10.26 (A10)
RAMA11: IC10.27 (A11)
RAMA12: IC10.28 (A12)
RAMA13: IC10.29 (A13)
RAMA14: IC10.30 (A14)
RAMA15: IC10.38 (A15)
RAMA16: IC10.39 (A16)
RAMA17: IC10.40 (A17)
RAMA18: IC10.41 (A18)
RAMD0: IC10.9 (I/O0)
RAMD1: IC10.10 (I/O1)
RAMD2: IC10.13 (I/O2)
RAMD3: IC10.14 (I/O3)
RAMD4: IC10.31 (I/O4)
RAMD5: IC10.32 (I/O5)
RAMD6: IC10.35 (I/O6)
RAMD7: IC10.36 (I/O7)
SPI_ACLK: SN1.3 (SCK)
SPI_AMOSI: SN1.4 (SDI)
SPI_NAUDIO: SN1.2 (/CS)
V33: C165.1, IC10.11 (VDD), IC10.33 (VDD), SN1.1 (VCC)
/RAMCS: IC10.8 (~CE), IC10.37 (~OE)
/RAMWE: IC10.15 (~WE)

Notes on the sheet:
(C) A. Fachat
CBM-ULTIPET-V1.3A
1.2A: - removed DAC output connector pins (already on SID page) 1.3A: - replace 5V SRAM with 3.3V type
CBM-ULTIPET-V1.3A-20250806
